acwright/6502-COB/CAD/Models/GPIO Helper/Rev 1.0/GPIO Helper.step

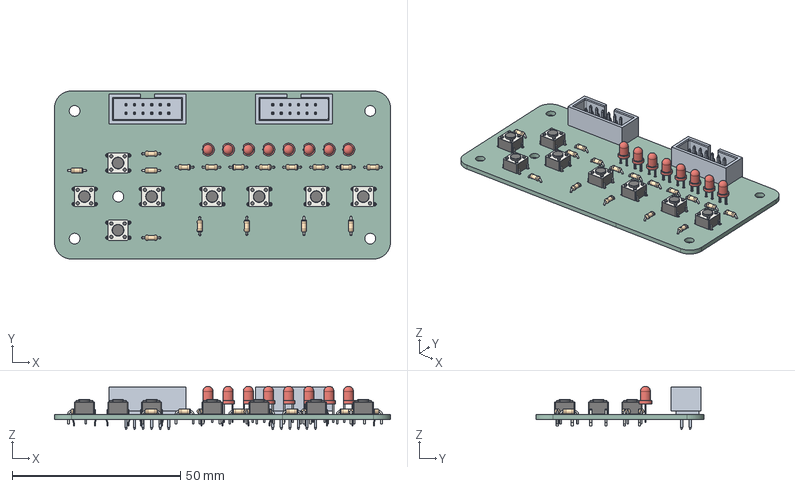
[picture p18: CAD file, 2026-05-05]
CAD/Models/GPIO Helper/Rev 1.0/GPIO Helper.step
100.0 x 50.0 x 12.9 mm
LED_D3.0mm x 8
R_Axial_DIN0204_L3.6mm_D1.6mm_P5.08mm_Horizontal x 16
SW_PUSH_6mm x 8
GPIO Helper_PCB
