acwright/6502-COB/CAD/Models/Joystick Helper/Rev 1.0/Joystick Helper.step

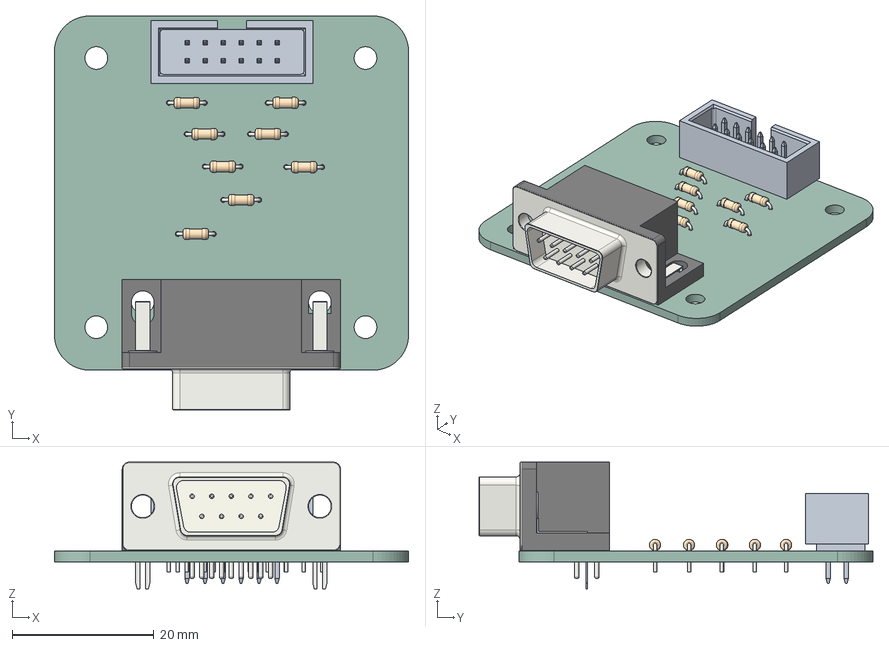
[picture p19: CAD file, 2026-05-05]
CAD/Models/Joystick Helper/Rev 1.0/Joystick Helper.step
50.0 x 55.6 x 17.9 mm
R_Axial_DIN0204_L3.6mm_D1.6mm_P5.08mm_Horizontal x 8
DSUB-9_Pins_Horizontal_P2.77x2.84mm_EdgePinOffset7.70mm_Housed_ MountingHolesOffset9.12mm
Joystick Helper_PCB
