acwright/6502-COB/CAD/Models/LCD Board/Rev 1.0/LCD Board.step

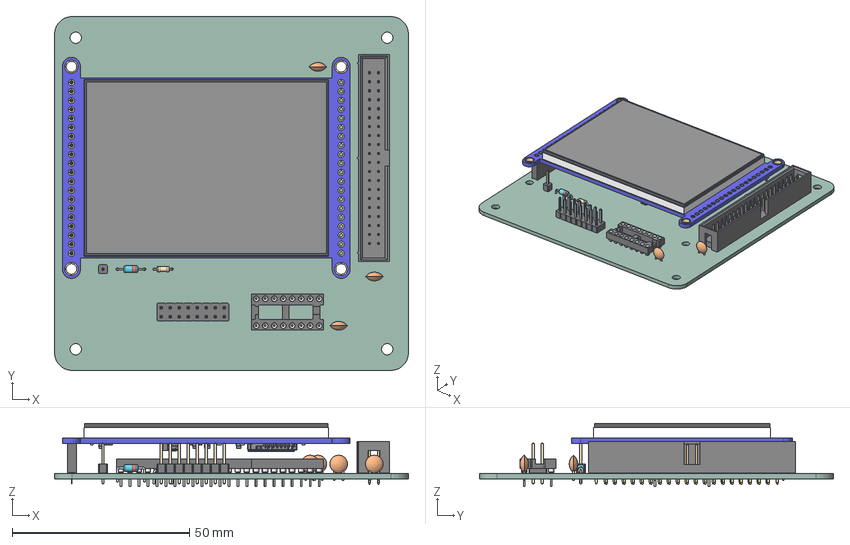
[picture p22: CAD file, 2026-05-05]
CAD/Models/LCD Board/Rev 1.0/LCD Board.step
100.0 x 100.0 x 17.9 mm
C_Disc_D5.0mm_W2.5mm_P2.50mm x 4
6871xx14022_PIN x 50
6871xx14022_Patte
6871xx14022_Patte_2
68715014022_CAP
6871xx149022_Pin x 18
6871xx149022_Patte
6871xx149022_Patte2
687118149022_Actuator
74LVC245 x 2
PinSocket_1x20_P2.54mm_Vertical
PinHeader_1x01_P2.54mm_Vertical
R_Axial_DIN0204_L3.6mm_D1.6mm_P5.08mm_Horizontal
DIP-16_W7.62mm_Socket
D_DO-35_SOD27_P7.62mm_Horizontal x 2
DIP-40_W15.24mm_Socket
PinHeader_2x08_P2.54mm_Vertical
6120xx21621_PIN x 40
LCD Board_PCB
