acwright/6502-COB/CAD/Models/LCD Card/Rev 1.0/LCD Card.step

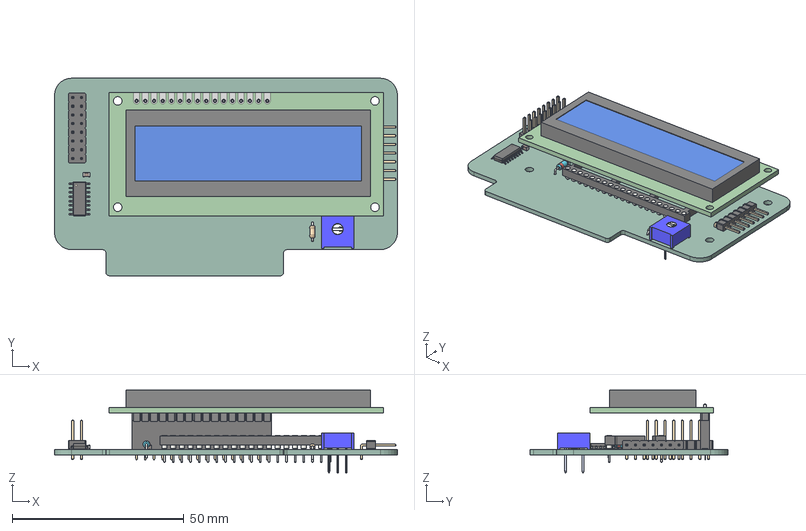
[picture p23: CAD file, 2026-05-05]
CAD/Models/LCD Card/Rev 1.0/LCD Card.step
100.0 x 57.6 x 24.2 mm
lcd 16_2 HD44780
dupont_pin_16
PinSocket_1x16_P2.54mm_Vertical
D_DO-35_SOD27_P7.62mm_Horizontal
3386F-1-103LF
R_Axial_DIN0204_L3.6mm_D1.6mm_P5.08mm_Horizontal
SOIC-16_3.9x9.9mm_P1.27mm
DIP-40_W15.24mm_Socket
PinHeader_2x08_P2.54mm_Vertical
C_0805_2012Metric x 2
PinHeader_1x07_P2.54mm_Horizontal
LCD Card_PCB
