acwright/6502-COB/CAD/Models/Prototype Card/Rev 1.0/Prototype Card.step

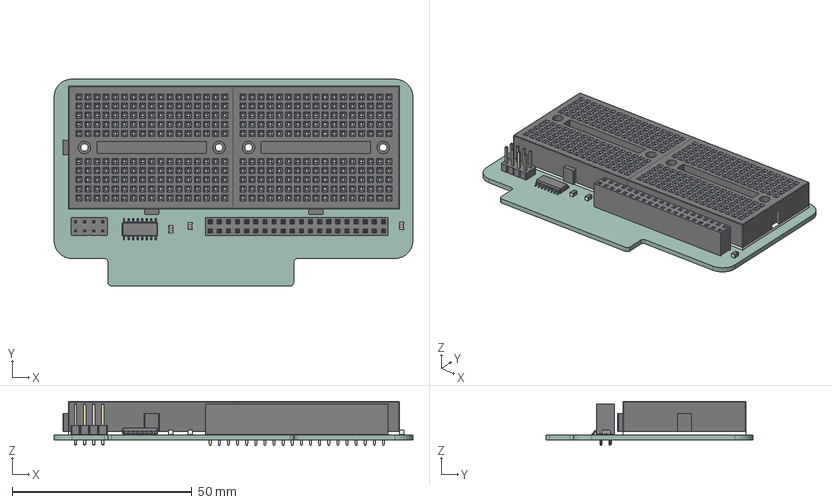
[picture p25: CAD file, 2026-05-05]
CAD/Models/Prototype Card/Rev 1.0/Prototype Card.step
100.0 x 57.6 x 12.3 mm
Mini-Black x 2
C_0805_2012Metric x 3
PinSocket_2x20_P2.54mm_Vertical
PinHeader_2x04_P2.54mm_Vertical
SOIC-16_3.9x9.9mm_P1.27mm
Prototype Card_PCB
