acwright/6502-COB/CAD/Models/PS2 Helper/Rev 1.0/PS2 Helper.step

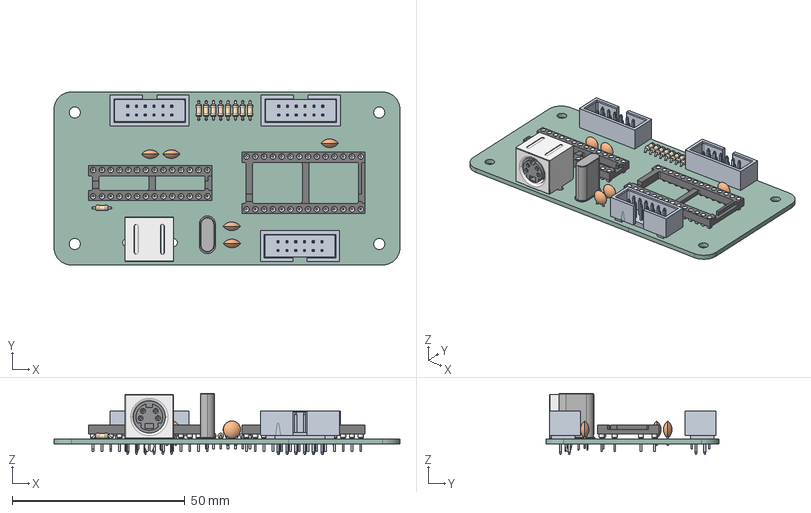
[picture p26: CAD file, 2026-05-05]
CAD/Models/PS2 Helper/Rev 1.0/PS2 Helper.step
100.0 x 50.0 x 17.7 mm
KMDGX-6S-BS
C_Disc_D5.0mm_W2.5mm_P2.50mm x 5
R_Axial_DIN0204_L3.6mm_D1.6mm_P5.08mm_Horizontal x 9
DIP-28_W7.62mm_Socket
DIP-28_W15.24mm_Socket
Crystal_HC49-U_Vertical
PS2 Helper_PCB
