acwright/6502-COB/CAD/Models/Serial Card/Rev 1.0/Serial Card.step

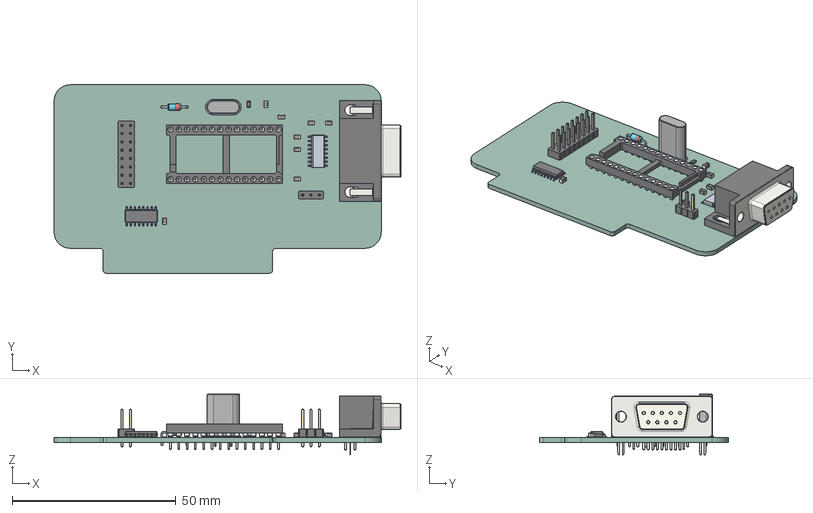
[picture p29: CAD file, 2026-05-05]
CAD/Models/Serial Card/Rev 1.0/Serial Card.step
106.0 x 57.6 x 18.5 mm
C_0805_2012Metric x 8
Crystal_HC49-U_Vertical
R_0805_2012Metric
Serial Card 1.9
SOIC-16_3.9x9.9mm_P1.27mm
DSUB-9_Socket_Horizontal_P2.77x2.84mm_EdgePinOffset7.70mm_Housed_ MountingHolesOffset9.12mm
DIP-28_W15.24mm_Socket
D_DO-35_SOD27_P7.62mm_Horizontal
PinHeader_2x08_P2.54mm_Vertical
PinHeader_1x03_P2.54mm_Vertical
Serial Card_PCB
