acwright/6502-COB/CAD/Models/Sound Card/Rev 1.0/Sound Card.step

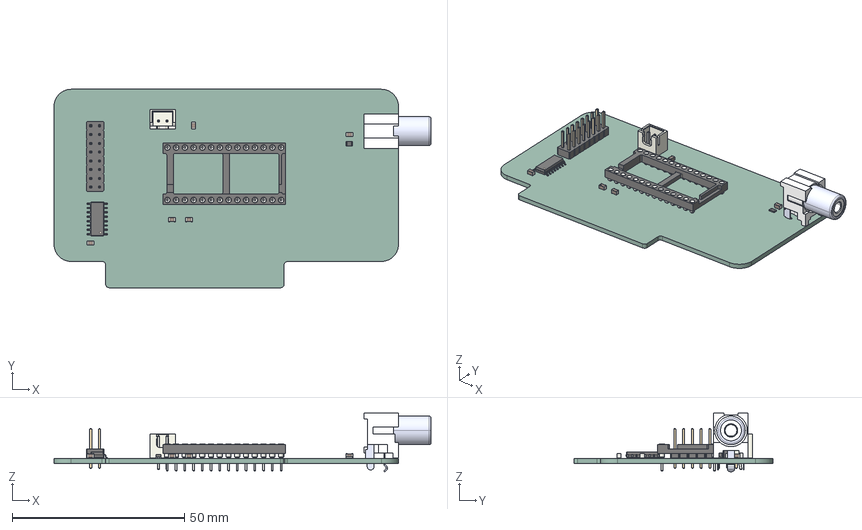
[picture p30: CAD file, 2026-05-05]
CAD/Models/Sound Card/Rev 1.0/Sound Card.step
109.4 x 57.6 x 17.0 mm
PinHeader_2x08_P2.54mm_Vertical
C_0805_2012Metric x 5
SOIC-16_3.9x9.9mm_P1.27mm
PJRAN1X1U04X-edit
R_0805_2012Metric
JST_XH_B2B-XH-A_1x02_P2.50mm_Vertical
DIP-28_W15.24mm_Socket
Sound Card_PCB
