acwright/6502-COB/CAD/Models/Storage Card Pro/Rev 1.0/Storage Card Pro.step

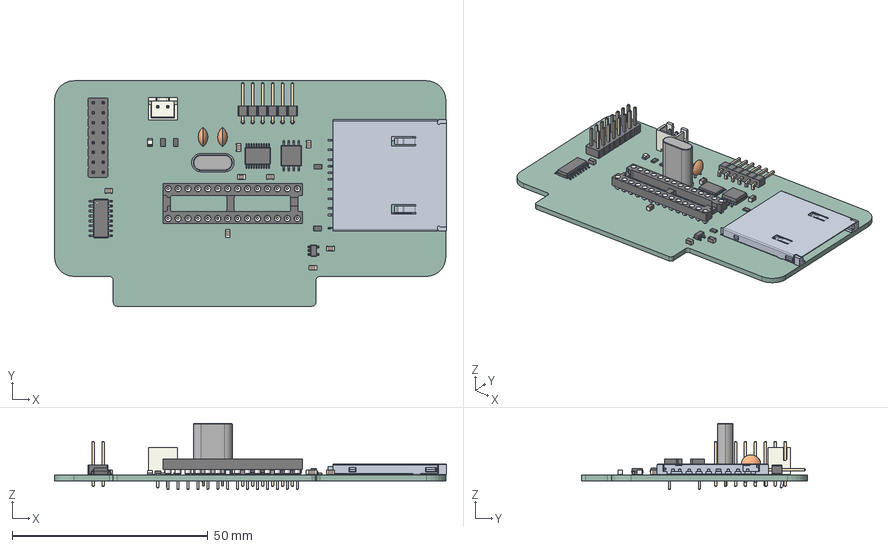
[picture p31: CAD file, 2026-05-05]
CAD/Models/Storage Card Pro/Rev 1.0/Storage Card Pro.step
100.2 x 57.6 x 16.9 mm
C_0805_2012Metric x 8
R_0805_2012Metric x 4
JST_XH_B2B-XH-A_1x02_P2.50mm_Vertical
C_Disc_D5.0mm_W2.5mm_P2.50mm x 2
SOT-23-5
SOIC-16_3.9x9.9mm_P1.27mm
PinHeader_2x08_P2.54mm_Vertical
TSSOP-20_4.4x6.5mm_P0.65mm
Storage Card Pro 1.13.1
PinHeader_1x06_P2.54mm_Horizontal
Crystal_HC49-U_Vertical
DIP-28_W7.62mm_Socket
SOIC-8_5.3x5.3mm_P1.27mm
LED_0805_2012Metric
Storage Card Pro_PCB
