acwright/6502-COB/CAD/Models/VERA Helper/Rev 1.0/VERA Helper.step

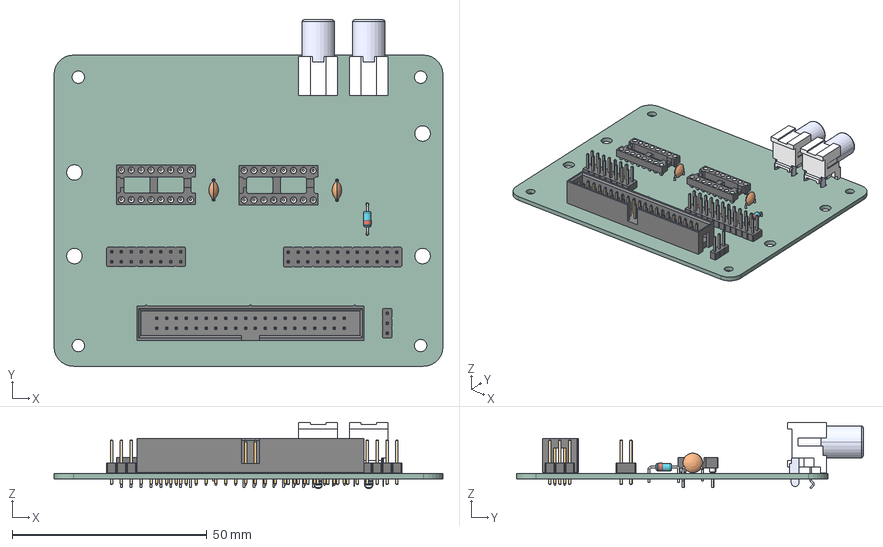
[picture p32: CAD file, 2026-05-05]
CAD/Models/VERA Helper/Rev 1.0/VERA Helper.step
100.0 x 89.1 x 17.0 mm
PinHeader_1x03_P2.54mm_Vertical
DIP-16_W7.62mm_Socket x 2
PinHeader_2x12_P2.54mm_Vertical
C_Disc_D5.0mm_W2.5mm_P5.00mm x 2
PJRAN1X1U04X-edit x 2
6120xx21621_PIN x 40
PinHeader_2x08_P2.54mm_Vertical
D_DO-35_SOD27_P7.62mm_Horizontal
VERA Helper_PCB
