acwright/6502-COB/CAD/Models/VGA Card Pro/Rev 1.0/VGA Card Pro.step

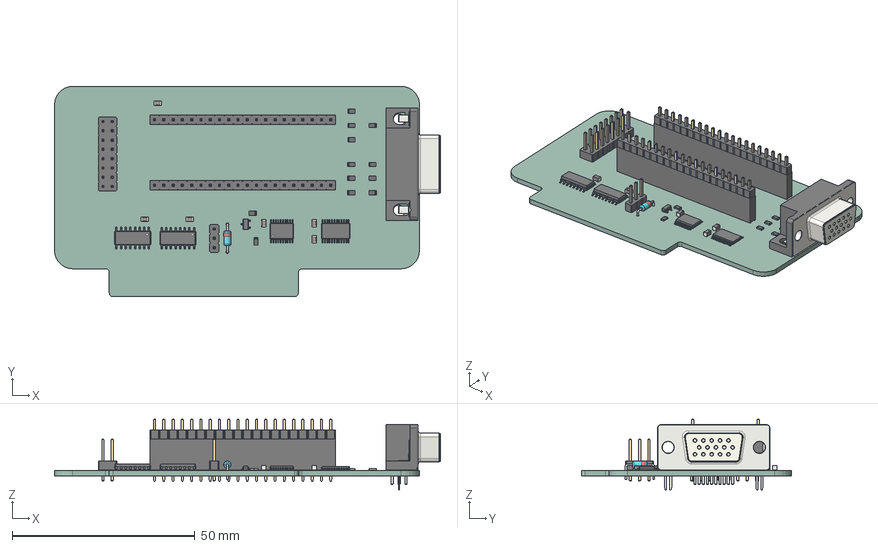
[picture p33: CAD file, 2026-05-05]
CAD/Models/VGA Card Pro/Rev 1.0/VGA Card Pro.step
105.8 x 57.6 x 19.4 mm
R_0805_2012Metric x 12
DSUB-15-HD_Socket_Horizontal_P2.29x1.90mm_EdgePinOffset3.03mm_Housed_ MountingHolesOffset4.94mm
TSSOP-24_4.4x7.8mm_P0.65mm
Raspberry Pi Pico
PinSocket_1x20_P2.54mm_Vertical x 2
PinHeader_1x20_P2.54mm_Vertical x 2
SOT-23
D_DO-35_SOD27_P7.62mm_Horizontal
C_0805_2012Metric x 6
PinHeader_2x08_P2.54mm_Vertical
PinHeader_1x03_P2.54mm_Vertical
TSSOP-20_4.4x6.5mm_P0.65mm
SOIC-16_3.9x9.9mm_P1.27mm x 2
VGA Card Pro_PCB
