acwright/6502-COB/CAD/Models/Video Card Pro/Rev 1.0/Video Card Pro.step

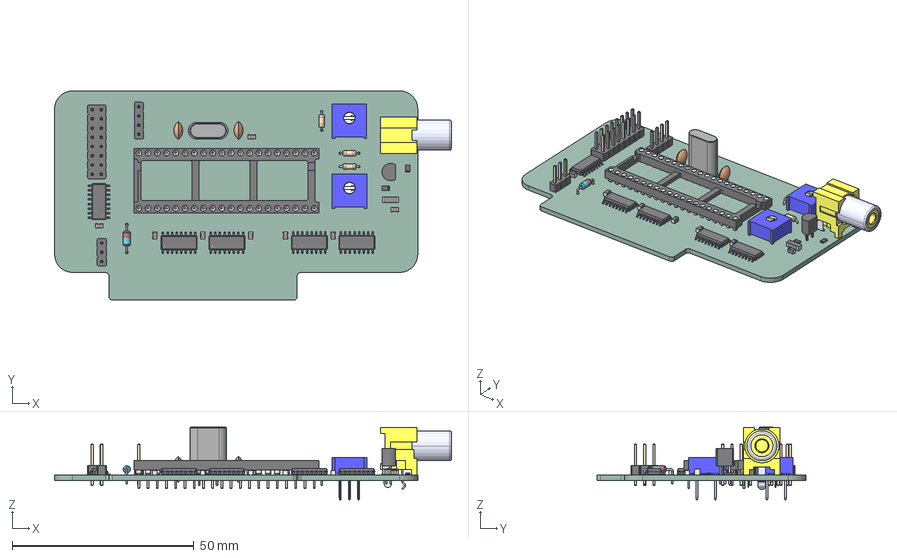
[picture p34: CAD file, 2026-05-05]
CAD/Models/Video Card Pro/Rev 1.0/Video Card Pro.step
109.3 x 57.6 x 20.0 mm
C_Disc_D5.0mm_W2.5mm_P2.50mm x 2
SOIC-16_3.9x9.9mm_P1.27mm x 5
TO-92
PinHeader_1x04_P2.54mm_Vertical
R_Axial_DIN0204_L3.6mm_D1.6mm_P5.08mm_Horizontal x 3
C_0805_2012Metric x 8
PinHeader_1x03_P2.54mm_Vertical
Crystal_HC49-U_Vertical
PJRAN1X1U04X-edit
D_DO-35_SOD27_P7.62mm_Horizontal
R_0805_2012Metric x 2
PinHeader_2x08_P2.54mm_Vertical
3386F-1-103LF x 2
DIP-40_W15.24mm_Socket
L_1806_4516Metric
Video Card Pro_PCB
