acwright/6502-COB/CAD/Models/Video Card/Rev 1.0/Video Card.step

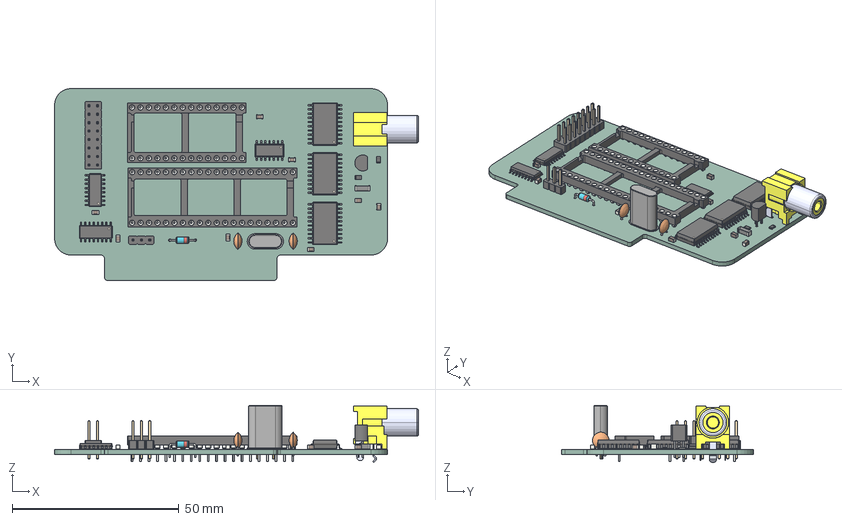
[picture p35: CAD file, 2026-05-05]
CAD/Models/Video Card/Rev 1.0/Video Card.step
109.3 x 57.6 x 17.1 mm
C_Disc_D5.0mm_W2.5mm_P2.50mm x 2
SOIC-20W_7.5x12.8mm_P1.27mm x 3
TO-92
C_0805_2012Metric x 8
DIP-28_W15.24mm_Socket
DIP-40_W15.24mm_Socket
PinHeader_1x03_P2.54mm_Vertical
Crystal_HC49-U_Vertical
SOIC-16_3.9x9.9mm_P1.27mm x 2
PJRAN1X1U04X-edit
D_DO-35_SOD27_P7.62mm_Horizontal
R_0805_2012Metric x 2
SO-14_3.9x8.65mm_P1.27mm
PinHeader_2x08_P2.54mm_Vertical
L_1806_4516Metric
Video Card_PCB
