acwright/6502-COB/Models/400MSP1R6BLKM6QE.step

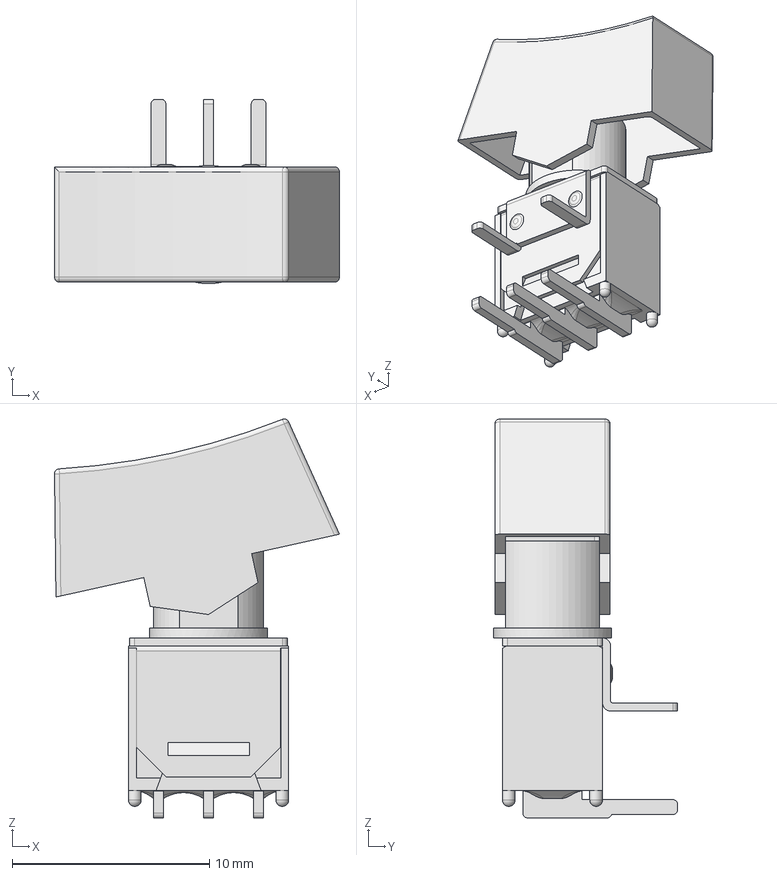
[picture p36: CAD file, 2026-06-21]
Models/400MSP1R6BLKM6QE.step
14.5 x 9.35 x 20.2 mm
