acwright/6502-COB/CAD/Bases/Center Support Retainer.stl

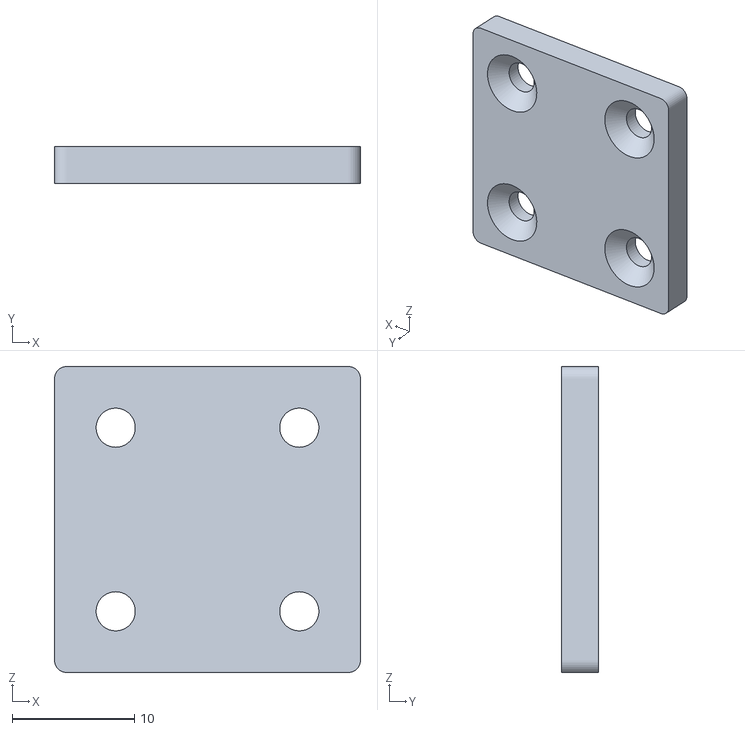
[picture p37: CAD file, 2026-05-05]
CAD/Bases/Center Support Retainer.stl
25.0 x 3.00 x 25.0
