acwright/6502-COB/CAD/Jigs/Keyboard Helper Jig Right.3mf

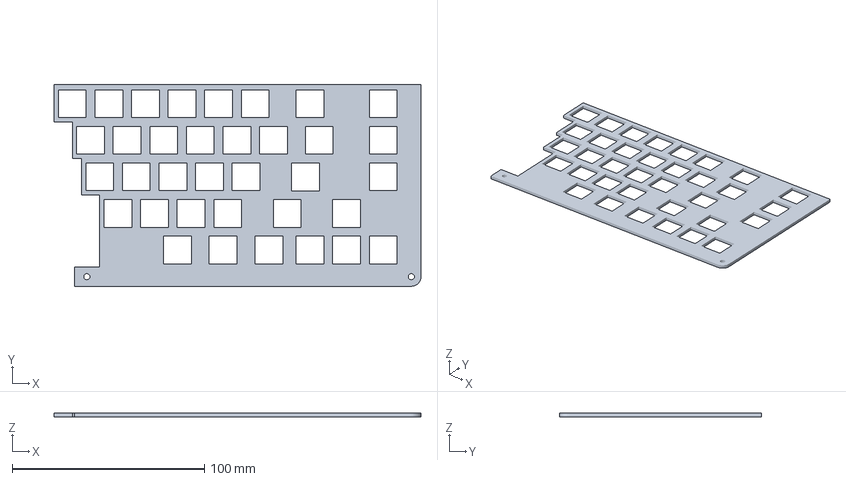
[picture p38: CAD file, 2026-05-19]
CAD/Jigs/Keyboard Helper Jig Right.3mf
191.1 x 105.0 x 2.00 mm
