acwright/6502-COB/CAD/Bases/Corner.3mf

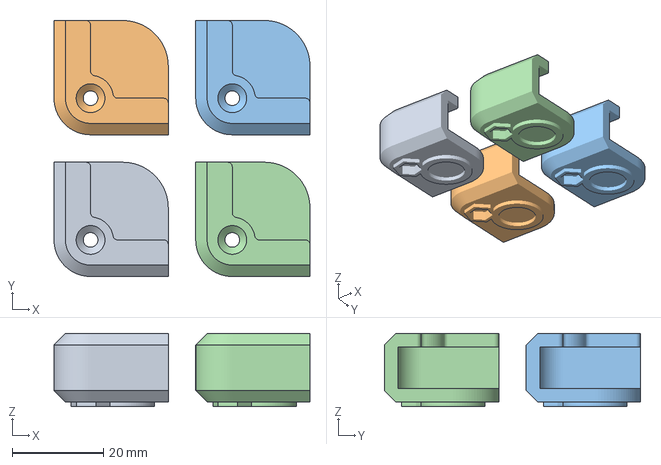
[picture p39: CAD file, 2026-05-05]
CAD/Bases/Corner.3mf
56.0 x 56.0 x 16.0 mm
