acwright/6502-COB/Models/KMDGX-6S-BS.step

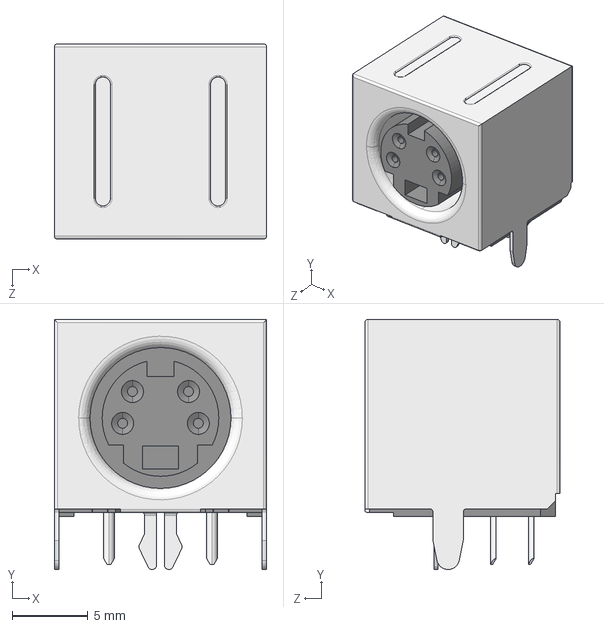
[picture p40: CAD file, 2026-05-05]
Models/KMDGX-6S-BS.step
14.0 x 16.5 x 12.9 mm
