acwright/6502-COB/CAD/Bases/Plate.stl

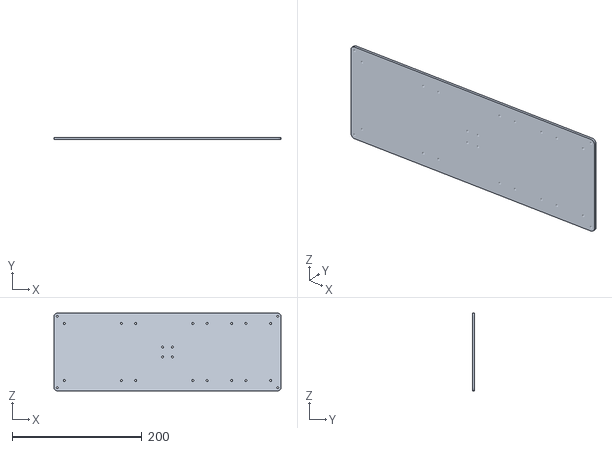
[picture p41: CAD file, 2026-05-05]
CAD/Bases/Plate.stl
350.0 x 3.00 x 120.0
