acwright/6502-COB/Models/HRO_TYPE-C-31-M-12.step

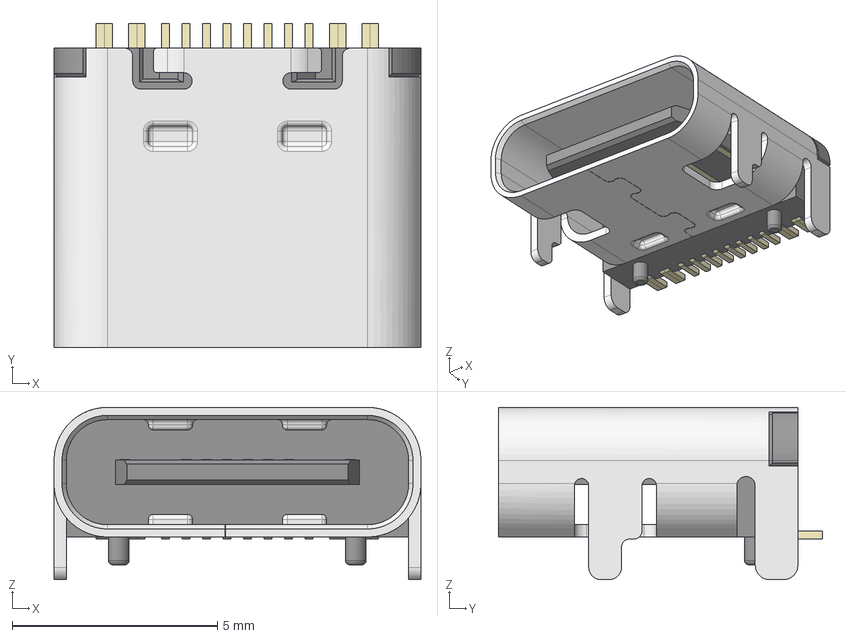
[picture p42: CAD file, 2026-05-05]
Models/HRO_TYPE-C-31-M-12.step
8.95 x 7.90 x 4.20 mm
