acwright/6502-COB/CAD/Bases/Button.3mf

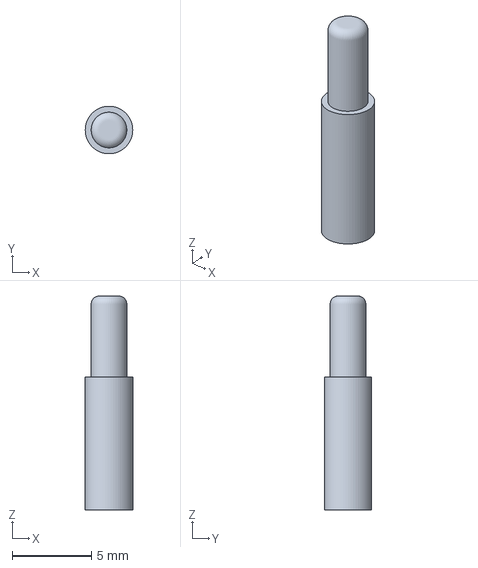
[picture p43: CAD file, 2026-05-05]
CAD/Bases/Button.3mf
3.00 x 3.00 x 13.5 mm
