acwright/6502-COB/Models/CherryMX.step

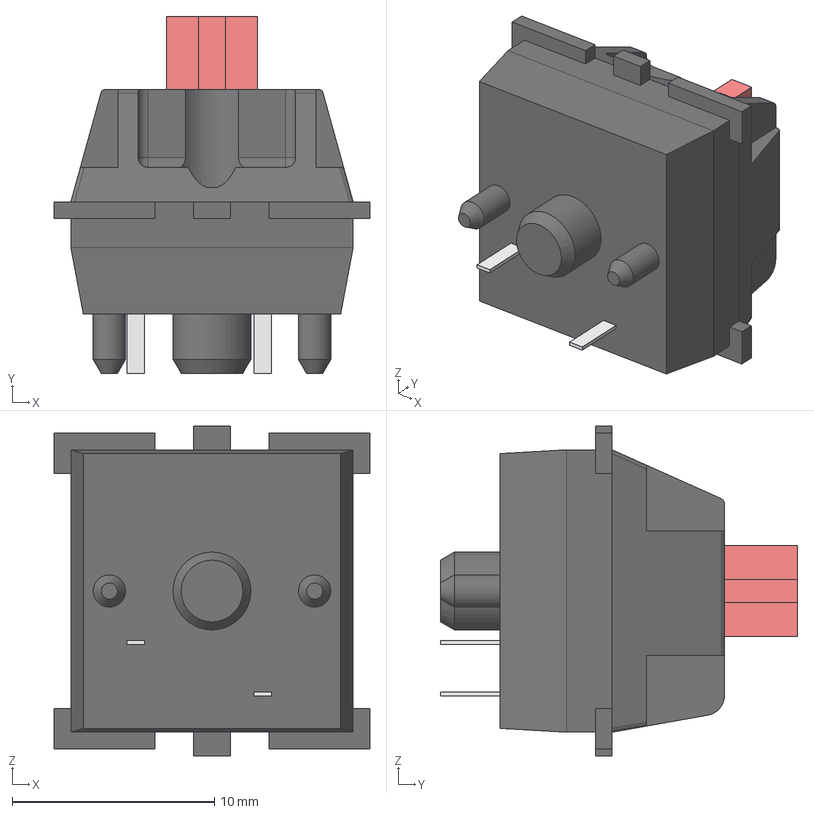
[picture p44: CAD file, 2026-05-05]
Models/CherryMX.step
15.6 x 17.7 x 16.3 mm
