acwright/6502-COB/Models/CFH-L3C1-1.step

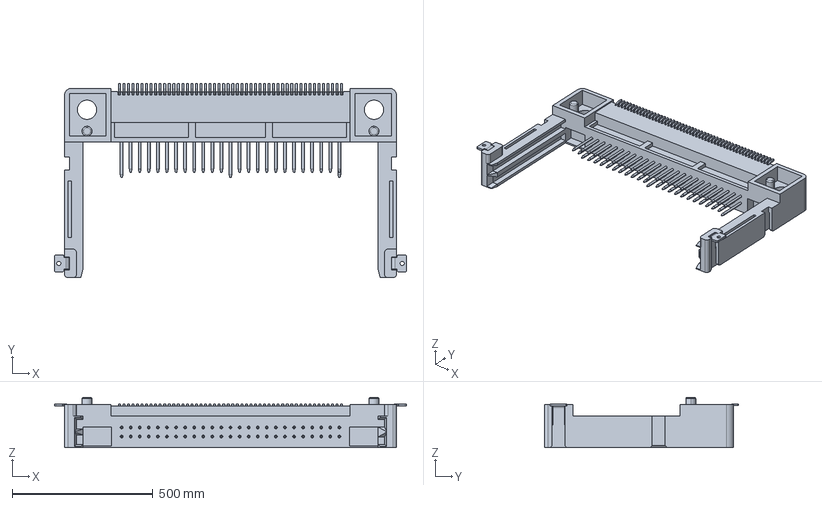
[picture p45: CAD file, 2026-05-05]
Models/CFH-L3C1-1.step
1251.2 x 690.9 x 179.1 mm
