acwright/6502-COB/Models/MAX232D.step

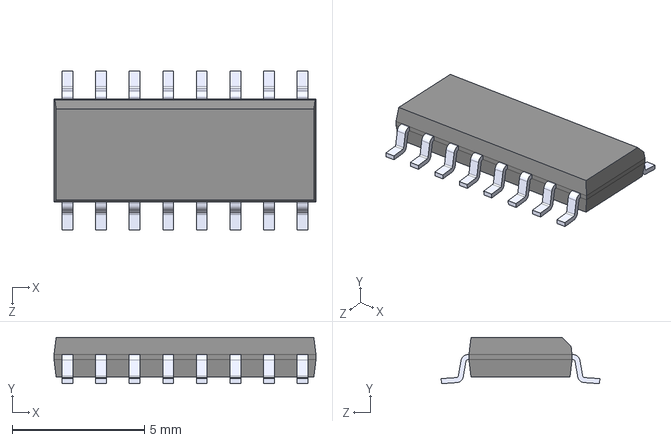
[picture p46: CAD file, 2026-05-05]
Models/MAX232D.step
9.90 x 1.75 x 6.00 mm
