acwright/6502-COB/Models/XKB5858.step

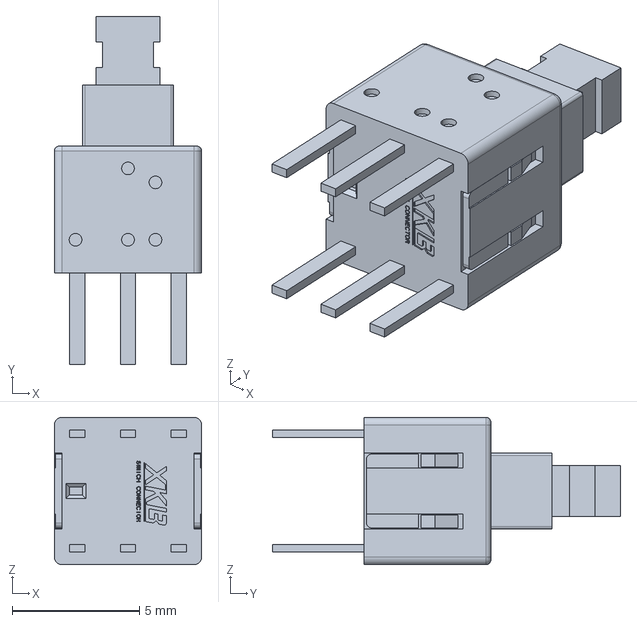
[picture p47: CAD file, 2026-05-05]
Models/XKB5858.step
5.80 x 13.7 x 5.80 mm
