acwright/6502-COB/Models/Adafruit 2.8 TFT LCD.step

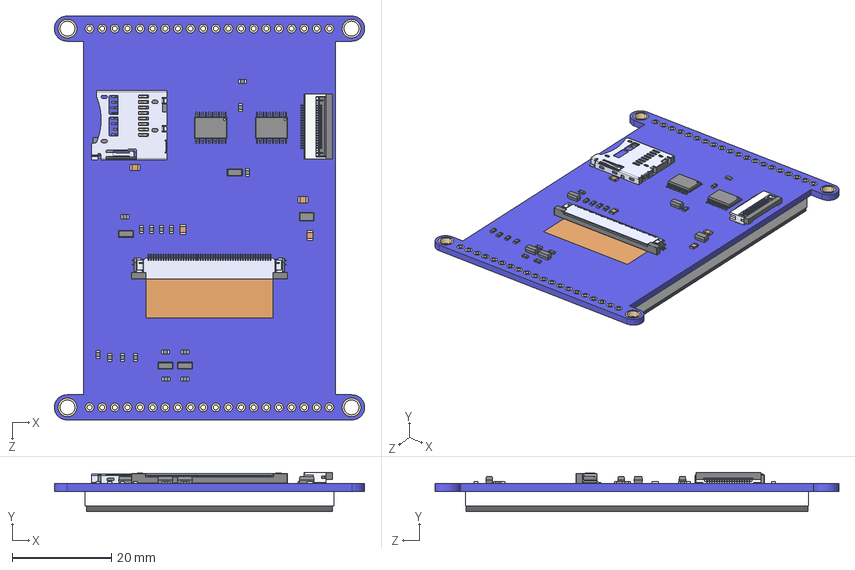
[picture p48: CAD file, 2026-05-05]
Models/Adafruit 2.8 TFT LCD.step
62.4 x 7.90 x 81.3 mm
6871xx14022_PIN x 50
6871xx14022_Patte
6871xx14022_Patte_2
68715014022_CAP
6871xx149022_Pin x 18
6871xx149022_Patte
6871xx149022_Patte2
687118149022_Actuator
74LVC245 x 2
