acwright/6502-COB/Models/TS-1187A-B-A-B.step

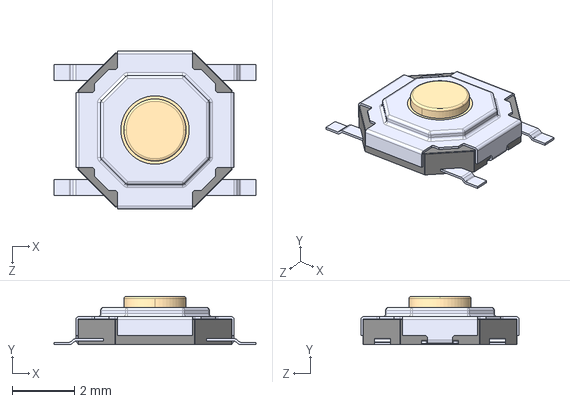
[picture p49: CAD file, 2026-05-05]
Models/TS-1187A-B-A-B.step
6.50 x 1.55 x 5.10 mm
