acwright/6502-COB/Models/5-5530843-4.step

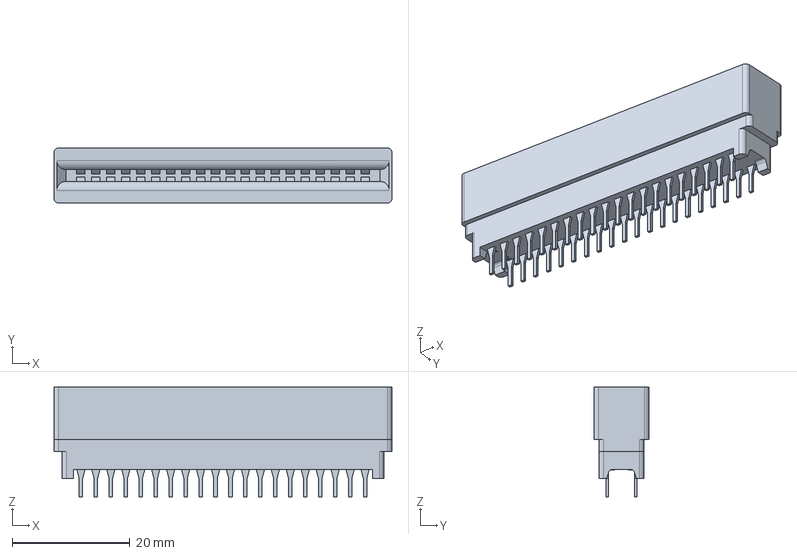
[picture p50: CAD file, 2026-05-05]
Models/5-5530843-4.step
57.4 x 9.35 x 18.7 mm
