acwright/6502-COB/Models/PJRAN1X1U02X.step

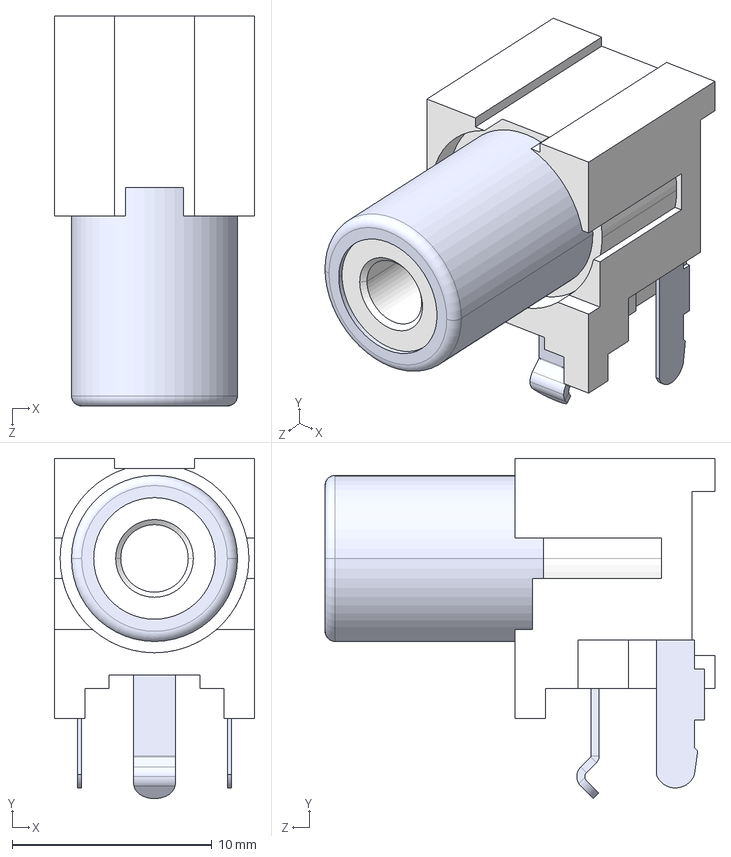
[picture p51: CAD file, 2026-05-05]
Models/PJRAN1X1U02X.step
10.0 x 17.0 x 19.5 mm
