acwright/6502-COB/Models/Mini-Black.step

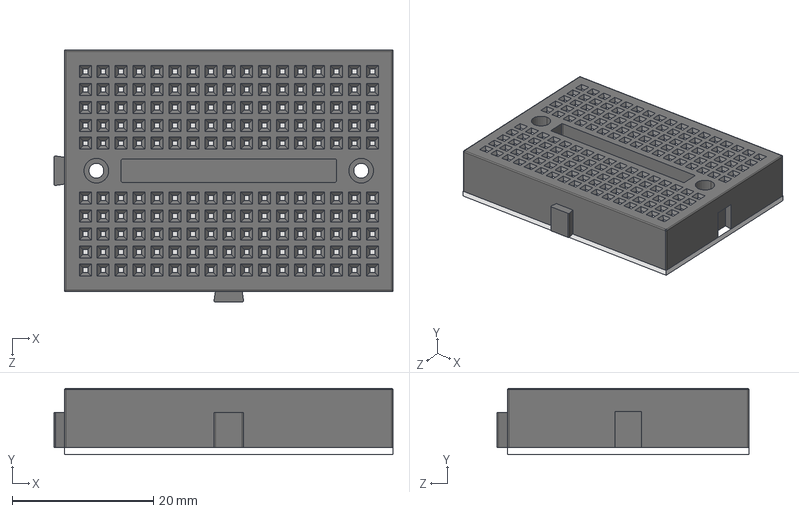
[picture p52: CAD file, 2026-05-05]
Models/Mini-Black.step
48.0 x 9.40 x 35.7 mm
