acwright/6502-COB/Models/3386F-1-103LF.step

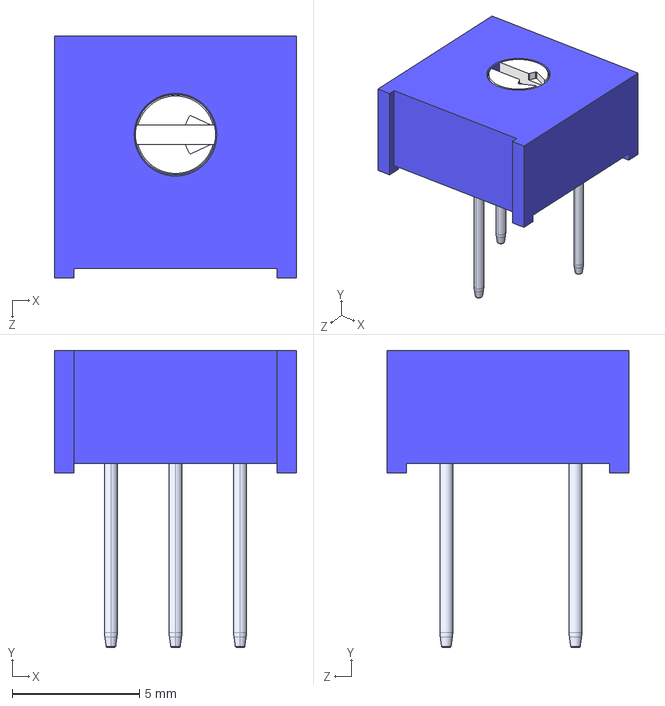
[picture p53: CAD file, 2026-05-05]
Models/3386F-1-103LF.step
9.53 x 11.7 x 9.53 mm
