acwright/6502-COB/Models/BAT-HLD-001-THM.step

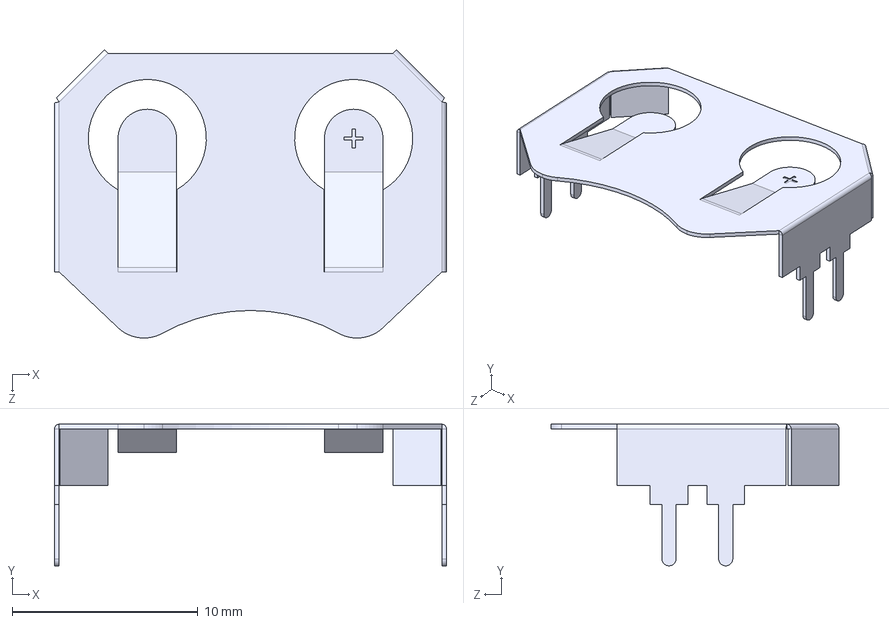
[picture p54: CAD file, 2026-05-05]
Models/BAT-HLD-001-THM.step
21.1 x 7.62 x 15.5 mm
