acwright/6502-COB/Schematics/Storage Card/Rev 1.0/Storage Card.pdf

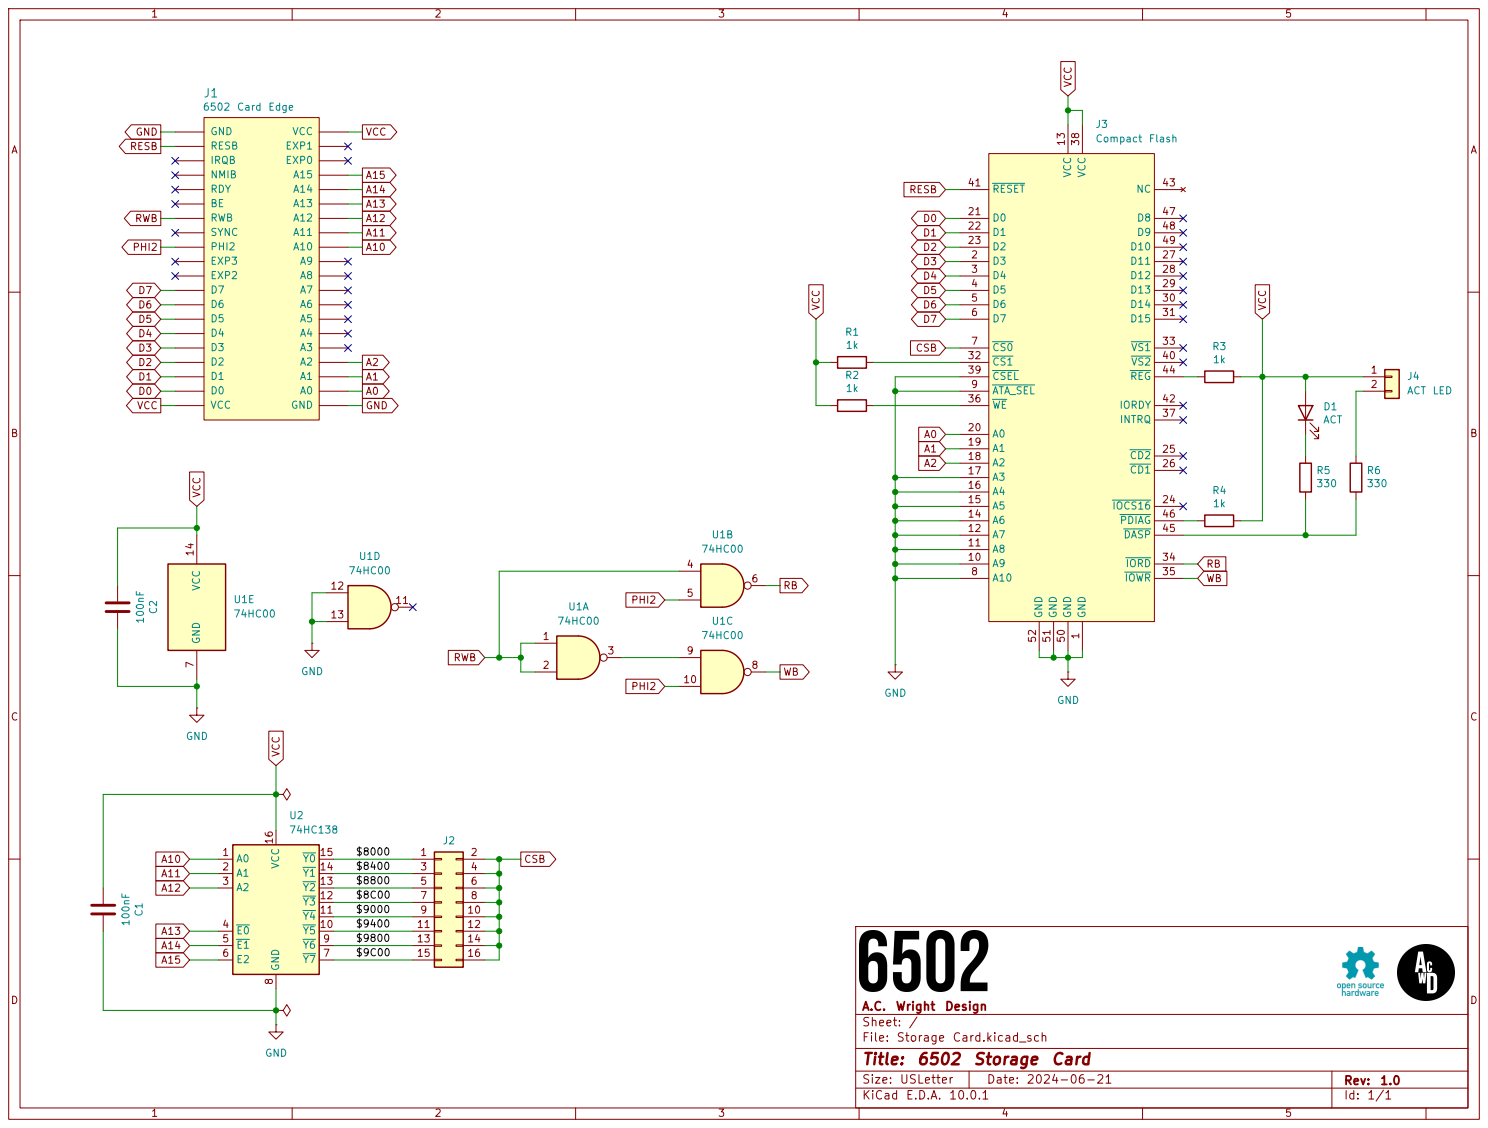
[picture p67: page 1]

Size: USLetter | Rev: 1.0
KiCad E.D.A. 10.0.1 | Id: 1/1
