acwright/6502-COB/Schematics/Backplane Pro/Rev 1.0/Backplane Pro.pdf

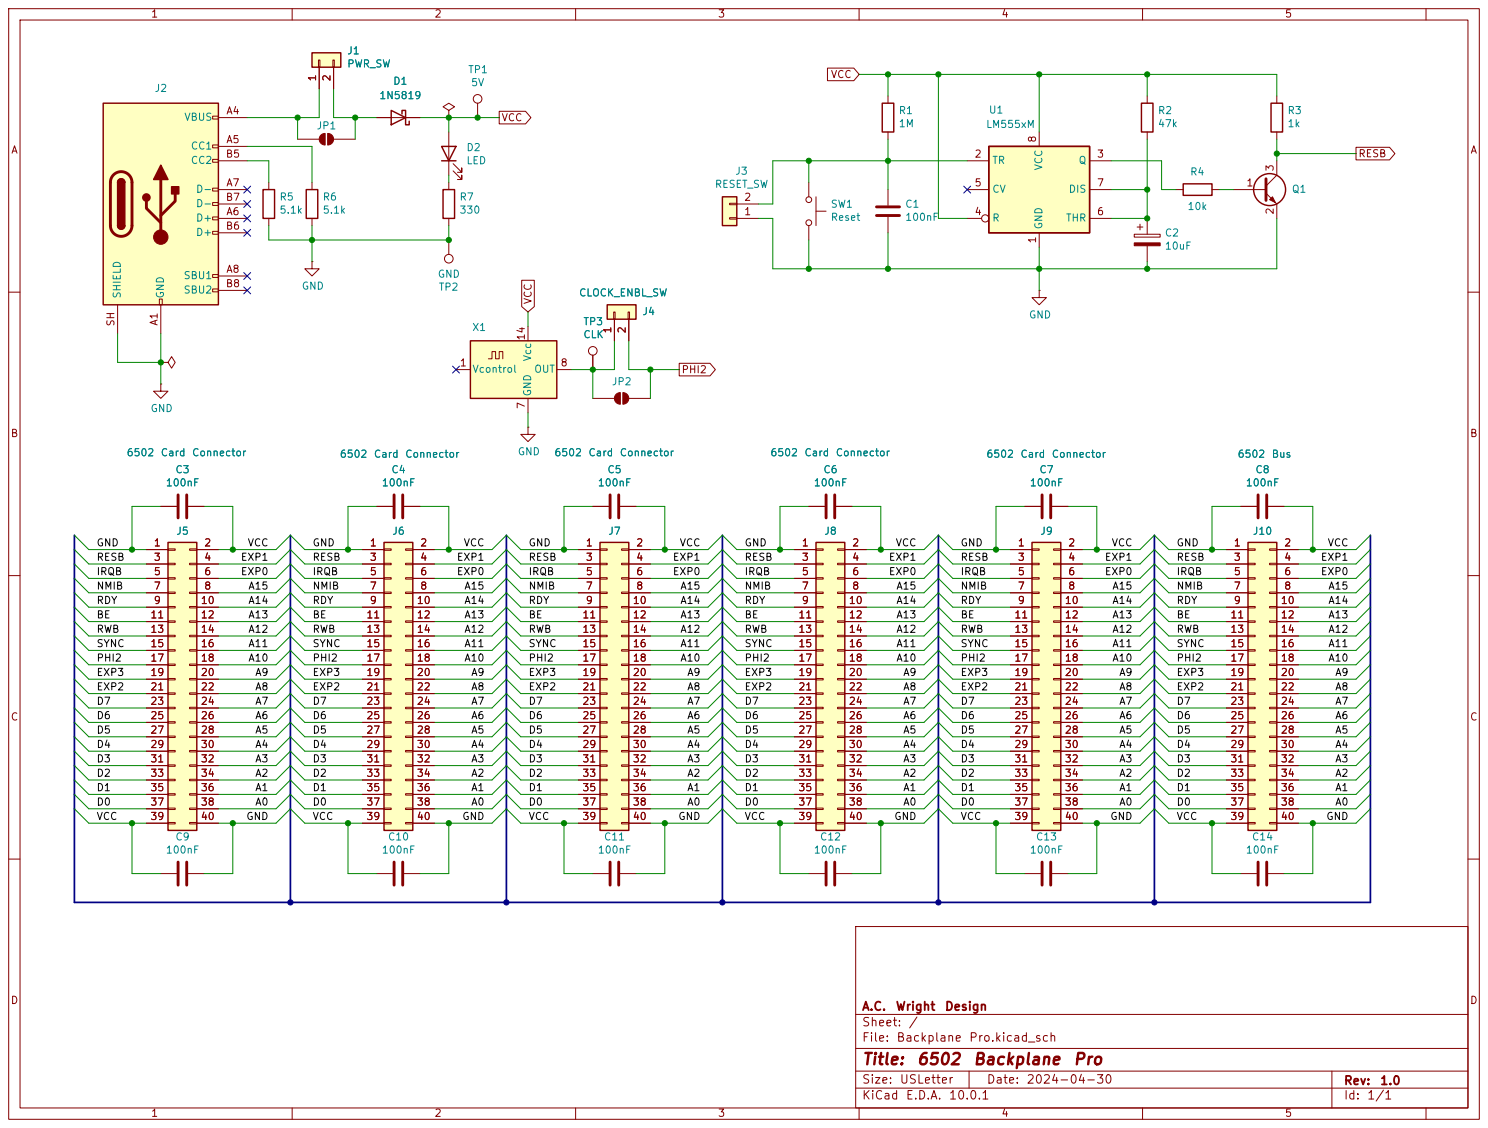
[picture p68: page 1]

Size: USLetter | Rev: 1.0
KiCad E.D.A. 10.0.1 | Id: 1/1
