acwright/6502-COB/Schematics/CPU Card/Rev 1.0/CPU Card.pdf

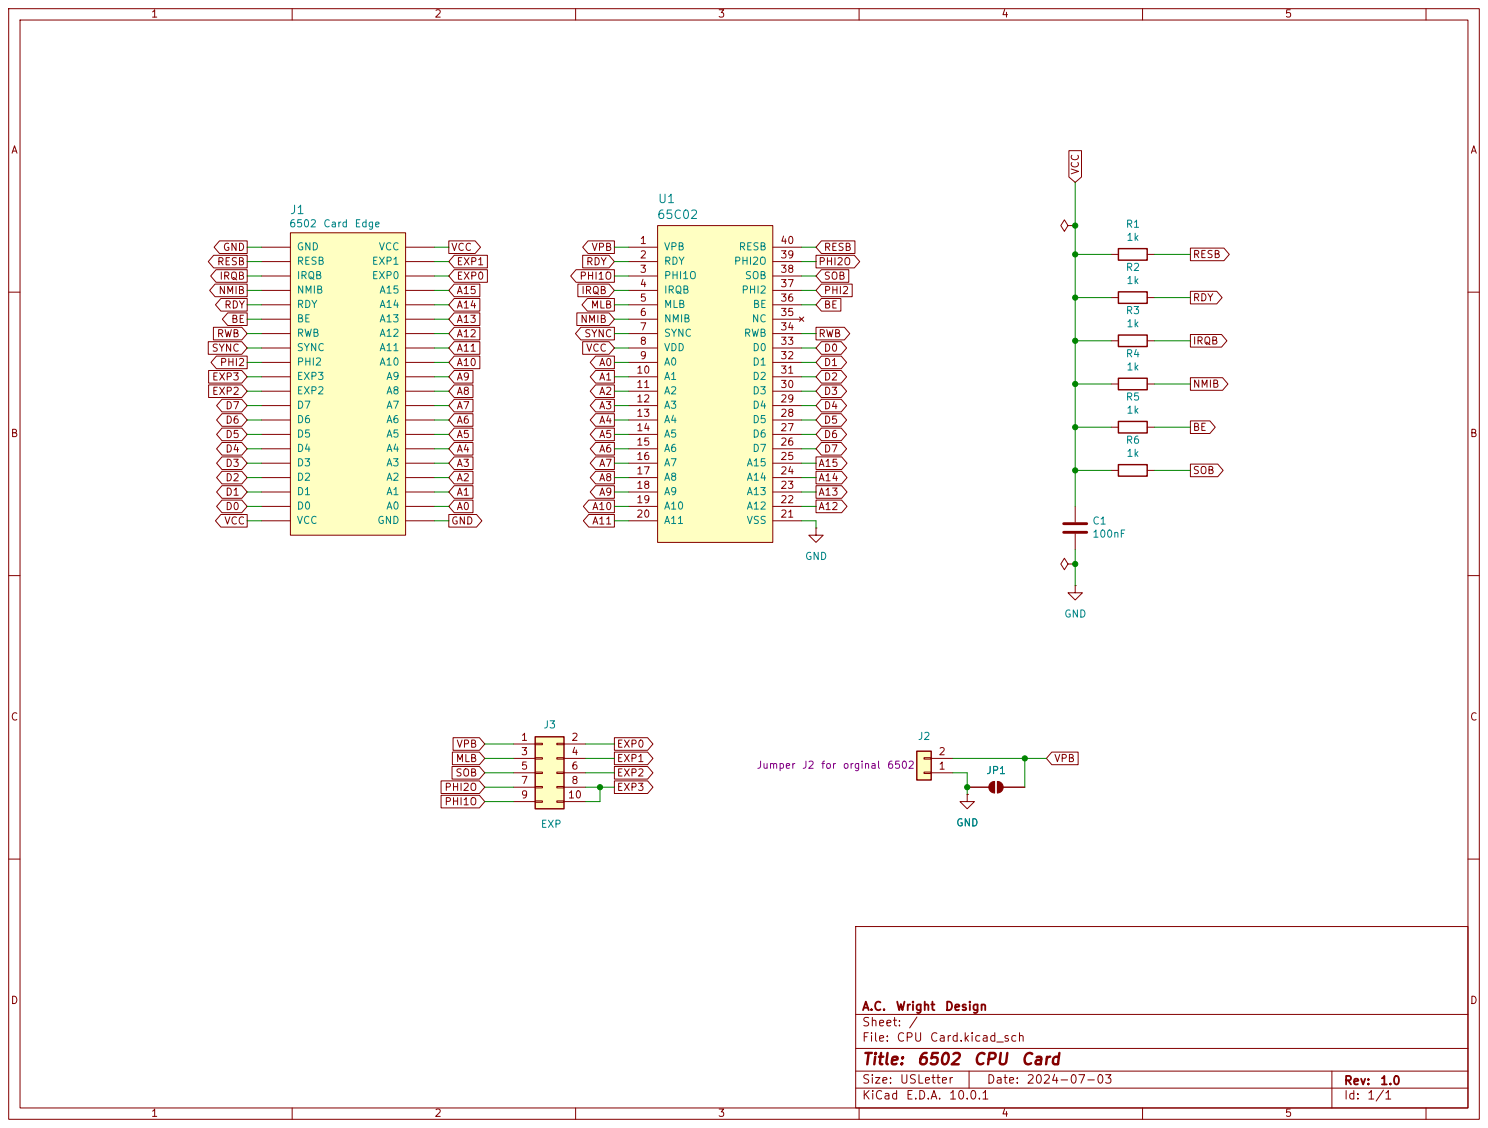
[picture p69: page 1]

Size: USLetter | Rev: 1.0
KiCad E.D.A. 10.0.1 | Id: 1/1
