acwright/6502-COB/Hardware/VGA Card/Rev 1.0/VGA Card.kicad_pcb

## KiCad design Hardware/VGA Card/Rev 1.0/VGA Card.kicad_pcb (2026-06-16)

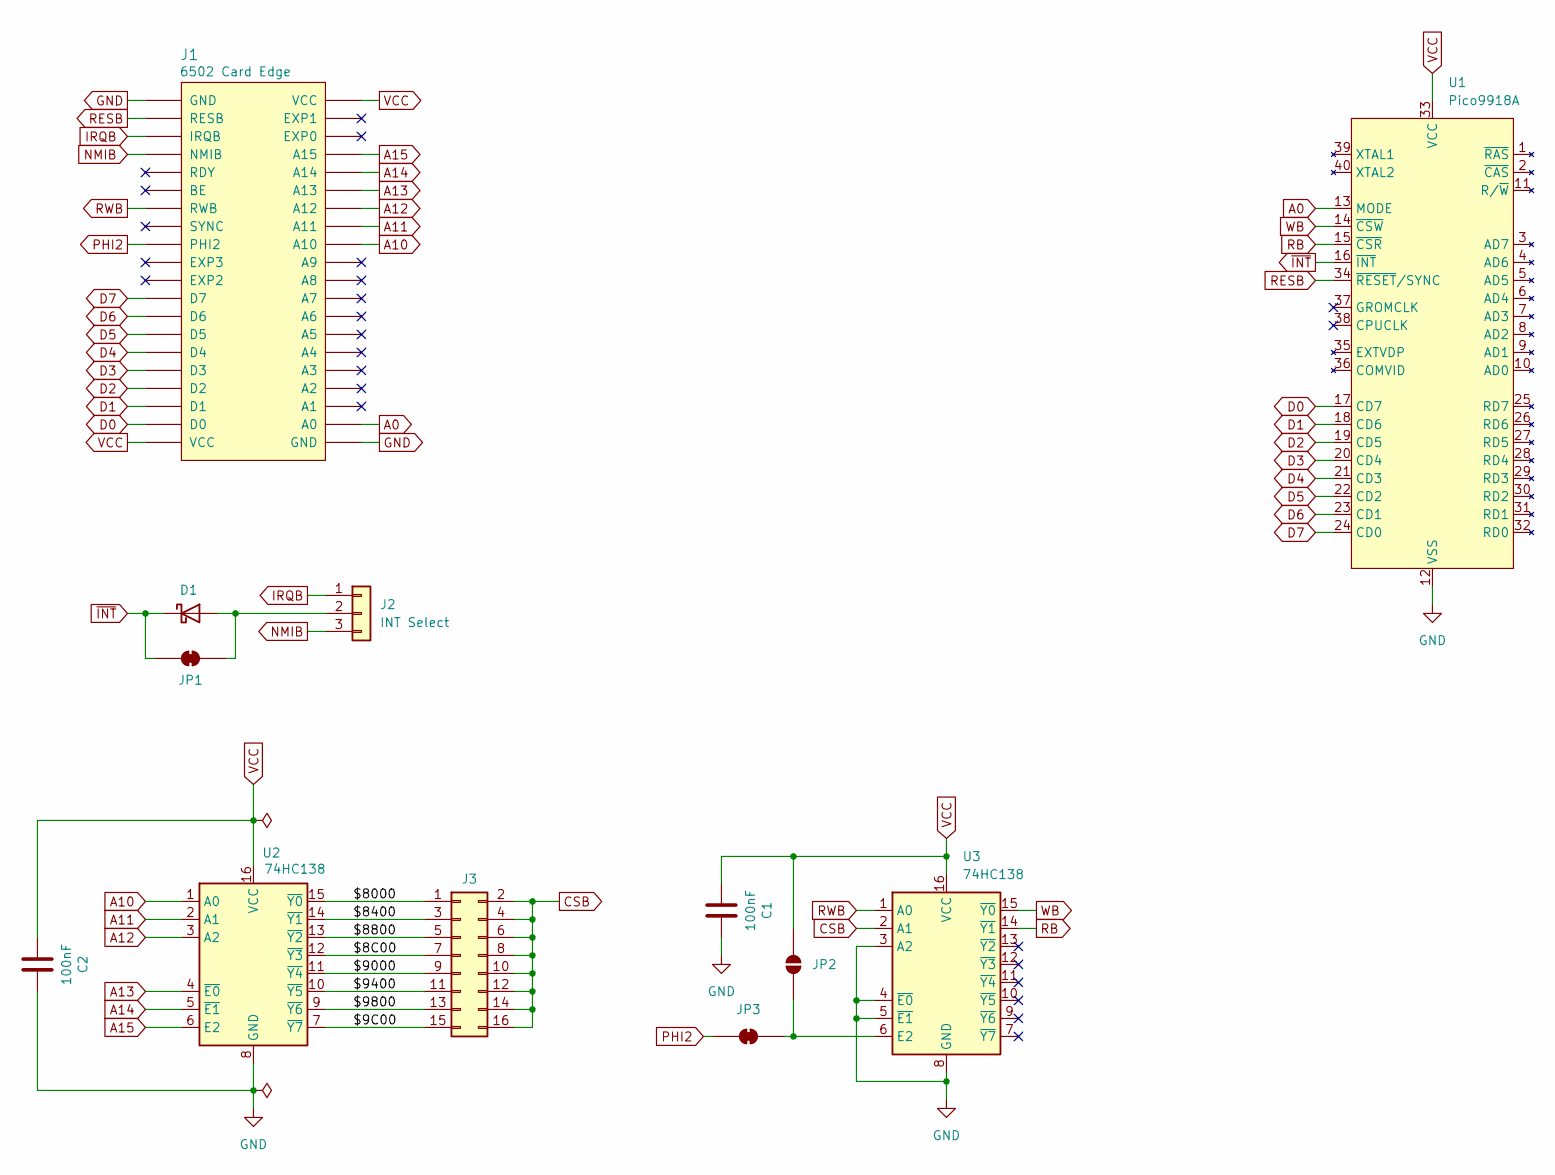
[picture p92: schematic VGA Card.kicad_sch, 6502 VGA Card]

Parts:
C1, C2: 100nF; C_0805_2012Metric; LCSC C49678
D1: D_Schottky; D_DO-35_SOD27_P7.62mm_Horizontal
J1: 6502 Card Edge
J2: INT Select; PinHeader_1x03_P2.54mm_Vertical
J3: Conn_02x08_Odd_Even; PinHeader_2x08_P2.54mm_Vertical
JP1, JP3: SolderJumper_2_Bridged; SolderJumper-2_P1.3mm_Bridged_RoundedPad1.0x1.5mm
JP2: SolderJumper_2_Open; SolderJumper-2_P1.3mm_Open_RoundedPad1.0x1.5mm
U1: Pico9918A; DIP-40_W15.24mm_LongPads
U2, U3: 74HC138; SOIC-16_3.9x9.9mm_P1.27mm; LCSC C5602

Connections:
/$8C00: J3.7, U2.12 (~Y3)
/$9C00: J3.15, U2.7 (~Y7)
/$8000: J3.1, U2.15 (~Y0)
/$8400: J3.3, U2.14 (~Y1)
/$8800: J3.5, U2.13 (~Y2)
/$9000: J3.9, U2.11 (~Y4)
/$9400: J3.11, U2.10 (~Y5)
/$9800: J3.13, U2.9 (~Y6)
A0: J1.A0, U1.13 (MODE)
A10: J1.A10, U2.1 (A0)
A11: J1.A11, U2.2 (A1)
A12: J1.A12, U2.3 (A2)
A13: J1.A13, U2.4 (~E0)
A14: J1.A14, U2.5 (~E1)
A15: J1.A15, U2.6 (E2)
CSB: J3.2, J3.4, J3.6, J3.8, J3.10, J3.12, J3.14, J3.16, U3.2 (A1)
D0: J1.D0, U1.17 (CD7)
D1: J1.D1, U1.18 (CD6)
D2: J1.D2, U1.19 (CD5)
D3: J1.D3, U1.20 (CD4)
D4: J1.D4, U1.21 (CD3)
D5: J1.D5, U1.22 (CD2)
D6: J1.D6, U1.23 (CD1)
D7: J1.D7, U1.24 (CD0)
GND: C1.2, C2.2, J1.GND, U1.12 (VSS), U2.8 (GND), U3.3 (A2), U3.4 (~E0), U3.5 (~E1), U3.8 (GND)
IRQB: J1.IRQB, J2.1
NMIB: J1.NMIB, J2.3
unnamed: D1.2 (A), J2.2, JP1.2 (B)
unnamed: JP2.2 (B), JP3.1 (A), U3.6 (E2)
PHI2: J1.PHI2, JP3.2 (B)
RB: U1.15 (~CSR), U3.14 (~Y1)
RESB: J1.RESB, U1.34 (~RESET/SYNC)
RWB: J1.RWB, U3.1 (A0)
VCC: C1.1, C2.1, J1.VCC, JP2.1 (A), U1.33 (VCC), U2.16 (VCC), U3.16 (VCC)
WB: U1.14 (~CSW), U3.15 (~Y0)
~INT: D1.1 (K), JP1.1 (A), U1.16 (~INT)

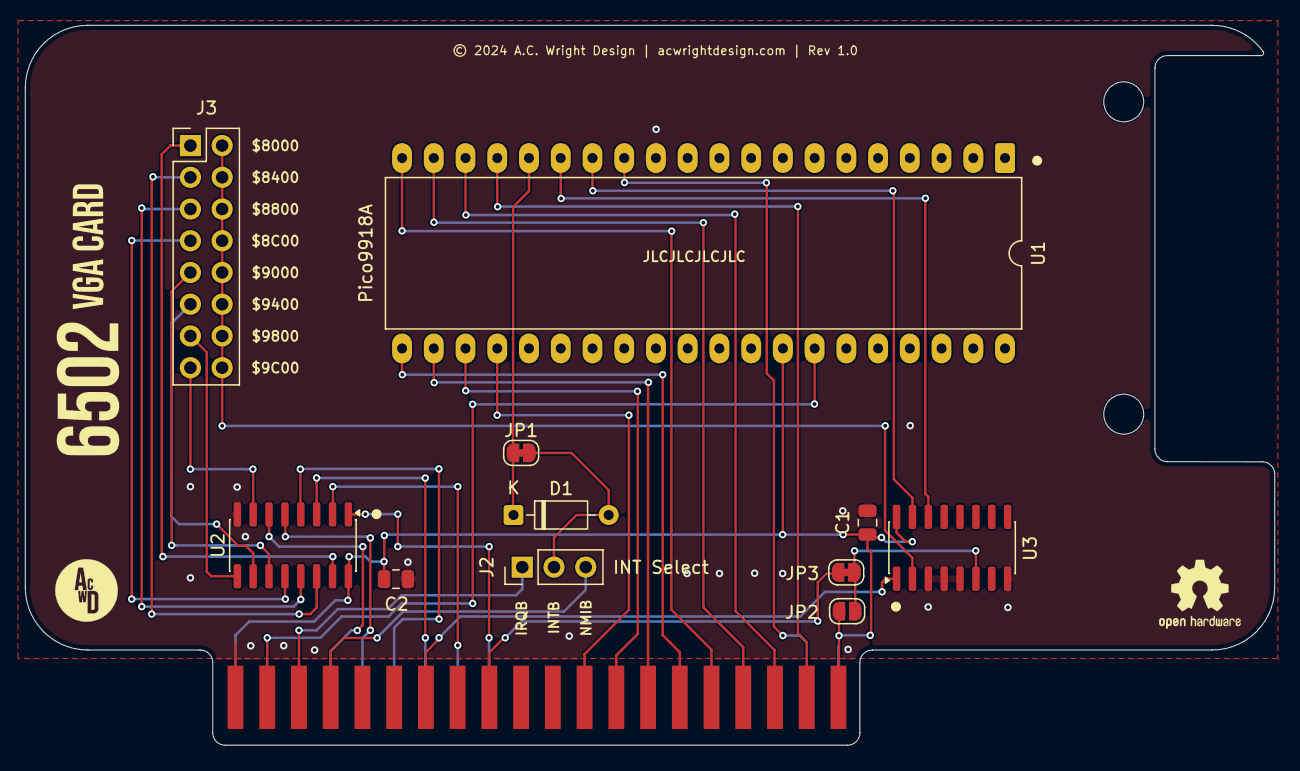
[picture p93: board VGA Card.kicad_pcb from above]

Board: 2 copper layers, 100.0 x 57.6 mm, 12 parts (0 on the bottom side), 36 nets.
