acwright/6502-COB/Hardware/Backplane Pro/Rev 1.0/Backplane Pro.kicad_pcb

## KiCad design Hardware/Backplane Pro/Rev 1.0/Backplane Pro.kicad_pcb (2026-06-16, an earlier design)

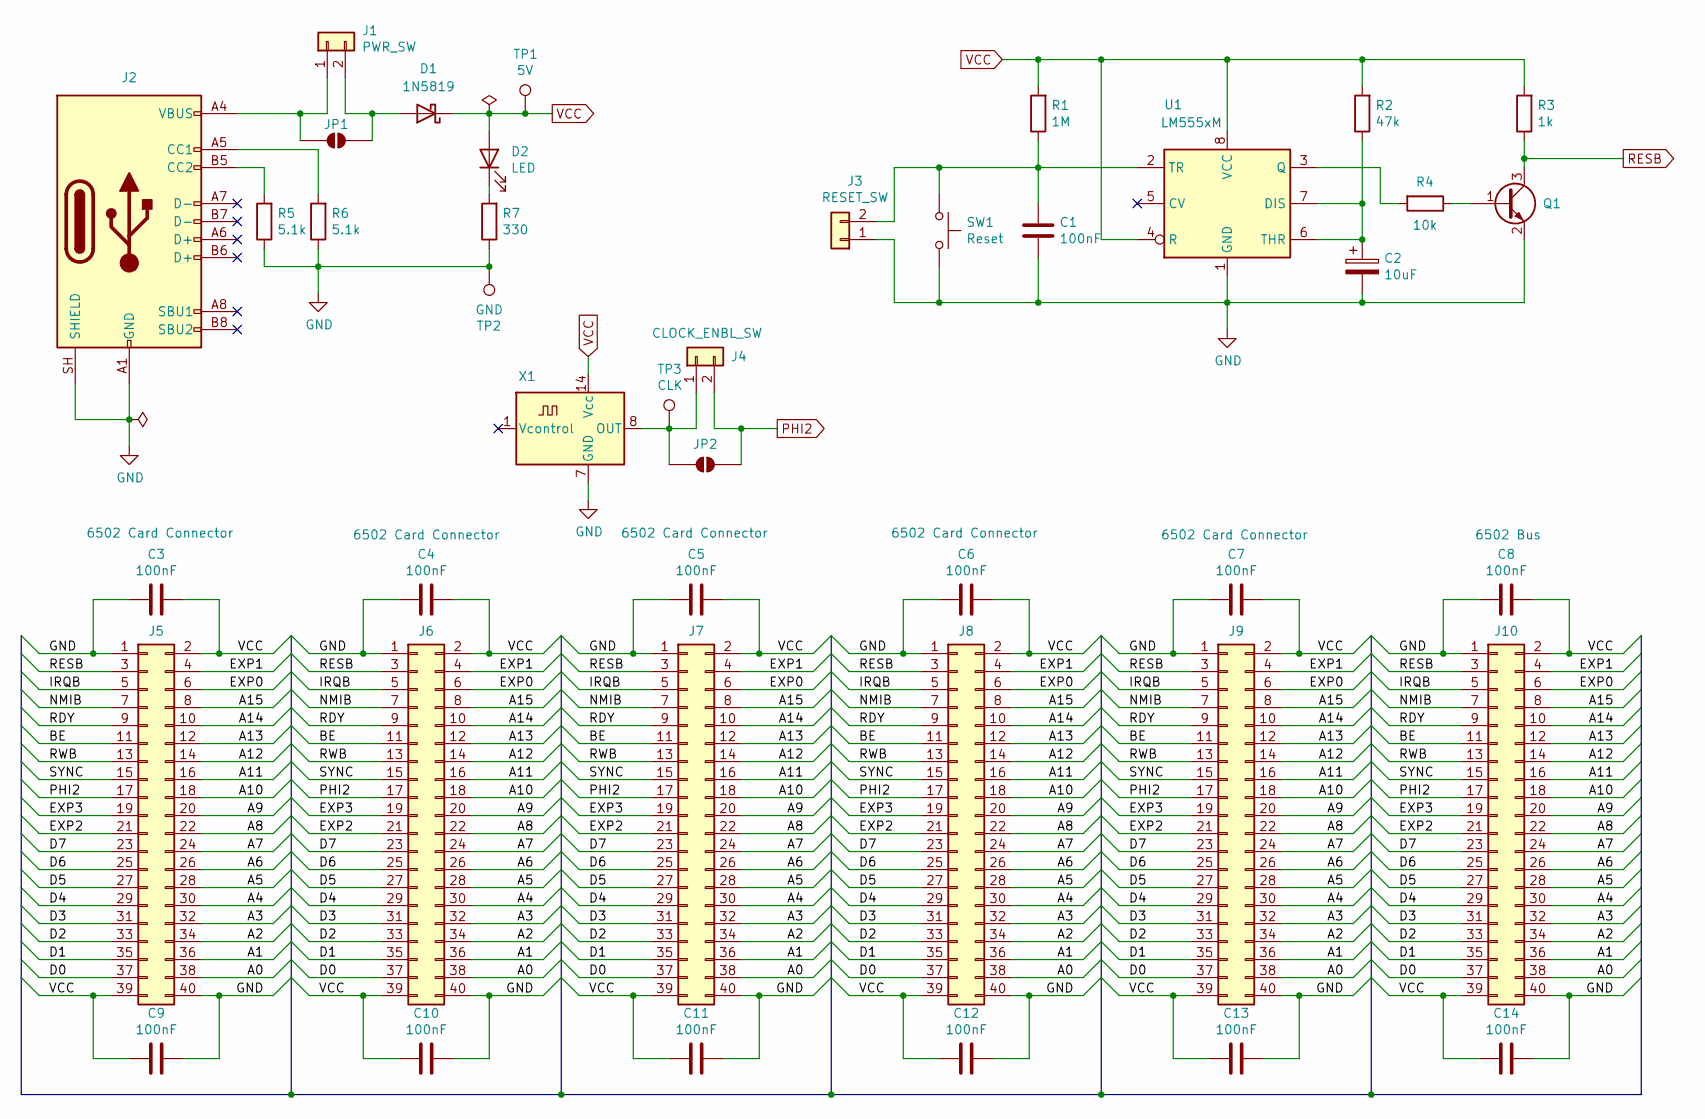
[picture p94: schematic Backplane Pro.kicad_sch, 6502 Backplane Pro]

Parts:
C1, C3, C4, C5, C6, C7, C8, C9, C10, C11, C12, C13, C14: 100nF; C_0805_2012Metric; LCSC C49678
C2: 10uF; C_1206_3216Metric; LCSC C7171
D1: 1N5819; D_SOD-323F; LCSC C191023
D2: LED; LED_0805_2012Metric; LCSC C2297
J1: PWR_SW; JST_XH_B2B-XH-A_1x02_P2.50mm_Vertical; Digikey 455-2247-ND
J2: USB_C_Receptacle_USB2.0; USB_C_Receptacle_HRO_TYPE-C-31-M-12; LCSC C2988369
J3: RESET_SW; JST_XH_B2B-XH-A_1x02_P2.50mm_Vertical; Digikey 455-2247-ND
J4: CLOCK_ENBL_SW; JST_XH_B2B-XH-A_1x02_P2.50mm_Vertical; Digikey 455-2247-ND
J5, J6, J7, J8, J9: 6502 Card Connector; RHDR40W82P485X254_2X20_5740X93; Mouser 571-5-5530843-4
J10: 6502 Bus; 6502 Bus Connector
JP1, JP2: SolderJumper_2_Open; SolderJumper-2_P1.3mm_Open_RoundedPad1.0x1.5mm
Q1: Q_NPN_BEC; SOT-23; LCSC C2150
R1: 1M; R_0805_2012Metric; LCSC C17514
R2: 47k; R_0805_2012Metric; LCSC C17713
R3: 1k; R_0805_2012Metric; LCSC C17513
R4: 10k; R_0805_2012Metric; LCSC C17414
R5, R6: 5.1k; R_0805_2012Metric; LCSC C27834
R7: 330; R_0805_2012Metric; LCSC C17630
SW1: Reset; SW_TS-1187A-B-A-B; LCSC C318884
TP1: 5V; TestPoint_Pad_1.0x1.0mm
TP2: GND; TestPoint_Pad_1.0x1.0mm
TP3: CLK; TestPoint_Pad_1.0x1.0mm
U1: LM555xM; SOIC-8_3.9x4.9mm_P1.27mm; LCSC C7593
X1: OCXO-14; Oscillator_DIP-14

Connections:
/A0: J5.38, J6.38, J7.38, J8.38, J9.38, J10.38
/A1: J5.36, J6.36, J7.36, J8.36, J9.36, J10.36
/A2: J5.34, J6.34, J7.34, J8.34, J9.34, J10.34
/A3: J5.32, J6.32, J7.32, J8.32, J9.32, J10.32
/A4: J5.30, J6.30, J7.30, J8.30, J9.30, J10.30
/A5: J5.28, J6.28, J7.28, J8.28, J9.28, J10.28
/A6: J5.26, J6.26, J7.26, J8.26, J9.26, J10.26
/A7: J5.24, J6.24, J7.24, J8.24, J9.24, J10.24
/A8: J5.22, J6.22, J7.22, J8.22, J9.22, J10.22
/A9: J5.20, J6.20, J7.20, J8.20, J9.20, J10.20
/A10: J5.18, J6.18, J7.18, J8.18, J9.18, J10.18
/A11: J5.16, J6.16, J7.16, J8.16, J9.16, J10.16
/A12: J5.14, J6.14, J7.14, J8.14, J9.14, J10.14
/A13: J5.12, J6.12, J7.12, J8.12, J9.12, J10.12
/A14: J5.10, J6.10, J7.10, J8.10, J9.10, J10.10
/A15: J5.8, J6.8, J7.8, J8.8, J9.8, J10.8
/BE: J5.11, J6.11, J7.11, J8.11, J9.11, J10.11
/D0: J5.37, J6.37, J7.37, J8.37, J9.37, J10.37
/D1: J5.35, J6.35, J7.35, J8.35, J9.35, J10.35
/D2: J5.33, J6.33, J7.33, J8.33, J9.33, J10.33
/D3: J5.31, J6.31, J7.31, J8.31, J9.31, J10.31
/D4: J5.29, J6.29, J7.29, J8.29, J9.29, J10.29
/D5: J5.27, J6.27, J7.27, J8.27, J9.27, J10.27
/D6: J5.25, J6.25, J7.25, J8.25, J9.25, J10.25
/D7: J5.23, J6.23, J7.23, J8.23, J9.23, J10.23
/EXP0: J5.6, J6.6, J7.6, J8.6, J9.6, J10.6
/EXP1: J5.4, J6.4, J7.4, J8.4, J9.4, J10.4
/EXP2: J5.21, J6.21, J7.21, J8.21, J9.21, J10.21
/EXP3: J5.19, J6.19, J7.19, J8.19, J9.19, J10.19
/IRQB: J5.5, J6.5, J7.5, J8.5, J9.5, J10.5
/NMIB: J5.7, J6.7, J7.7, J8.7, J9.7, J10.7
/RDY: J5.9, J6.9, J7.9, J8.9, J9.9, J10.9
/RWB: J5.13, J6.13, J7.13, J8.13, J9.13, J10.13
/SYNC: J5.15, J6.15, J7.15, J8.15, J9.15, J10.15
GND: C1.2, C2.2, C3.2, C4.2, C5.2, C6.2, C7.2, C8.2, C9.1, C10.1, C11.1, C12.1, C13.1, C14.1, J2.A1 (GND), J2.A12 (GND), J2.B1 (GND), J2.B12 (GND), J2.SH (SHIELD), J3.1, J5.1, J5.40, J6.1, J6.40, J7.1, J7.40, J8.1, J8.40, J9.1, J9.40, J10.1, J10.40, Q1.2 (E), R5.1, R6.1, R7.1, SW1.2, TP2.1 (1_1), U1.1 (GND), X1.7 (GND)
unnamed: D1.2 (A), J1.2, JP1.2 (B)
unnamed: D2.1 (K), R7.2
unnamed: J1.1, J2.A4 (VBUS), J2.A9 (VBUS), J2.B4 (VBUS), J2.B9 (VBUS), JP1.1 (A)
unnamed: J2.A5 (CC1), R6.2
unnamed: J2.B5 (CC2), R5.2
unnamed: C1.1, J3.2, R1.1, SW1.1, U1.2 (TR)
unnamed: J4.1, JP2.1 (A), TP3.1 (1_1), X1.8 (OUT)
unnamed: Q1.1 (B), R4.1
unnamed: C2.1, R2.1, U1.6 (THR), U1.7 (DIS)
unnamed: R4.2, U1.3 (Q)
PHI2: J4.2, J5.17, J6.17, J7.17, J8.17, J9.17, J10.17, JP2.2 (B)
RESB: J5.3, J6.3, J7.3, J8.3, J9.3, J10.3, Q1.3 (C), R3.1
VCC: C3.1, C4.1, C5.1, C6.1, C7.1, C8.1, C9.2, C10.2, C11.2, C12.2, C13.2, C14.2, D1.1 (K), D2.2 (A), J5.2, J5.39, J6.2, J6.39, J7.2, J7.39, J8.2, J8.39, J9.2, J9.39, J10.2, J10.39, R1.2, R2.2, R3.2, TP1.1 (1_1), U1.4 (R), U1.8 (VCC), X1.14 (Vcc)

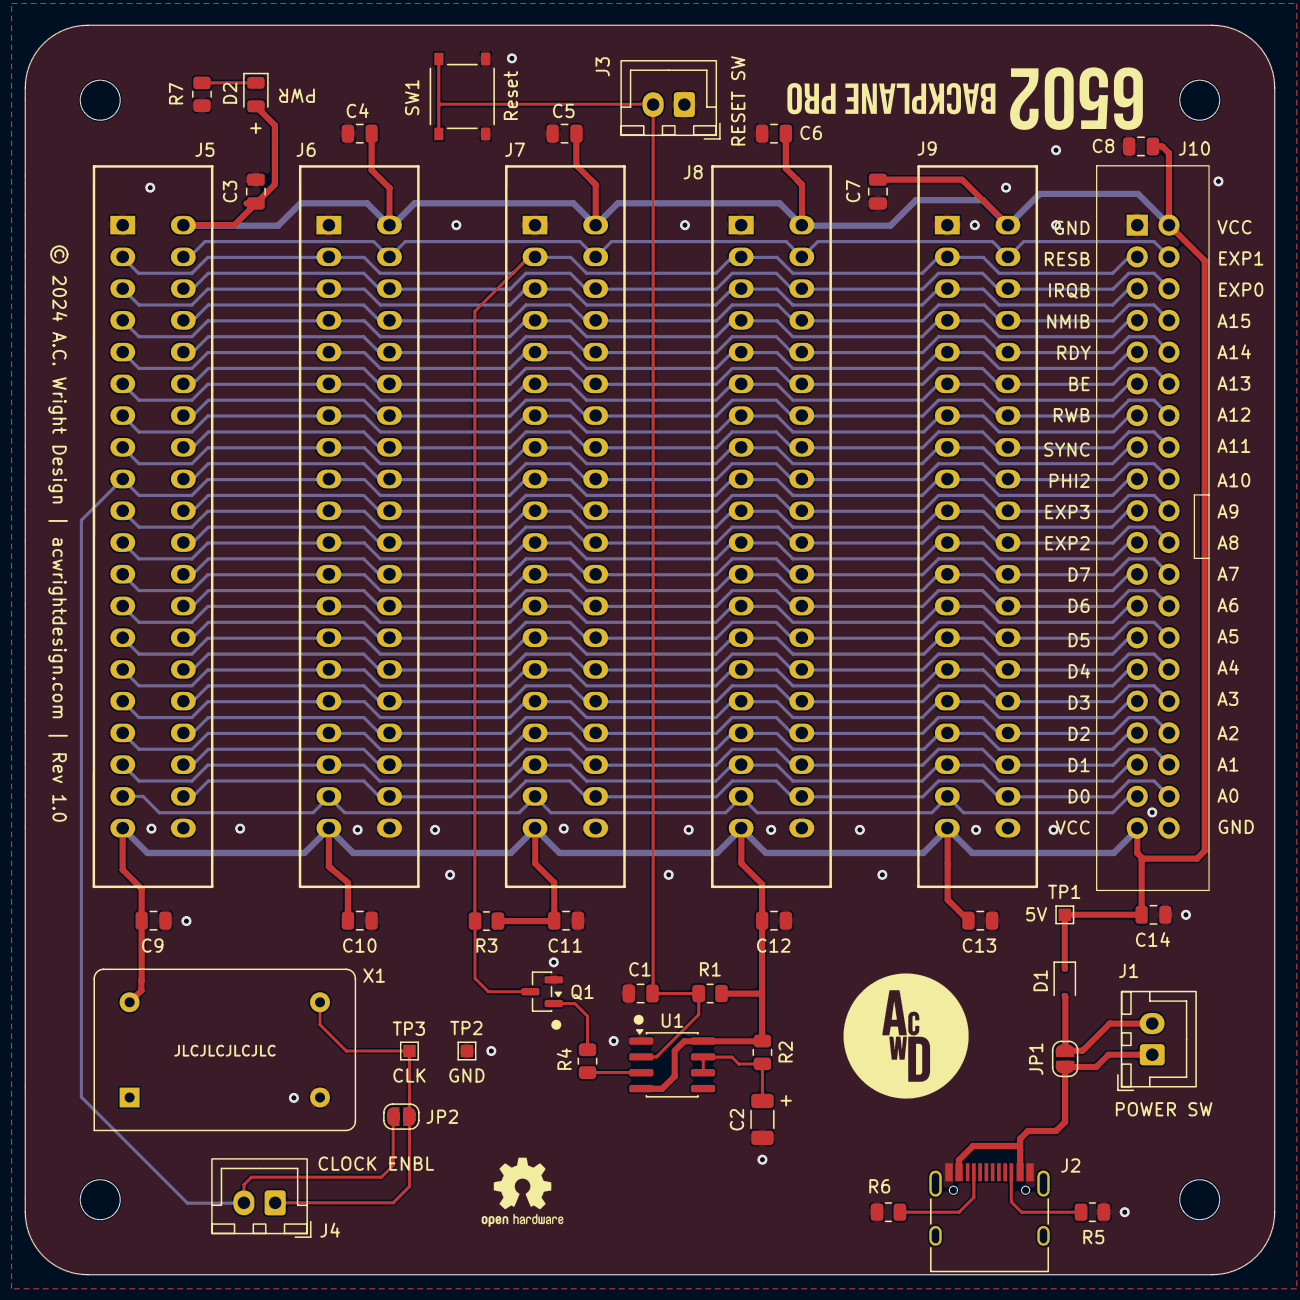
[picture p95: board Hardware/Backplane Pro/Rev 1.0/Backplane Pro.kicad_pcb from above]

Board: 2 copper layers, 100.0 x 100.0 mm, 46 parts (0 on the bottom side), 48 nets.

Other parts of the board:
H1, H2, H3, H4: MountingHole; MountingHole_3.2mm_M3
