acwright/6502-COB/Hardware/Clock Helper/Rev 1.0/Clock Helper.kicad_pcb

## KiCad design Hardware/Clock Helper/Rev 1.0/Clock Helper.kicad_pcb (2026-06-16)

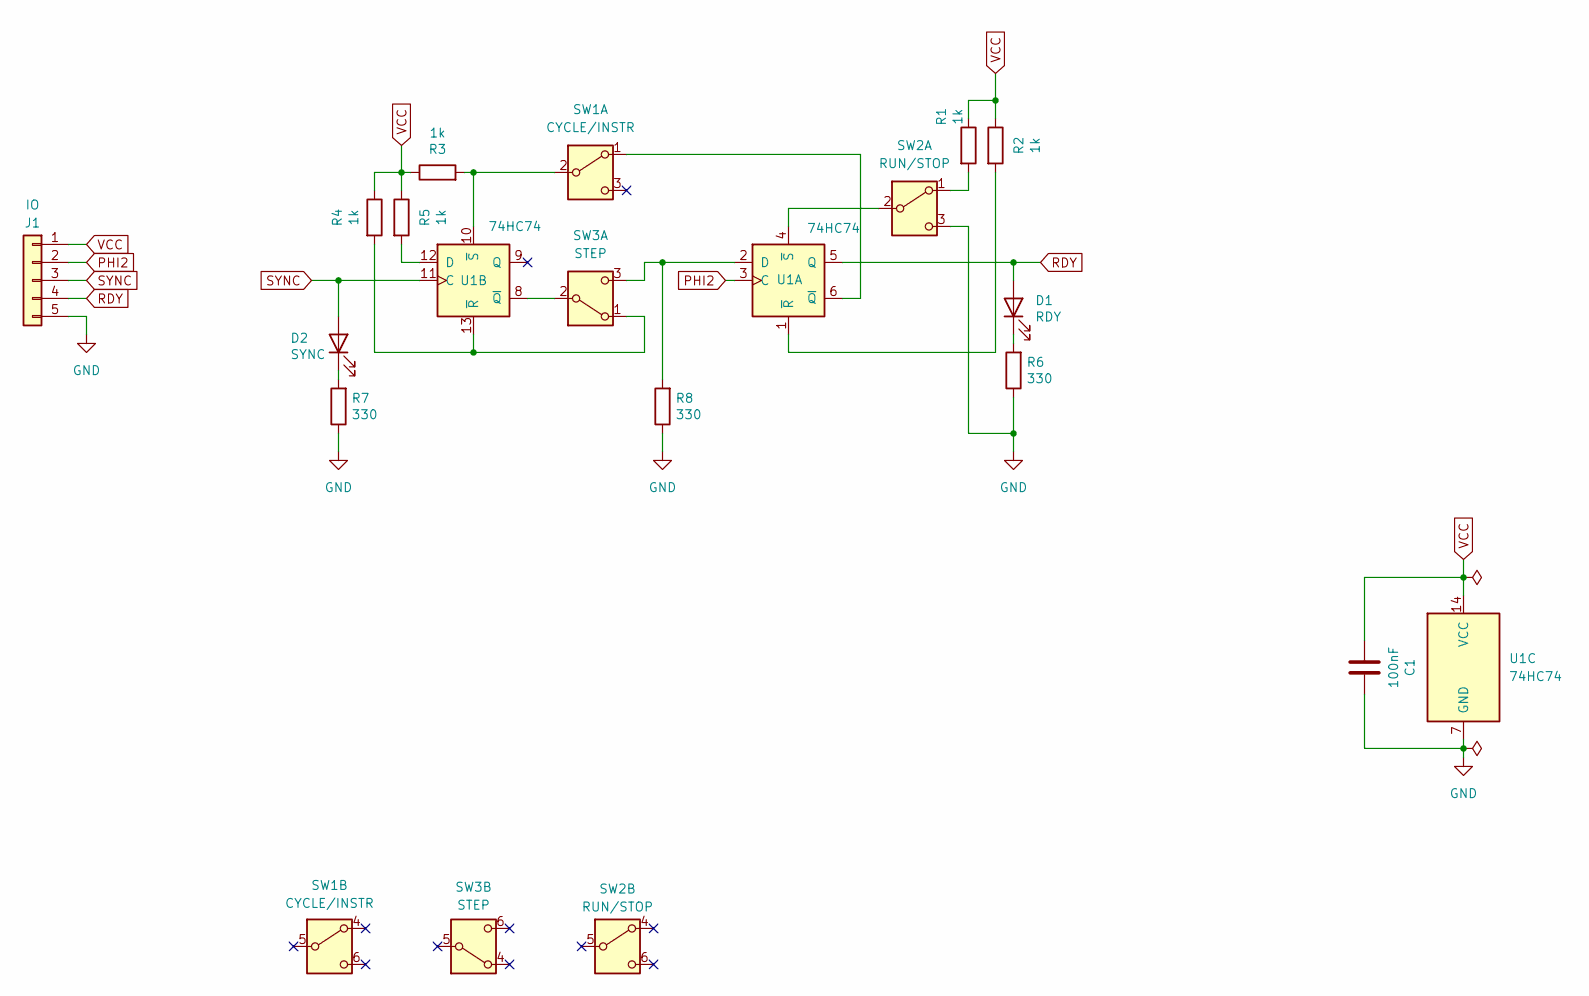
[picture p102: schematic Clock Helper.kicad_sch, 6502 Clock Helper]

Parts:
C1: 100nF; C_Disc_D5.0mm_W2.5mm_P2.50mm
D1: RDY; LED_D3.0mm
D2: SYNC; LED_D3.0mm
J1: IO; PinHeader_1x05_P2.54mm_Vertical
R1, R2, R3, R4, R5: 1k; R_Axial_DIN0204_L3.6mm_D1.6mm_P5.08mm_Horizontal
R6, R7, R8: 330; R_Axial_DIN0204_L3.6mm_D1.6mm_P5.08mm_Horizontal
SW1: CYCLE/INSTR; XKB5858; LCSC XKB5858-Z
SW2: RUN/STOP; XKB5858; LCSC XKB5858-Z
SW3: STEP; XKB5858; LCSC XKB5858-W
U1: 74HC74; DIP-14_W7.62mm_Socket_LongPads

Connections:
GND: C1.2, J1.5, R6.1, R7.1, R8.1, SW2.3 (C), U1.7 (GND)
unnamed: D1.1 (K), R6.2
unnamed: D2.1 (K), R7.2
unnamed: SW1.1 (A), U1.6 (~Q)
unnamed: R3.2, SW1.2 (B), U1.10 (~S)
unnamed: R1.2, SW2.1 (A)
unnamed: SW2.2 (B), U1.4 (~S)
unnamed: R4.2, SW3.1 (A), U1.13 (~R)
unnamed: SW3.2 (B), U1.8 (~Q)
unnamed: R8.2, SW3.3 (C), U1.2 (D)
unnamed: R2.2, U1.1 (~R)
unnamed: R5.2, U1.12 (D)
PHI2: J1.2, U1.3 (C)
RDY: D1.2 (A), J1.4, U1.5 (Q)
SYNC: D2.2 (A), J1.3, U1.11 (C)
VCC: C1.1, J1.1, R1.1, R2.1, R3.1, R4.1, R5.1, U1.14 (VCC)

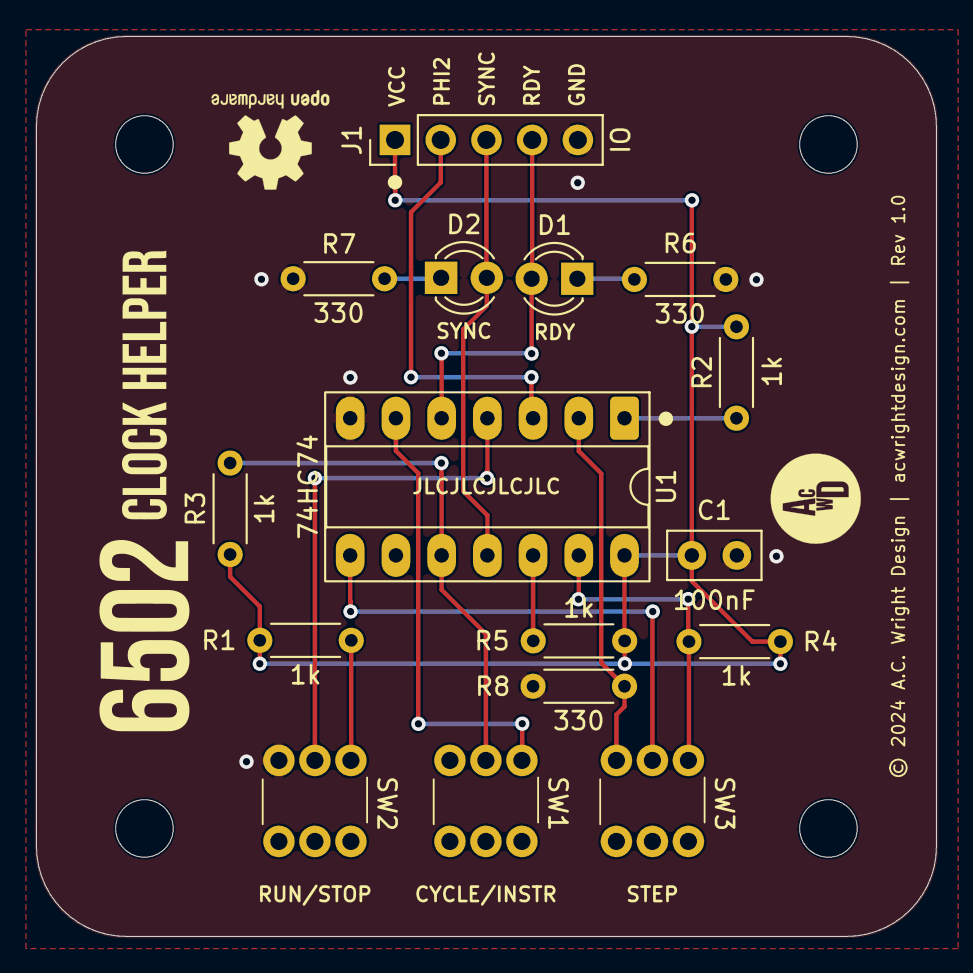
[picture p103: board Clock Helper.kicad_pcb from above]

Board: 2 copper layers, 50.0 x 50.0 mm, 20 parts (0 on the bottom side), 16 nets.

Other parts of the board:
H1, H2, H3, H4: MountingHole; MountingHole_3.2mm_M3
