acwright/6502-COB/Hardware/Prototype Card/Rev 1.0/Prototype Card.kicad_pcb

## KiCad design Hardware/Prototype Card/Rev 1.0/Prototype Card.kicad_pcb (2026-06-16)

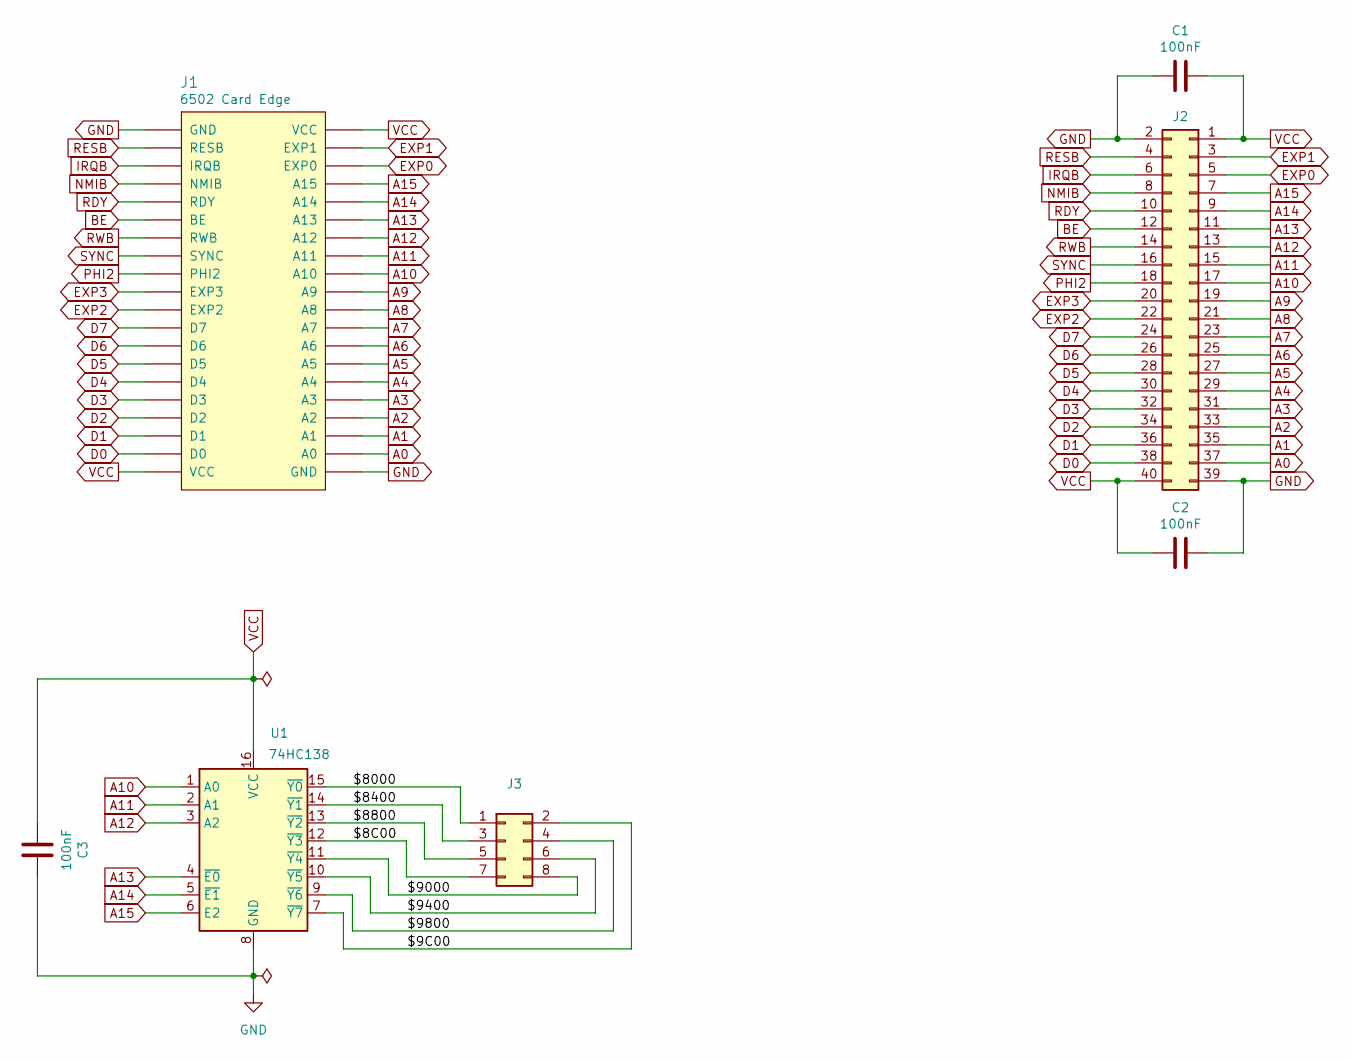
[picture p104: schematic Prototype Card.kicad_sch, 6502 Prototype Card]

Parts:
C1, C2, C3: 100nF; C_0805_2012Metric; LCSC C49678
J1: 6502 Card Edge
J2: Conn_02x20_Odd_Even; PinSocket_2x20_P2.54mm_Vertical
J3: Conn_02x04_Odd_Even; PinHeader_2x04_P2.54mm_Vertical
U1: 74HC138; SOIC-16_3.9x9.9mm_P1.27mm; LCSC C5602

Connections:
/$8C00: J3.7, U1.12 (~Y3)
/$9C00: J3.2, U1.7 (~Y7)
/$8000: J3.1, U1.15 (~Y0)
/$8400: J3.3, U1.14 (~Y1)
/$8800: J3.5, U1.13 (~Y2)
/$9000: J3.8, U1.11 (~Y4)
/$9400: J3.6, U1.10 (~Y5)
/$9800: J3.4, U1.9 (~Y6)
A0: J1.A0, J2.37
A1: J1.A1, J2.35
A2: J1.A2, J2.33
A3: J1.A3, J2.31
A4: J1.A4, J2.29
A5: J1.A5, J2.27
A6: J1.A6, J2.25
A7: J1.A7, J2.23
A8: J1.A8, J2.21
A9: J1.A9, J2.19
A10: J1.A10, J2.17, U1.1 (A0)
A11: J1.A11, J2.15, U1.2 (A1)
A12: J1.A12, J2.13, U1.3 (A2)
A13: J1.A13, J2.11, U1.4 (~E0)
A14: J1.A14, J2.9, U1.5 (~E1)
A15: J1.A15, J2.7, U1.6 (E2)
BE: J1.BE, J2.12
D0: J1.D0, J2.38
D1: J1.D1, J2.36
D2: J1.D2, J2.34
D3: J1.D3, J2.32
D4: J1.D4, J2.30
D5: J1.D5, J2.28
D6: J1.D6, J2.26
D7: J1.D7, J2.24
EXP0: J1.EXP0, J2.5
EXP1: J1.EXP1, J2.3
EXP2: J1.EXP2, J2.22
EXP3: J1.EXP3, J2.20
GND: C1.1, C2.2, C3.2, J1.GND, J2.2, J2.39, U1.8 (GND)
IRQB: J1.IRQB, J2.6
NMIB: J1.NMIB, J2.8
PHI2: J1.PHI2, J2.18
RDY: J1.RDY, J2.10
RESB: J1.RESB, J2.4
RWB: J1.RWB, J2.14
SYNC: J1.SYNC, J2.16
VCC: C1.2, C2.1, C3.1, J1.VCC, J2.1, J2.40, U1.16 (VCC)

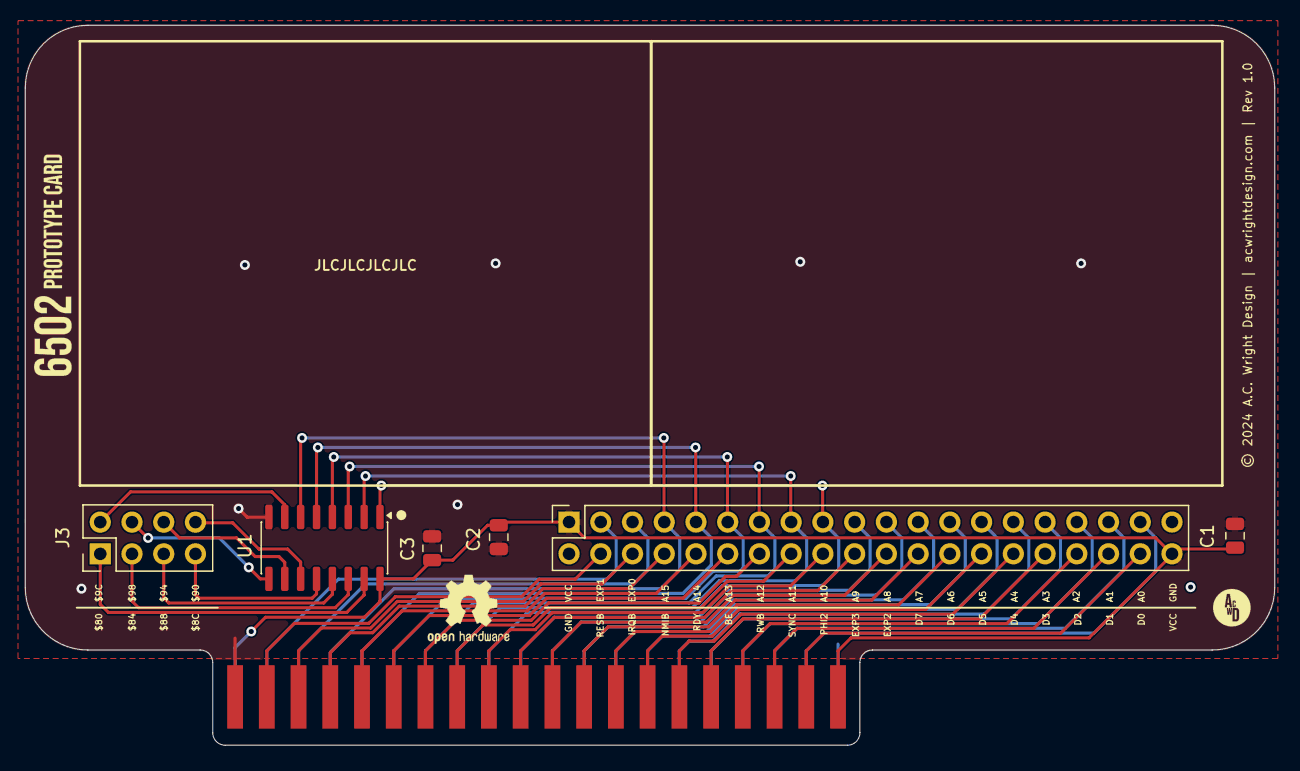
[picture p105: board Prototype Card.kicad_pcb from above]

Board: 2 copper layers, 100.0 x 57.6 mm, 9 parts (0 on the bottom side), 46 nets.

Other parts of the board:
B1, B2: BREADBOARDMINI; Breadboard Mini
