acwright/6502-COB/Hardware/VGA Card Pro/Rev 1.0/VGA Card Pro.kicad_pcb

## KiCad design Hardware/VGA Card Pro/Rev 1.0/VGA Card Pro.kicad_pcb (2026-06-16)

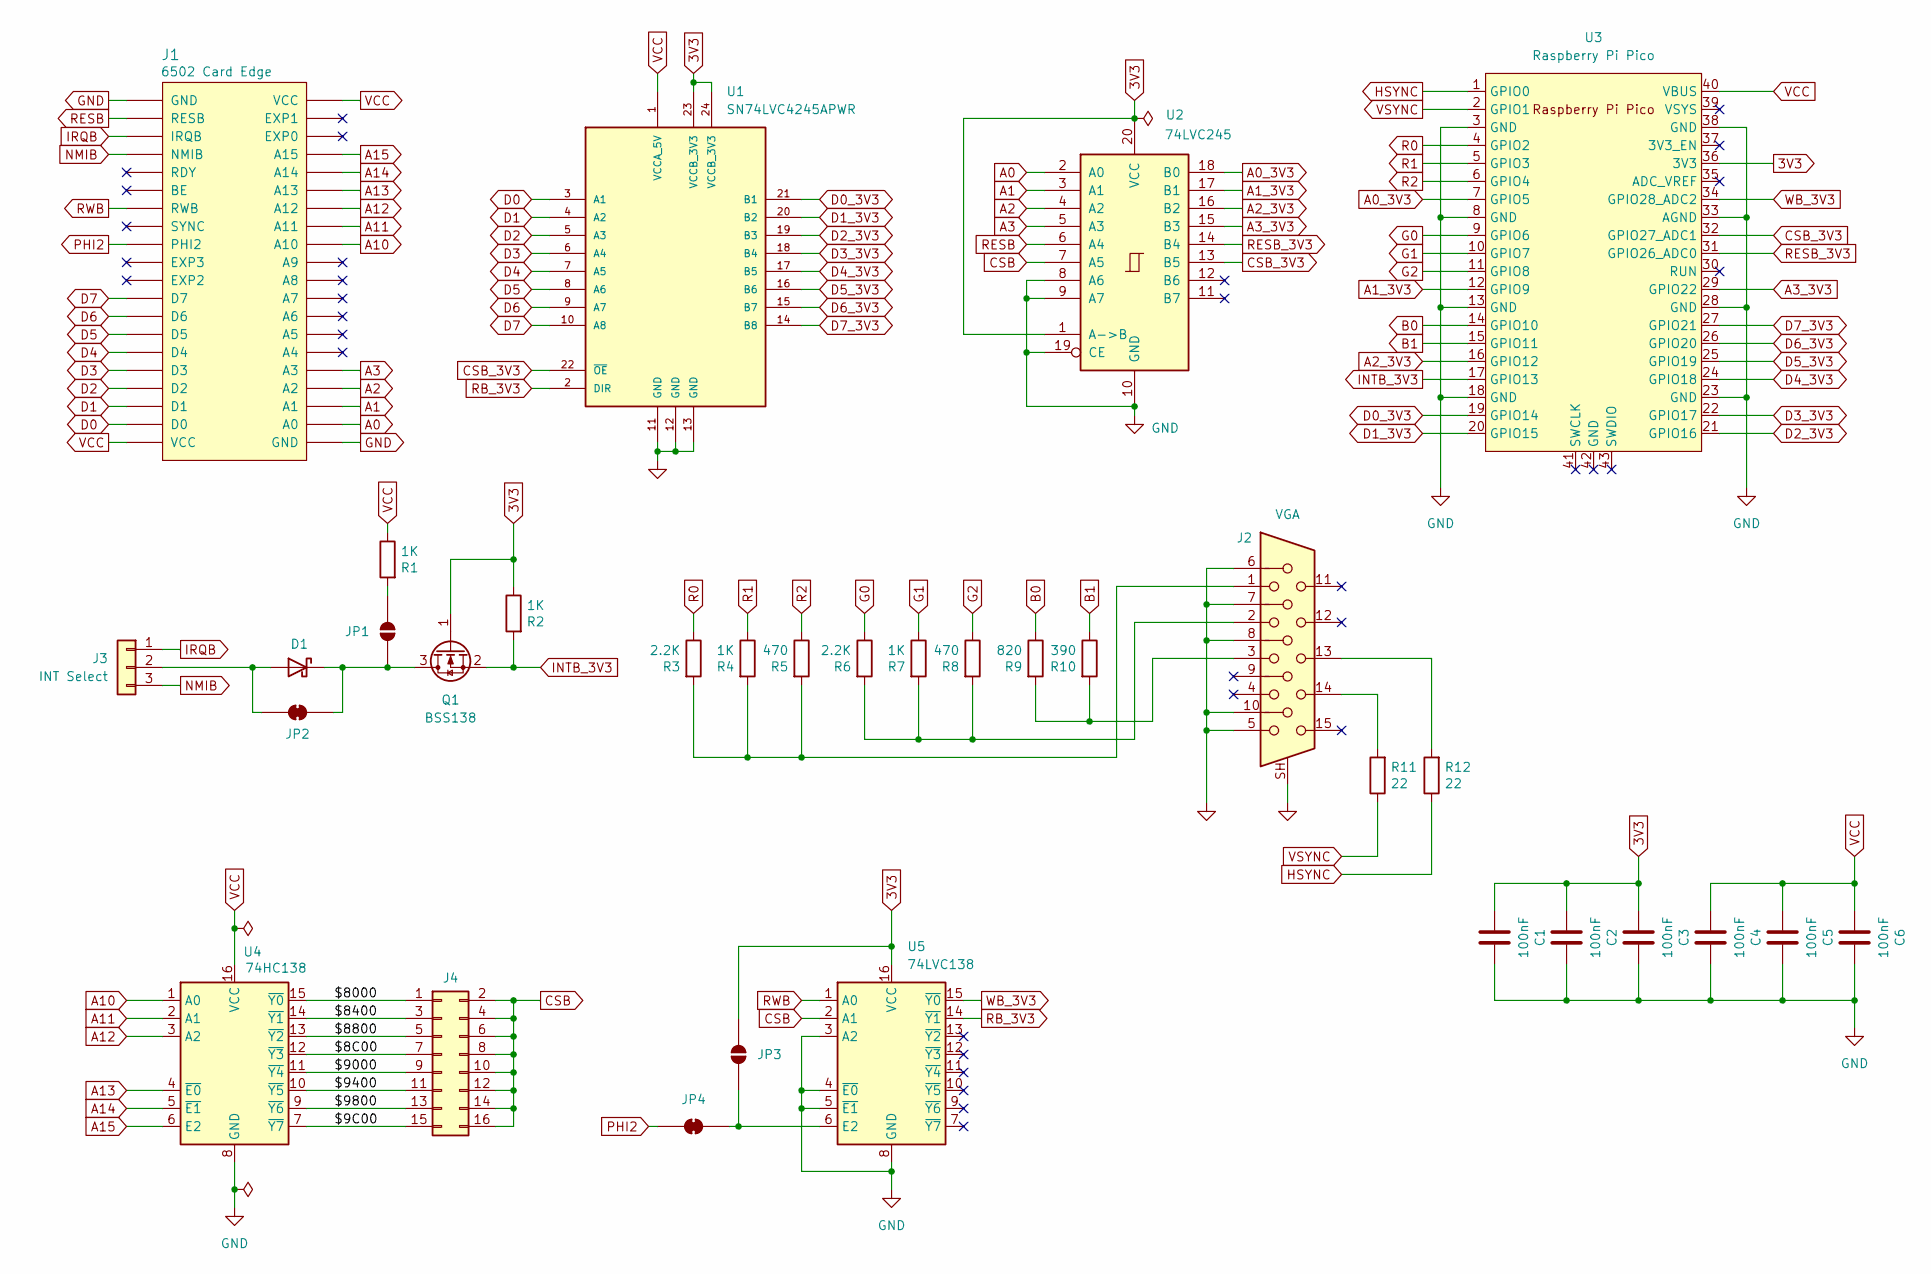
[picture p108: schematic VGA Card Pro.kicad_sch, 6502 VGA Card Pro]

Parts:
C1, C2, C3, C4, C5, C6: 100nF; C_0805_2012Metric; LCSC C49678
D1: D_Schottky; D_DO-35_SOD27_P7.62mm_Horizontal
J1: 6502 Card Edge
J2: VGA; DSUB-15-HD_Socket_Horizontal_P2.29x1.90mm_EdgePinOffset3.03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
J3: INT Select; PinHeader_1x03_P2.54mm_Vertical
J4: Conn_02x08_Odd_Even; PinHeader_2x08_P2.54mm_Vertical
JP1, JP3: SolderJumper_2_Open; SolderJumper-2_P1.3mm_Open_RoundedPad1.0x1.5mm
JP2, JP4: SolderJumper_2_Bridged; SolderJumper-2_P1.3mm_Bridged_RoundedPad1.0x1.5mm
Q1: BSS138; SOT-23; LCSC C78284
R1, R2, R4, R7: 1K; R_0805_2012Metric; LCSC C17513
R3, R6: 2.2K; R_0805_2012Metric; LCSC C17520
R5, R8: 470; R_0805_2012Metric; LCSC C17710
R9: 820; R_0805_2012Metric; LCSC C17837
R10: 390; R_0805_2012Metric; LCSC C17655
R11, R12: 22; R_0805_2012Metric; LCSC C17561
U1: SN74LVC4245APWR; TSSOP-24_4.4x7.8mm_P0.65mm; LCSC C7859
U2: 74LVC245; TSSOP-20_4.4x6.5mm_P0.65mm; LCSC C6082
U3: Raspberry Pi Pico
U4: 74HC138; SOIC-16_3.9x9.9mm_P1.27mm; LCSC C5602
U5: 74LVC138; SOIC-16_3.9x9.9mm_P1.27mm; LCSC C6061

Connections:
3V3: C1.1, C2.1, C3.1, JP3.1 (A), Q1.1 (G), R2.1, U1.23 (VCCB_3V3), U1.24 (VCCB_3V3), U2.1 (A->B), U2.20 (VCC), U3.36 (3V3), U5.16 (VCC)
/$8C00: J4.7, U4.12 (~Y3)
/$9C00: J4.15, U4.7 (~Y7)
/$8000: J4.1, U4.15 (~Y0)
/$8400: J4.3, U4.14 (~Y1)
/$8800: J4.5, U4.13 (~Y2)
/$9000: J4.9, U4.11 (~Y4)
/$9400: J4.11, U4.10 (~Y5)
/$9800: J4.13, U4.9 (~Y6)
A0: J1.A0, U2.2 (A0)
A0_3V3: U2.18 (B0), U3.7 (GPIO5)
A1: J1.A1, U2.3 (A1)
A1_3V3: U2.17 (B1), U3.12 (GPIO9)
A2: J1.A2, U2.4 (A2)
A2_3V3: U2.16 (B2), U3.16 (GPIO12)
A3: J1.A3, U2.5 (A3)
A3_3V3: U2.15 (B3), U3.29 (GPIO22)
A10: J1.A10, U4.1 (A0)
A11: J1.A11, U4.2 (A1)
A12: J1.A12, U4.3 (A2)
A13: J1.A13, U4.4 (~E0)
A14: J1.A14, U4.5 (~E1)
A15: J1.A15, U4.6 (E2)
B0: R9.1, U3.14 (GPIO10)
B1: R10.1, U3.15 (GPIO11)
CSB: J4.2, J4.4, J4.6, J4.8, J4.10, J4.12, J4.14, J4.16, U2.7 (A5), U5.2 (A1)
CSB_3V3: U1.22 (~OE), U2.13 (B5), U3.32 (GPIO27_ADC1)
D0: J1.D0, U1.3 (A1)
D0_3V3: U1.21 (B1), U3.19 (GPIO14)
D1: J1.D1, U1.4 (A2)
D1_3V3: U1.20 (B2), U3.20 (GPIO15)
D2: J1.D2, U1.5 (A3)
D2_3V3: U1.19 (B3), U3.21 (GPIO16)
D3: J1.D3, U1.6 (A4)
D3_3V3: U1.18 (B4), U3.22 (GPIO17)
D4: J1.D4, U1.7 (A5)
D4_3V3: U1.17 (B5), U3.24 (GPIO18)
D5: J1.D5, U1.8 (A6)
D5_3V3: U1.16 (B6), U3.25 (GPIO19)
D6: J1.D6, U1.9 (A7)
D6_3V3: U1.15 (B7), U3.26 (GPIO20)
D7: J1.D7, U1.10 (A8)
D7_3V3: U1.14 (B8), U3.27 (GPIO21)
G0: R6.1, U3.9 (GPIO6)
G1: R7.1, U3.10 (GPIO7)
G2: R8.1, U3.11 (GPIO8)
GND: C1.2, C2.2, C3.2, C4.2, C5.2, C6.2, J1.GND, J2.5, J2.6, J2.7, J2.8, J2.10, J2.SH, U1.11 (GND), U1.12 (GND), U1.13 (GND), U2.8 (A6), U2.9 (A7), U2.10 (GND), U2.19 (CE), U3.3 (GND), U3.8 (GND), U3.13 (GND), U3.18 (GND), U3.23 (GND), U3.28 (GND), U3.33 (AGND), U3.38 (GND), U4.8 (GND), U5.3 (A2), U5.4 (~E0), U5.5 (~E1), U5.8 (GND)
HSYNC: R12.1, U3.1 (GPIO0)
INTB_3V3: Q1.2 (S), R2.2, U3.17 (GPIO13)
IRQB: J1.IRQB, J3.1
NMIB: J1.NMIB, J3.3
unnamed: D1.2 (A), J3.2, JP2.2 (B)
unnamed: D1.1 (K), JP1.2 (B), JP2.1 (A), Q1.3 (D)
unnamed: J2.1, R3.2, R4.2, R5.2
unnamed: J2.2, R6.2, R7.2, R8.2
unnamed: J2.3, R9.2, R10.2
unnamed: J2.13, R12.2
unnamed: J2.14, R11.2
unnamed: JP1.1 (A), R1.2
unnamed: JP3.2 (B), JP4.1 (A), U5.6 (E2)
PHI2: J1.PHI2, JP4.2 (B)
R0: R3.1, U3.4 (GPIO2)
R1: R4.1, U3.5 (GPIO3)
R2: R5.1, U3.6 (GPIO4)
RB_3V3: U1.2 (DIR), U5.14 (~Y1)
RESB: J1.RESB, U2.6 (A4)
RESB_3V3: U2.14 (B4), U3.31 (GPIO26_ADC0)
RWB: J1.RWB, U5.1 (A0)
VCC: C4.1, C5.1, C6.1, J1.VCC, R1.1, U1.1 (VCCA_5V), U3.40 (VBUS), U4.16 (VCC)
VSYNC: R11.1, U3.2 (GPIO1)
WB_3V3: U3.34 (GPIO28_ADC2), U5.15 (~Y0)

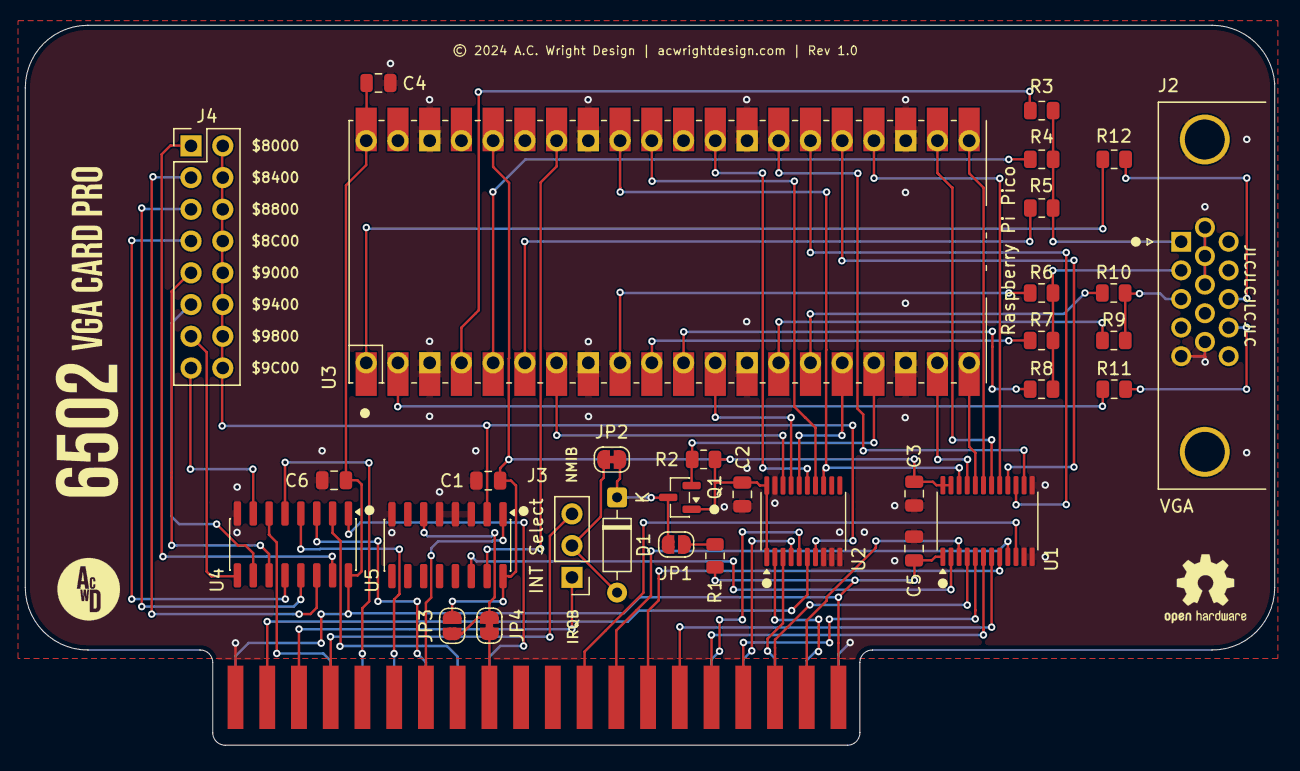
[picture p109: board VGA Card Pro.kicad_pcb from above]

Board: 2 copper layers, 100.0 x 57.6 mm, 33 parts (0 on the bottom side), 71 nets.
