acwright/6502-COB/Hardware/GPIO Breadboard Helper/Rev 1.0/GPIO Breadboard Helper.kicad_pcb

## KiCad design Hardware/GPIO Breadboard Helper/Rev 1.0/GPIO Breadboard Helper.kicad_pcb (2026-06-16)

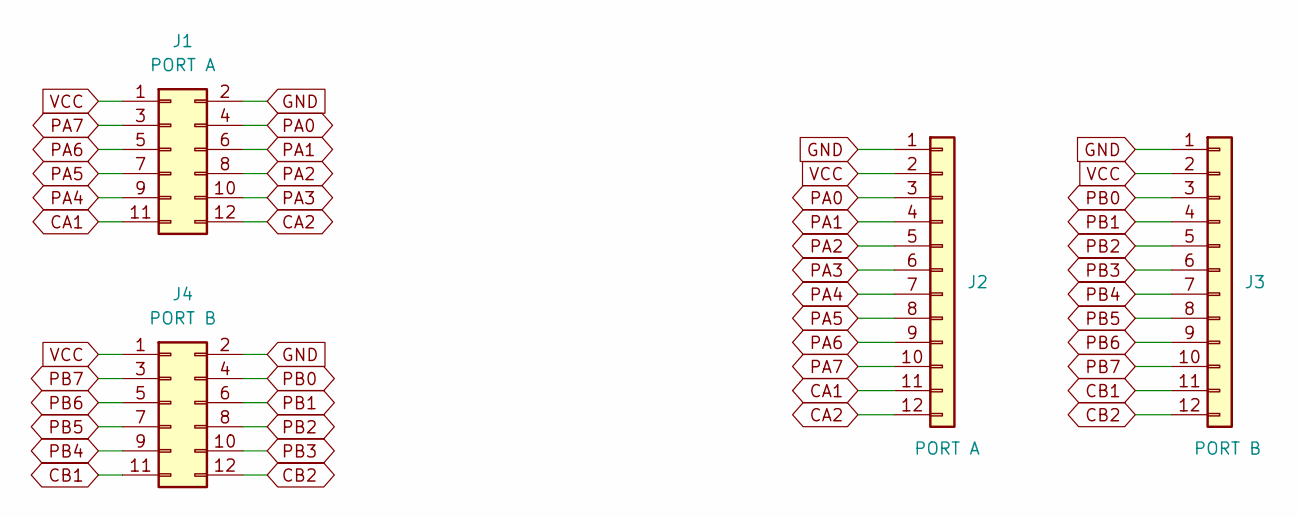
[picture p110: schematic GPIO Breadboard Helper.kicad_sch, 6502 GPIO Breadboard Helper]

Parts:
J1: PORT A; 6502 GPIO Connector
J2: PORT A; PinHeader_1x12_P2.54mm_Vertical
J3: PORT B; PinHeader_1x12_P2.54mm_Vertical
J4: PORT B; 6502 GPIO Connector

Connections:
CA1: J1.11, J2.11
CA2: J1.12, J2.12
CB1: J3.11, J4.11
CB2: J3.12, J4.12
GND: J1.2, J2.1, J3.1, J4.2
PA0: J1.4, J2.3
PA1: J1.6, J2.4
PA2: J1.8, J2.5
PA3: J1.10, J2.6
PA4: J1.9, J2.7
PA5: J1.7, J2.8
PA6: J1.5, J2.9
PA7: J1.3, J2.10
PB0: J3.3, J4.4
PB1: J3.4, J4.6
PB2: J3.5, J4.8
PB3: J3.6, J4.10
PB4: J3.7, J4.9
PB5: J3.8, J4.7
PB6: J3.9, J4.5
PB7: J3.10, J4.3
VCC: J1.1, J2.2, J3.2, J4.1

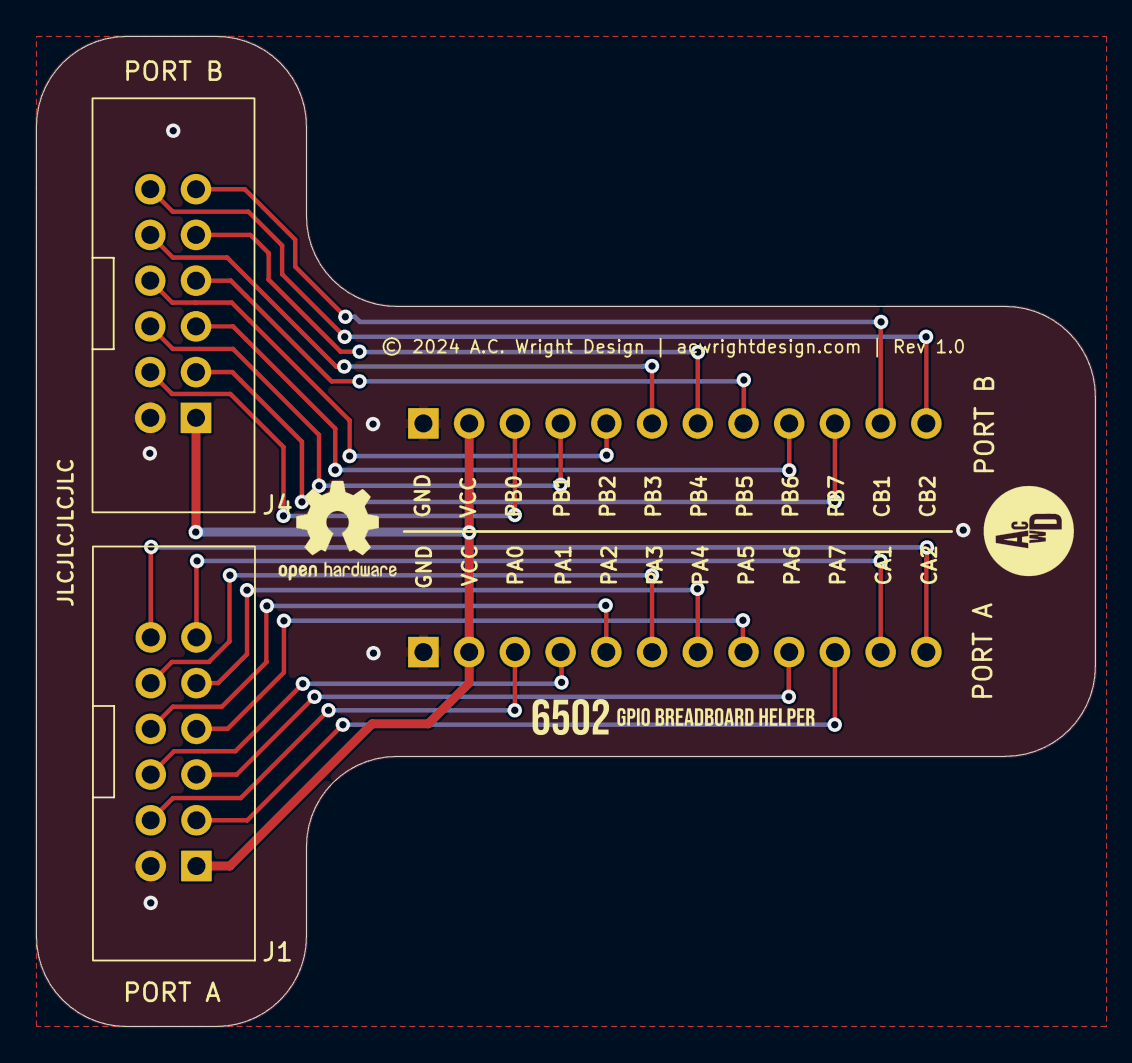
[picture p111: board GPIO Breadboard Helper.kicad_pcb from above]

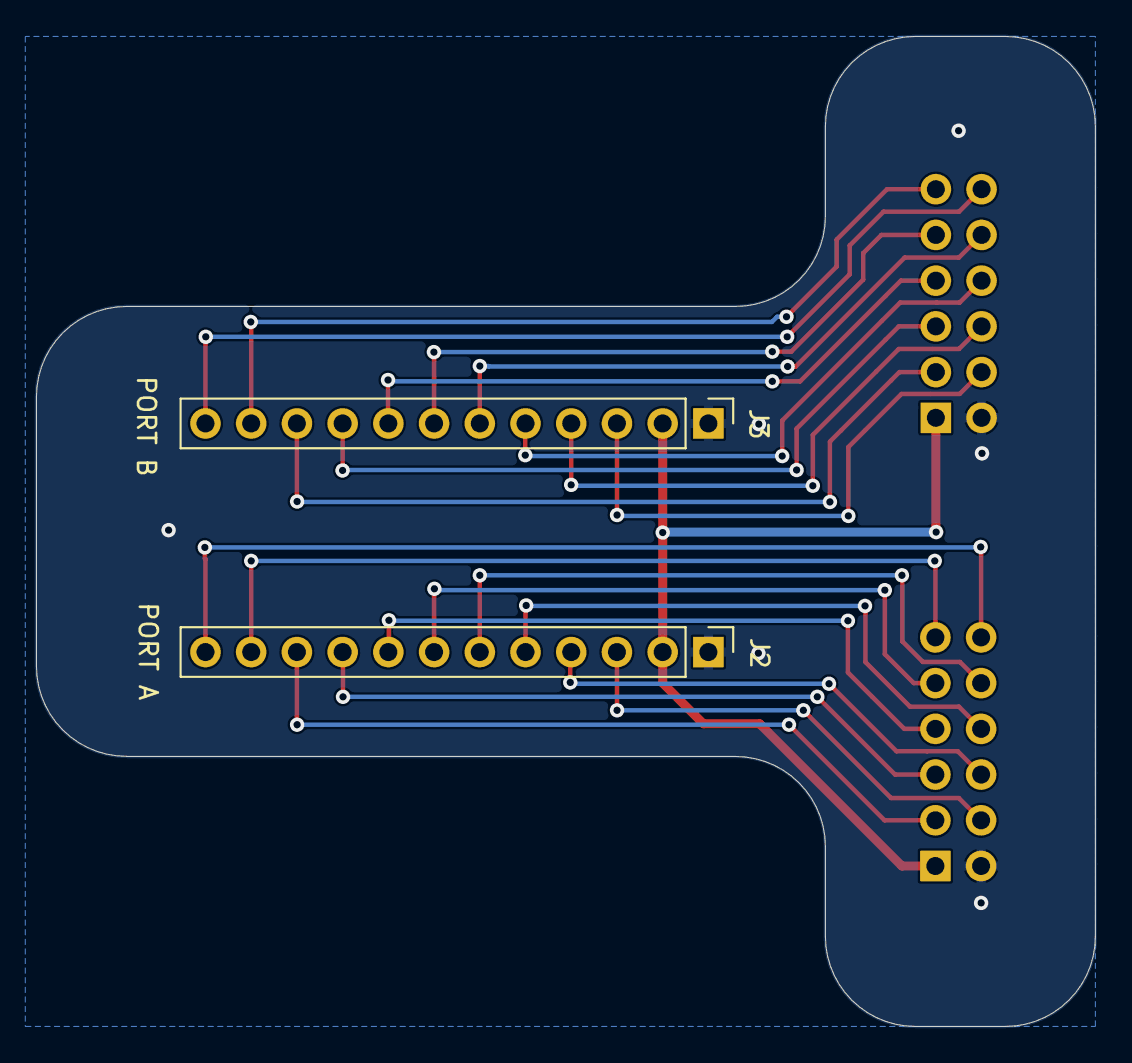
[picture p112: board GPIO Breadboard Helper.kicad_pcb from below]

Board: 2 copper layers, 58.8 x 55.0 mm, 4 parts (2 on the bottom side), 22 nets.
