acwright/6502-COB/Hardware/RTC Card/Rev 1.0/RTC Card.kicad_pcb

## KiCad design Hardware/RTC Card/Rev 1.0/RTC Card.kicad_pcb (2026-06-16)

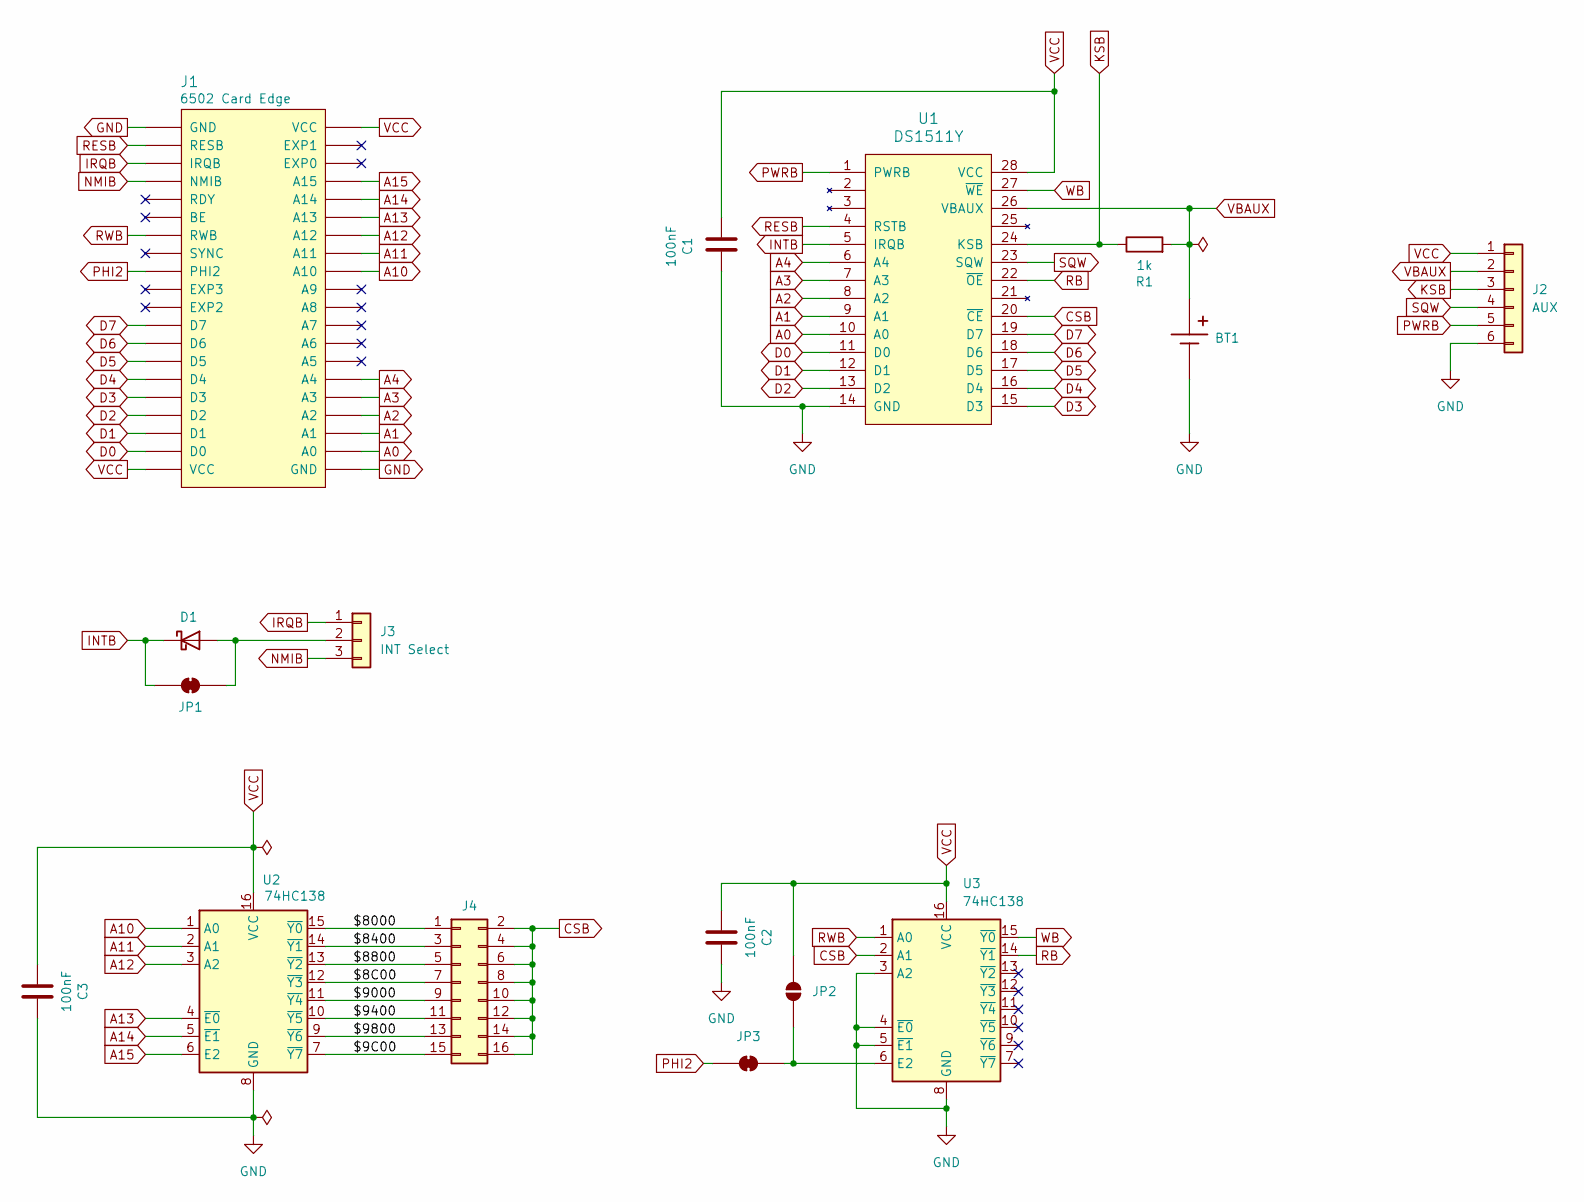
[picture p115: schematic RTC Card.kicad_sch, 6502 RTC Card]

Parts:
BT1: BAT-HLD-001-THM; BAT_BAT-HLD-001-THM
C1, C2, C3: 100nF; C_0805_2012Metric; LCSC C49678
D1: D_Schottky; D_DO-35_SOD27_P7.62mm_Horizontal
J1: 6502 Card Edge
J2: AUX; PinHeader_1x06_P2.54mm_Vertical
J3: INT Select; PinHeader_1x03_P2.54mm_Vertical
J4: Conn_02x08_Odd_Even; PinHeader_2x08_P2.54mm_Vertical
JP1, JP3: SolderJumper_2_Bridged; SolderJumper-2_P1.3mm_Bridged_RoundedPad1.0x1.5mm
JP2: SolderJumper_2_Open; SolderJumper-2_P1.3mm_Open_RoundedPad1.0x1.5mm
R1: 1k; R_0805_2012Metric; LCSC C17513
U1: DS1511Y; DIP-28_W15.24mm_Socket_LongPads; Digikey DS1511Y+-ND
U2, U3: 74HC138; SOIC-16_3.9x9.9mm_P1.27mm; LCSC C5602

Connections:
/$8C00: J4.7, U2.12 (~Y3)
/$9C00: J4.15, U2.7 (~Y7)
/$8000: J4.1, U2.15 (~Y0)
/$8400: J4.3, U2.14 (~Y1)
/$8800: J4.5, U2.13 (~Y2)
/$9000: J4.9, U2.11 (~Y4)
/$9400: J4.11, U2.10 (~Y5)
/$9800: J4.13, U2.9 (~Y6)
A0: J1.A0, U1.10 (A0)
A1: J1.A1, U1.9 (A1)
A2: J1.A2, U1.8 (A2)
A3: J1.A3, U1.7 (A3)
A4: J1.A4, U1.6 (A4)
A10: J1.A10, U2.1 (A0)
A11: J1.A11, U2.2 (A1)
A12: J1.A12, U2.3 (A2)
A13: J1.A13, U2.4 (~E0)
A14: J1.A14, U2.5 (~E1)
A15: J1.A15, U2.6 (E2)
CSB: J4.2, J4.4, J4.6, J4.8, J4.10, J4.12, J4.14, J4.16, U1.20 (~CE), U3.2 (A1)
D0: J1.D0, U1.11 (D0)
D1: J1.D1, U1.12 (D1)
D2: J1.D2, U1.13 (D2)
D3: J1.D3, U1.15 (D3)
D4: J1.D4, U1.16 (D4)
D5: J1.D5, U1.17 (D5)
D6: J1.D6, U1.18 (D6)
D7: J1.D7, U1.19 (D7)
GND: BT1.-, C1.2, C2.2, C3.2, J1.GND, J2.6, U1.14 (GND), U2.8 (GND), U3.3 (A2), U3.4 (~E0), U3.5 (~E1), U3.8 (GND)
INTB: D1.1 (K), JP1.1 (A), U1.5 (IRQB)
IRQB: J1.IRQB, J3.1
KSB: J2.3, R1.1, U1.24 (KSB)
NMIB: J1.NMIB, J3.3
unnamed: D1.2 (A), J3.2, JP1.2 (B)
unnamed: JP2.2 (B), JP3.1 (A), U3.6 (E2)
PHI2: J1.PHI2, JP3.2 (B)
PWRB: J2.5, U1.1 (PWRB)
RB: U1.22 (~OE), U3.14 (~Y1)
RESB: J1.RESB, U1.4 (RSTB)
RWB: J1.RWB, U3.1 (A0)
SQW: J2.4, U1.23 (SQW)
VBAUX: BT1.+, J2.2, R1.2, U1.26 (VBAUX)
VCC: C1.1, C2.1, C3.1, J1.VCC, J2.1, JP2.1 (A), U1.28 (VCC), U2.16 (VCC), U3.16 (VCC)
WB: U1.27 (~WE), U3.15 (~Y0)
