acwright/6502-COB/Hardware/RTC Card/Rev 1.0/RTC Card.kicad_pcb

## KiCad design Hardware/RTC Card/Rev 1.0/RTC Card.kicad_pcb (continued)

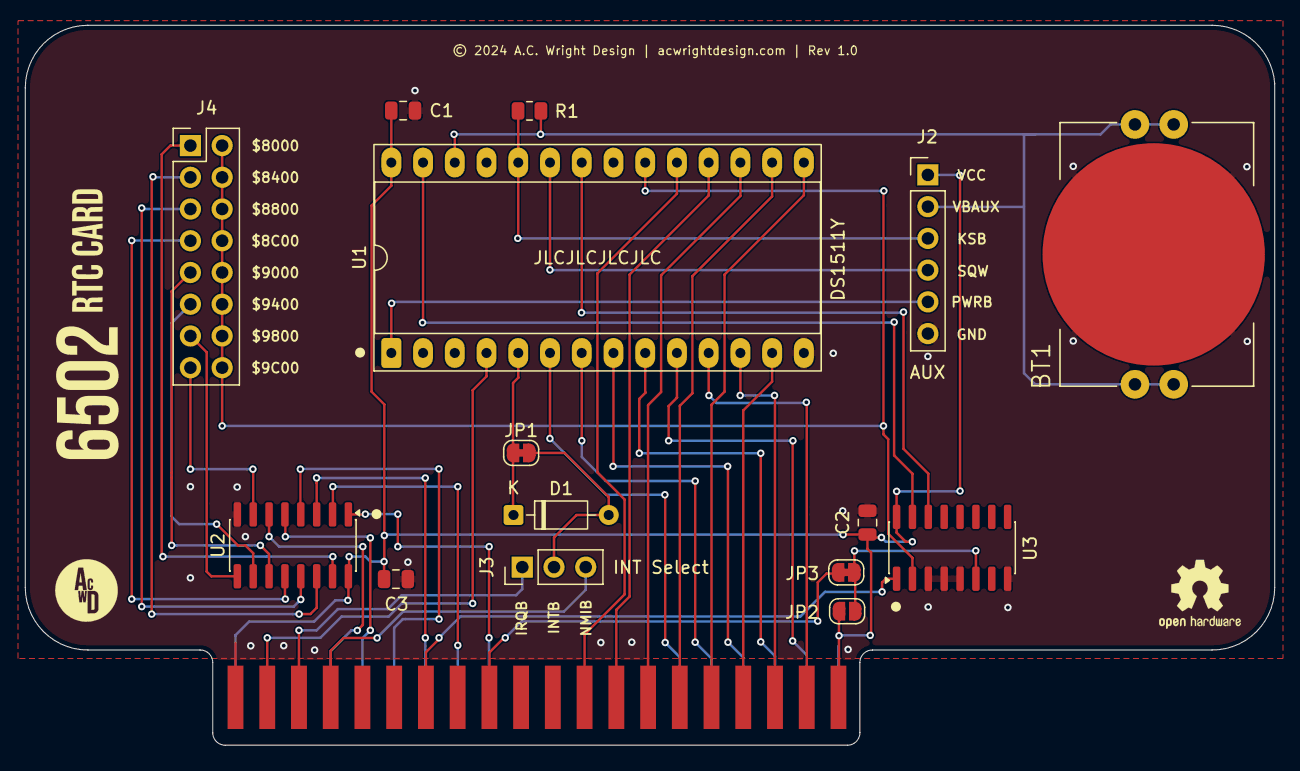
[picture p116: board RTC Card.kicad_pcb from above]

Board: 2 copper layers, 100.0 x 57.6 mm, 16 parts (0 on the bottom side), 44 nets.
