acwright/6502-COB/Hardware/Sound Card/Rev 1.0/Sound Card.kicad_pcb

## KiCad design Hardware/Sound Card/Rev 1.0/Sound Card.kicad_pcb (2026-06-16)

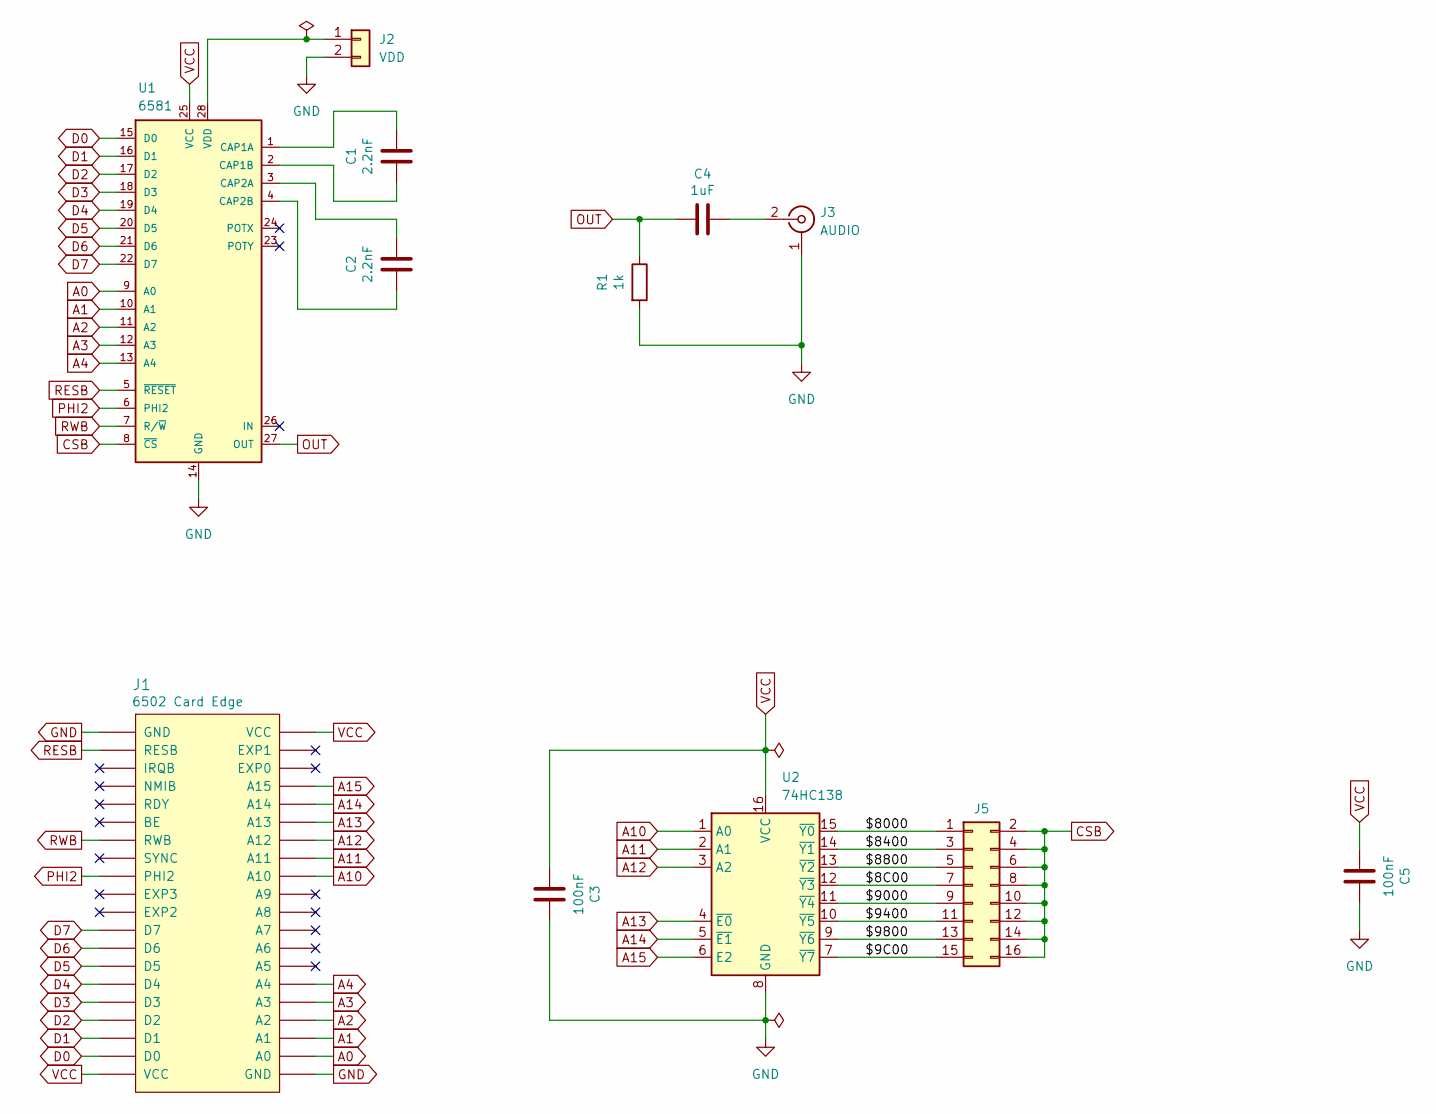
[picture p121: schematic Sound Card.kicad_sch, 6502 Sound Card]

Parts:
C1, C2: 2.2nF; C_0805_2012Metric; LCSC C28260
C3, C5: 100nF; C_0805_2012Metric; LCSC C49678
C4: 1uF; C_0805_2012Metric; LCSC C28323
J1: 6502 Card Edge
J2: VDD; JST_XH_B2B-XH-A_1x02_P2.50mm_Vertical
J3: AUDIO; SWITCHCRAFT_PJRAN1X1U02X
J5: Conn_02x08_Odd_Even; PinHeader_2x08_P2.54mm_Vertical
R1: 1k; R_0805_2012Metric; LCSC C17513
U1: 6581; DIP-28_W15.24mm_Socket_LongPads
U2: 74HC138; SOIC-16_3.9x9.9mm_P1.27mm; LCSC C5602

Connections:
/$8C00: J5.7, U2.12 (~Y3)
/$9C00: J5.15, U2.7 (~Y7)
/$8000: J5.1, U2.15 (~Y0)
/$8400: J5.3, U2.14 (~Y1)
/$8800: J5.5, U2.13 (~Y2)
/$9000: J5.9, U2.11 (~Y4)
/$9400: J5.11, U2.10 (~Y5)
/$9800: J5.13, U2.9 (~Y6)
A0: J1.A0, U1.9 (A0)
A1: J1.A1, U1.10 (A1)
A2: J1.A2, U1.11 (A2)
A3: J1.A3, U1.12 (A3)
A4: J1.A4, U1.13 (A4)
A10: J1.A10, U2.1 (A0)
A11: J1.A11, U2.2 (A1)
A12: J1.A12, U2.3 (A2)
A13: J1.A13, U2.4 (~E0)
A14: J1.A14, U2.5 (~E1)
A15: J1.A15, U2.6 (E2)
CSB: J5.2, J5.4, J5.6, J5.8, J5.10, J5.12, J5.14, J5.16, U1.8 (~CS)
D0: J1.D0, U1.15 (D0)
D1: J1.D1, U1.16 (D1)
D2: J1.D2, U1.17 (D2)
D3: J1.D3, U1.18 (D3)
D4: J1.D4, U1.19 (D4)
D5: J1.D5, U1.20 (D5)
D6: J1.D6, U1.21 (D6)
D7: J1.D7, U1.22 (D7)
GND: C3.2, C5.2, J1.GND, J2.2, J3.1 (Ext), R1.2, U1.14 (GND), U2.8 (GND)
unnamed: J2.1, U1.28 (VDD)
unnamed: C4.2, J3.2 (In)
unnamed: C1.2, U1.1 (CAP1A)
unnamed: C1.1, U1.2 (CAP1B)
unnamed: C2.2, U1.3 (CAP2A)
unnamed: C2.1, U1.4 (CAP2B)
OUT: C4.1, R1.1, U1.27 (OUT)
PHI2: J1.PHI2, U1.6 (PHI2)
RESB: J1.RESB, U1.5 (~RESET)
RWB: J1.RWB, U1.7 (R/~W)
VCC: C3.1, C5.1, J1.VCC, U1.25 (VCC), U2.16 (VCC)

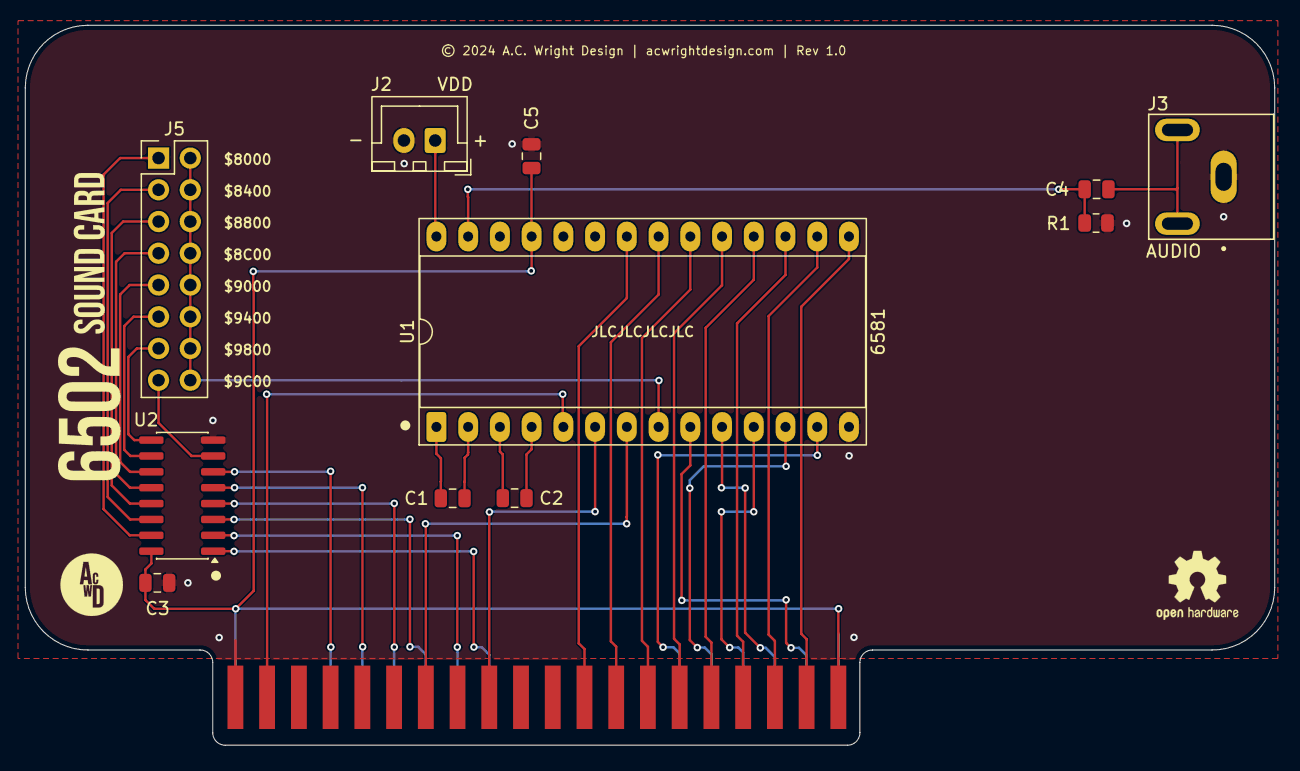
[picture p122: board Sound Card.kicad_pcb from above]

Board: 2 copper layers, 100.0 x 57.6 mm, 12 parts (0 on the bottom side), 40 nets.
