acwright/6502-COB/Hardware/Breadboard Helper/Rev 1.0/Breadboard Helper.kicad_pcb

## KiCad design Hardware/Breadboard Helper/Rev 1.0/Breadboard Helper.kicad_pcb (2026-06-16)

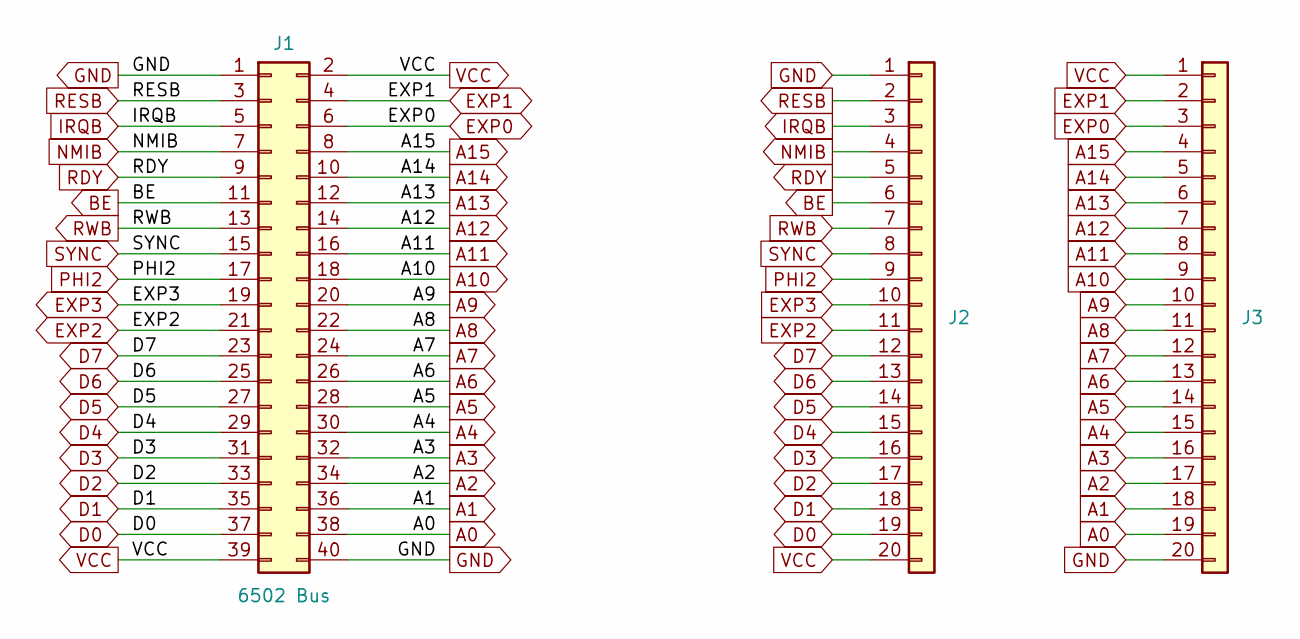
[picture p127: schematic Breadboard Helper.kicad_sch, 6502 Breadboard Helper]

Parts:
J1: 6502 Bus; PinHeader_2x20_P2.54mm_Vertical; Digikey 732-5401-ND
J2, J3: Conn_01x20; PinHeader_1x20_P2.54mm_Vertical

Connections:
A0: J1.38, J3.19
A1: J1.36, J3.18
A2: J1.34, J3.17
A3: J1.32, J3.16
A4: J1.30, J3.15
A5: J1.28, J3.14
A6: J1.26, J3.13
A7: J1.24, J3.12
A8: J1.22, J3.11
A9: J1.20, J3.10
A10: J1.18, J3.9
A11: J1.16, J3.8
A12: J1.14, J3.7
A13: J1.12, J3.6
A14: J1.10, J3.5
A15: J1.8, J3.4
BE: J1.11, J2.6
D0: J1.37, J2.19
D1: J1.35, J2.18
D2: J1.33, J2.17
D3: J1.31, J2.16
D4: J1.29, J2.15
D5: J1.27, J2.14
D6: J1.25, J2.13
D7: J1.23, J2.12
EXP0: J1.6, J3.3
EXP1: J1.4, J3.2
EXP2: J1.21, J2.11
EXP3: J1.19, J2.10
GND: J1.1, J1.40, J2.1, J3.20
IRQB: J1.5, J2.3
NMIB: J1.7, J2.4
PHI2: J1.17, J2.9
RDY: J1.9, J2.5
RESB: J1.3, J2.2
RWB: J1.13, J2.7
SYNC: J1.15, J2.8
VCC: J1.2, J1.39, J2.20, J3.1

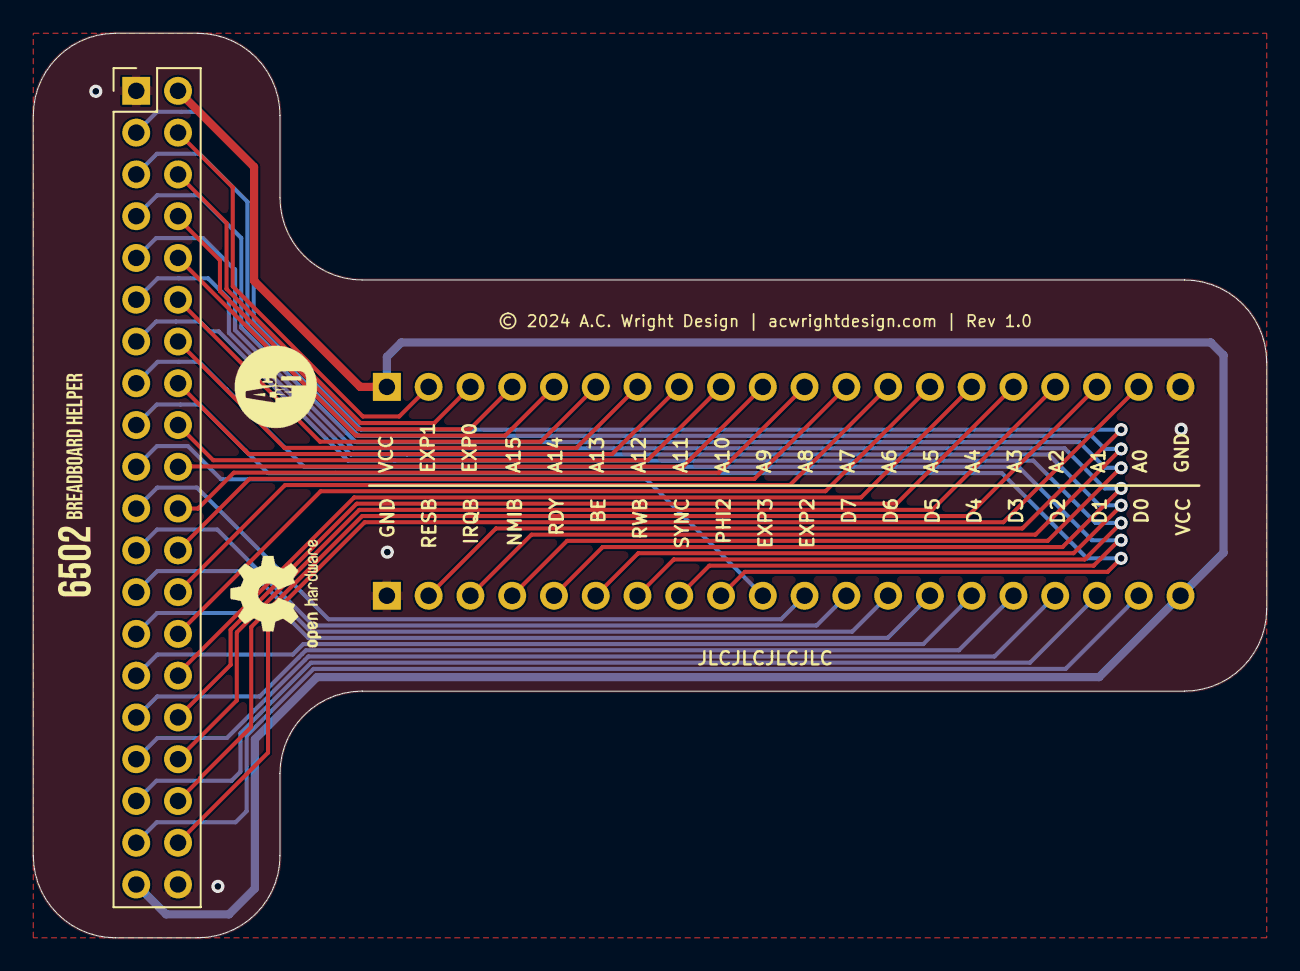
[picture p128: board Breadboard Helper.kicad_pcb from above]

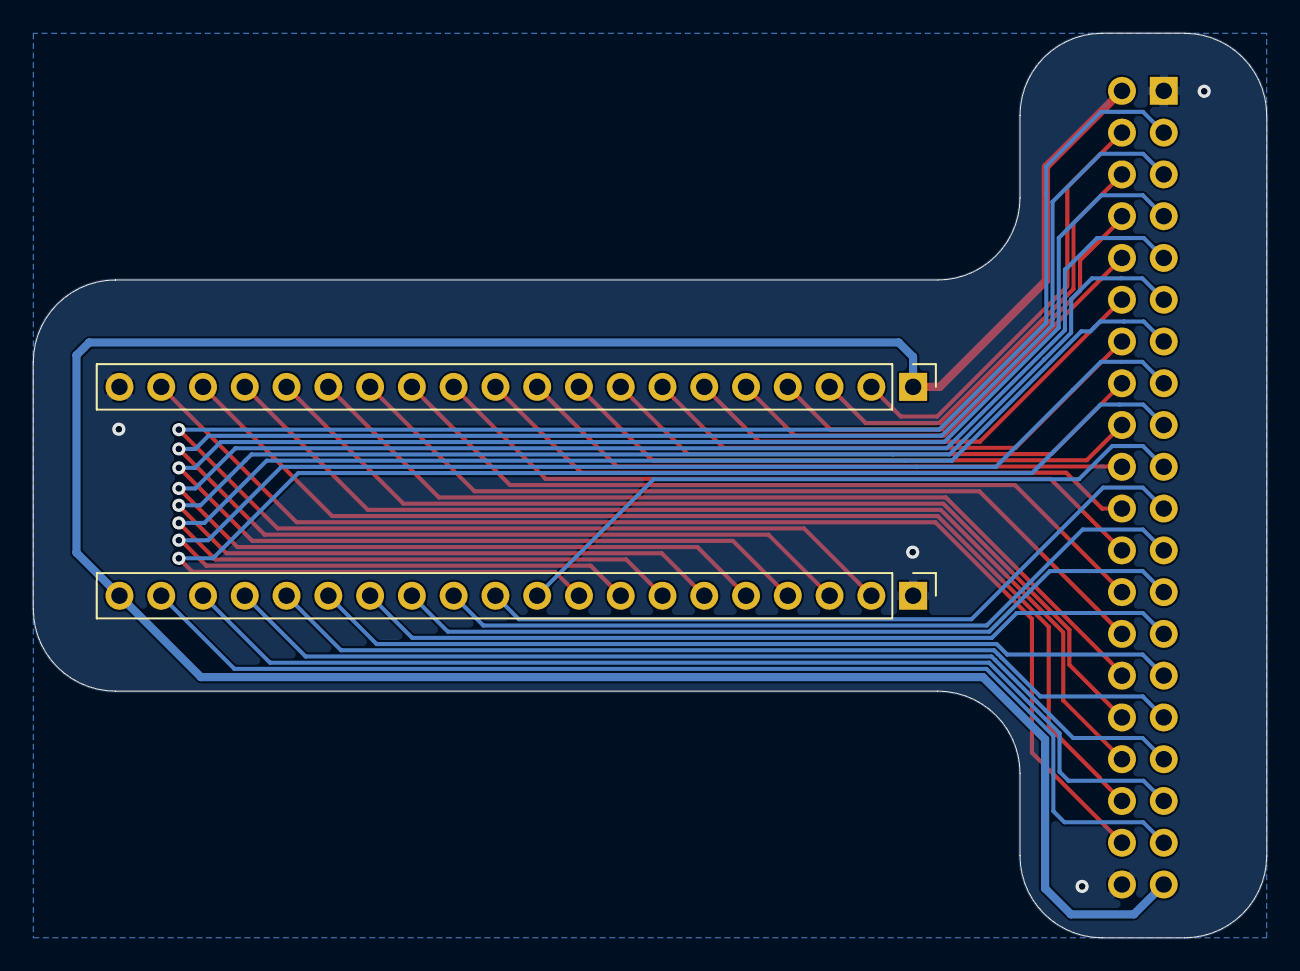
[picture p129: board Breadboard Helper.kicad_pcb from below]

Board: 2 copper layers, 75.0 x 55.0 mm, 3 parts (2 on the bottom side), 38 nets.
