acwright/6502-COB/Hardware/Video Card/Rev 1.0/Video Card.kicad_pcb

## KiCad design Hardware/Video Card/Rev 1.0/Video Card.kicad_pcb (2026-06-16)

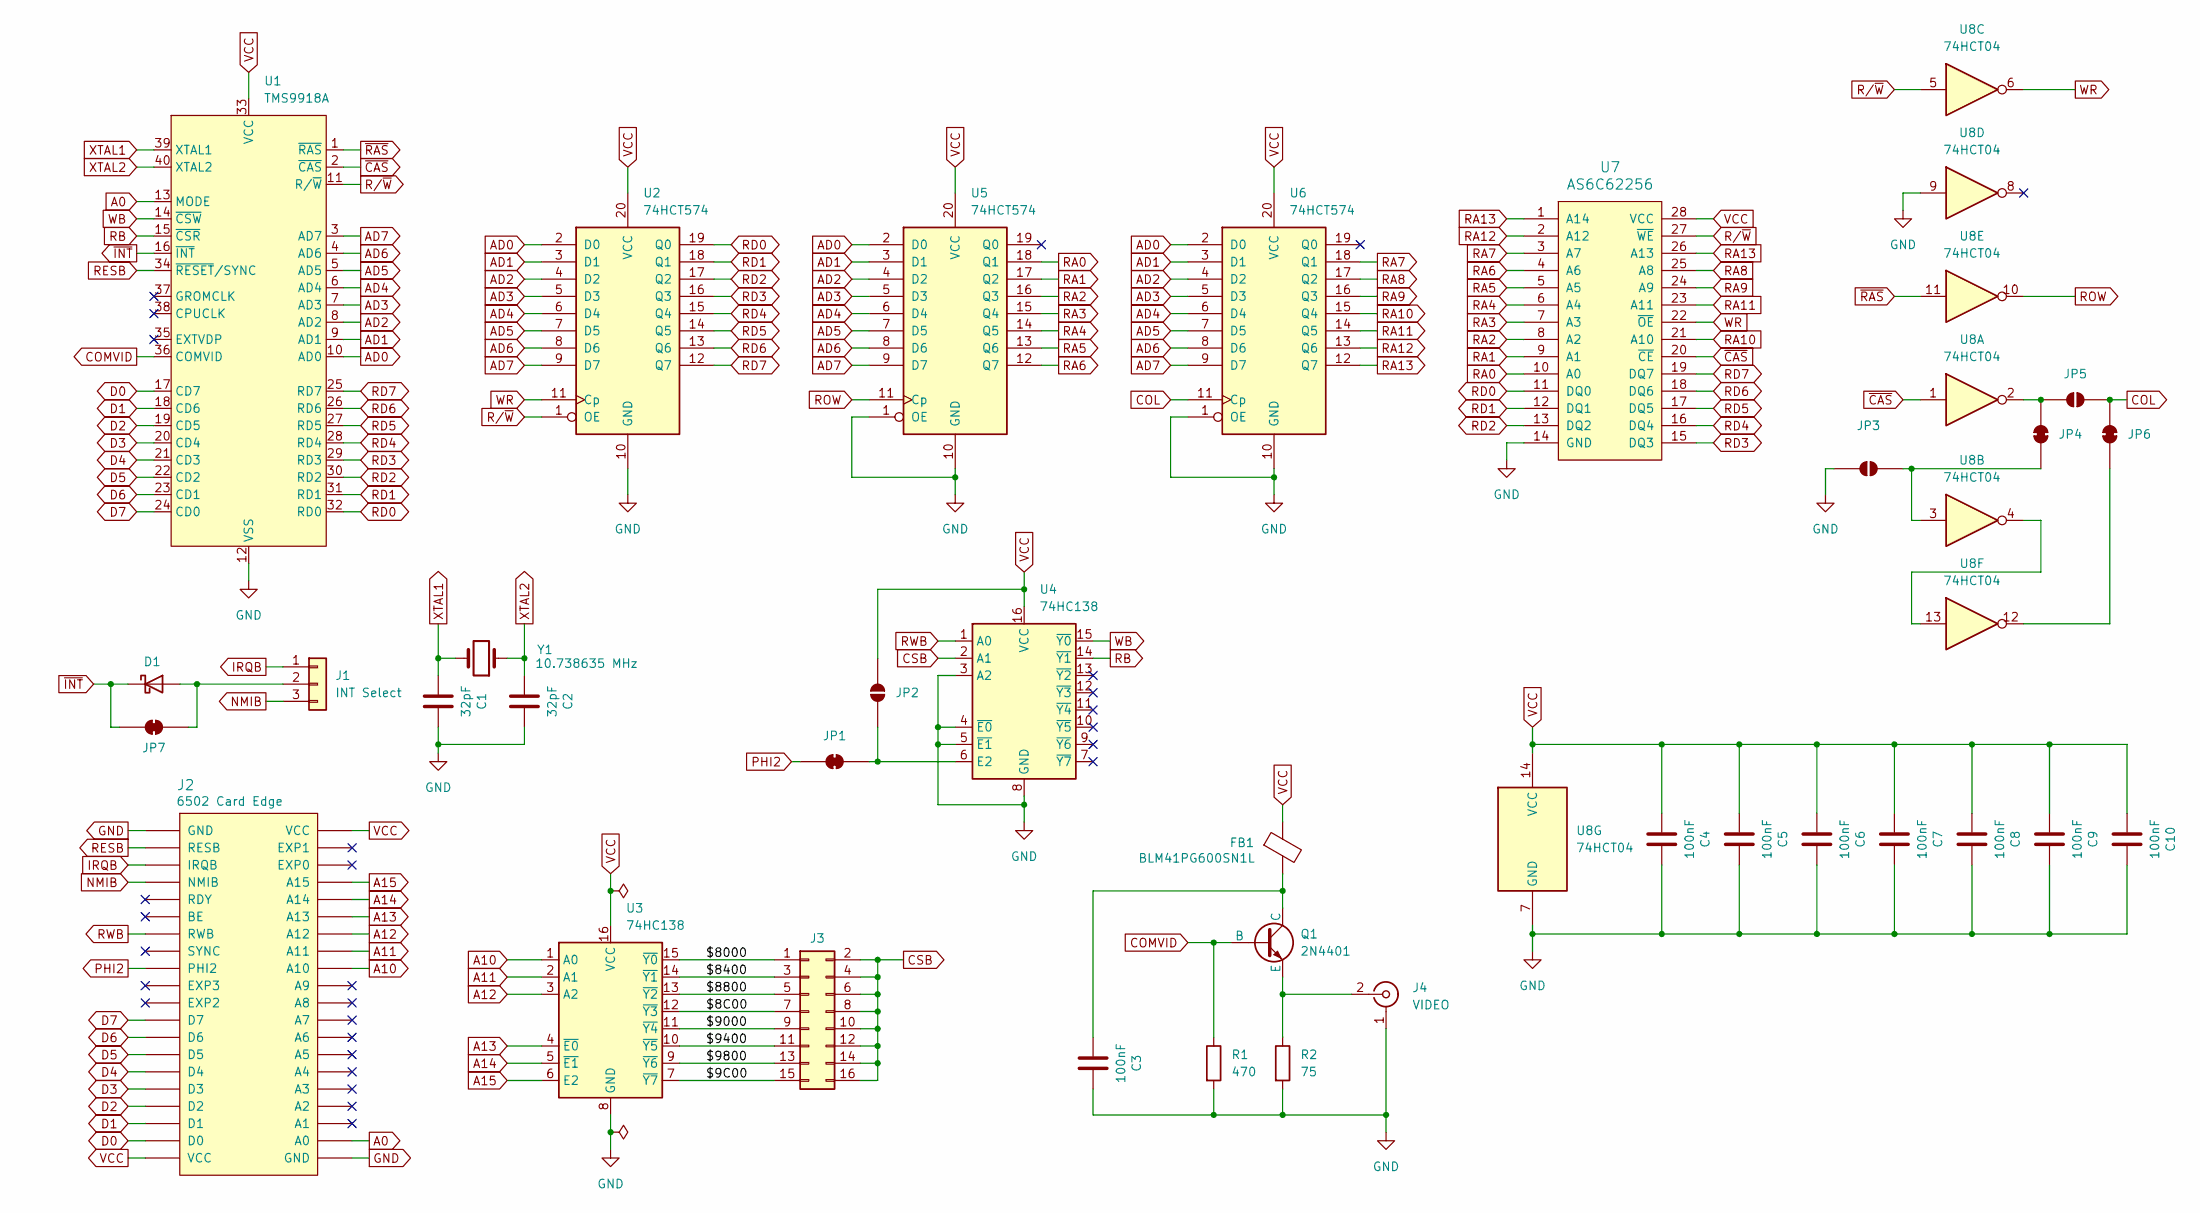
[picture p130: schematic Video Card.kicad_sch, 6502 Video Card]

Parts:
C1, C2: 32pF; C_Disc_D5.0mm_W2.5mm_P2.50mm; LCSC C107114
C3, C4, C5, C6, C7, C8, C9, C10: 100nF; C_0805_2012Metric; LCSC C49678
D1: D_Schottky; D_DO-35_SOD27_P7.62mm_Horizontal
FB1: BLM41PG600SN1L; L_1806_4516Metric; LCSC C85844
J1: INT Select; PinHeader_1x03_P2.54mm_Vertical
J2: 6502 Card Edge
J3: Conn_02x08_Odd_Even; PinHeader_2x08_P2.54mm_Vertical
J4: VIDEO; SWITCHCRAFT_PJRAN1X1U04X
JP1, JP4, JP6, JP7: SolderJumper_2_Bridged; SolderJumper-2_P1.3mm_Bridged_RoundedPad1.0x1.5mm
JP2, JP3, JP5: SolderJumper_2_Open; SolderJumper-2_P1.3mm_Open_RoundedPad1.0x1.5mm
Q1: 2N4401; TO-92_HandSolder
R1: 470; R_0805_2012Metric; LCSC C17710
R2: 75; R_0805_2012Metric; LCSC C17820
U1: TMS9918A; DIP-40_W15.24mm_Socket_LongPads
U2, U5, U6: 74HCT574; SOIC-20W_7.5x12.8mm_P1.27mm; LCSC C6001
U3, U4: 74HC138; SOIC-16_3.9x9.9mm_P1.27mm; LCSC C5602
U7: AS6C62256; DIP-28_W15.24mm_Socket_LongPads
U8: 74HCT04; SO-14_3.9x8.65mm_P1.27mm; LCSC C672096
Y1: 10.738635 MHz; Crystal_HC49-U_Vertical; Mouser 774-MP107-E

Connections:
/$8C00: J3.7, U3.12 (~Y3)
/$9C00: J3.15, U3.7 (~Y7)
/$8000: J3.1, U3.15 (~Y0)
/$8400: J3.3, U3.14 (~Y1)
/$8800: J3.5, U3.13 (~Y2)
/$9000: J3.9, U3.11 (~Y4)
/$9400: J3.11, U3.10 (~Y5)
/$9800: J3.13, U3.9 (~Y6)
A0: J2.A0, U1.13 (MODE)
A10: J2.A10, U3.1 (A0)
A11: J2.A11, U3.2 (A1)
A12: J2.A12, U3.3 (A2)
A13: J2.A13, U3.4 (~E0)
A14: J2.A14, U3.5 (~E1)
A15: J2.A15, U3.6 (E2)
AD0: U1.10 (AD0), U2.2 (D0), U5.2 (D0), U6.2 (D0)
AD1: U1.9 (AD1), U2.3 (D1), U5.3 (D1), U6.3 (D1)
AD2: U1.8 (AD2), U2.4 (D2), U5.4 (D2), U6.4 (D2)
AD3: U1.7 (AD3), U2.5 (D3), U5.5 (D3), U6.5 (D3)
AD4: U1.6 (AD4), U2.6 (D4), U5.6 (D4), U6.6 (D4)
AD5: U1.5 (AD5), U2.7 (D5), U5.7 (D5), U6.7 (D5)
AD6: U1.4 (AD6), U2.8 (D6), U5.8 (D6), U6.8 (D6)
AD7: U1.3 (AD7), U2.9 (D7), U5.9 (D7), U6.9 (D7)
COL: JP5.1 (A), JP6.2 (B), U6.11 (Cp)
COMVID: Q1.2 (B), R1.1, U1.36 (COMVID)
CSB: J3.2, J3.4, J3.6, J3.8, J3.10, J3.12, J3.14, J3.16, U4.2 (A1)
D0: J2.D0, U1.17 (CD7)
D1: J2.D1, U1.18 (CD6)
D2: J2.D2, U1.19 (CD5)
D3: J2.D3, U1.20 (CD4)
D4: J2.D4, U1.21 (CD3)
D5: J2.D5, U1.22 (CD2)
D6: J2.D6, U1.23 (CD1)
D7: J2.D7, U1.24 (CD0)
GND: C1.2, C2.2, C3.2, C4.2, C5.2, C6.2, C7.2, C8.2, C9.2, C10.2, J2.GND, J4.1 (Ext), JP3.2 (B), R1.2, R2.2, U1.12 (VSS), U2.10 (GND), U3.8 (GND), U4.3 (A2), U4.4 (~E0), U4.5 (~E1), U4.8 (GND), U5.1 (OE), U5.10 (GND), U6.1 (OE), U6.10 (GND), U7.14 (GND), U8.7 (GND), U8.9
IRQB: J1.1, J2.IRQB
NMIB: J1.3, J2.NMIB
unnamed: D1.2 (A), J1.2, JP7.2 (B)
unnamed: J4.2 (In), Q1.3 (E), R2.1
unnamed: JP1.1 (A), JP2.2 (B), U4.6 (E2)
unnamed: JP3.1 (A), JP4.1 (A), U8.3
unnamed: JP4.2 (B), JP5.2 (B), U8.2
unnamed: JP6.1 (A), U8.12
unnamed: C3.1, FB1.2, Q1.1 (C)
unnamed: U8.4, U8.13
PHI2: J2.PHI2, JP1.2 (B)
RA0: U5.18 (Q1), U7.10 (A0)
RA1: U5.17 (Q2), U7.9 (A1)
RA2: U5.16 (Q3), U7.8 (A2)
RA3: U5.15 (Q4), U7.7 (A3)
RA4: U5.14 (Q5), U7.6 (A4)
RA5: U5.13 (Q6), U7.5 (A5)
RA6: U5.12 (Q7), U7.4 (A6)
RA7: U6.18 (Q1), U7.3 (A7)
RA8: U6.17 (Q2), U7.25 (A8)
RA9: U6.16 (Q3), U7.24 (A9)
RA10: U6.15 (Q4), U7.21 (A10)
RA11: U6.14 (Q5), U7.23 (A11)
RA12: U6.13 (Q6), U7.2 (A12)
RA13: U6.12 (Q7), U7.1 (A14), U7.26 (A13)
RB: U1.15 (~CSR), U4.14 (~Y1)
RD0: U1.32 (RD0), U2.19 (Q0), U7.11 (DQ0)
RD1: U1.31 (RD1), U2.18 (Q1), U7.12 (DQ1)
RD2: U1.30 (RD2), U2.17 (Q2), U7.13 (DQ2)
RD3: U1.29 (RD3), U2.16 (Q3), U7.15 (DQ3)
RD4: U1.28 (RD4), U2.15 (Q4), U7.16 (DQ4)
RD5: U1.27 (RD5), U2.14 (Q5), U7.17 (DQ5)
RD6: U1.26 (RD6), U2.13 (Q6), U7.18 (DQ6)
RD7: U1.25 (RD7), U2.12 (Q7), U7.19 (DQ7)
RESB: J2.RESB, U1.34 (~RESET/SYNC)
ROW: U5.11 (Cp), U8.10
RWB: J2.RWB, U4.1 (A0)
R/~W: U1.11 (R/~W), U2.1 (OE), U7.27 (~WE), U8.5
VCC: C4.1, C5.1, C6.1, C7.1, C8.1, C9.1, C10.1, FB1.1, J2.VCC, JP2.1 (A), U1.33 (VCC), U2.20 (VCC), U3.16 (VCC), U4.16 (VCC), U5.20 (VCC), U6.20 (VCC), U7.28 (VCC), U8.14 (VCC)
WB: U1.14 (~CSW), U4.15 (~Y0)
WR: U2.11 (Cp), U7.22 (~OE), U8.6
XTAL1: C1.1, U1.39 (XTAL1), Y1.2
XTAL2: C2.1, U1.40 (XTAL2), Y1.1
~CAS: U1.2 (~CAS), U7.20 (~CE), U8.1
~INT: D1.1 (K), JP7.1 (A), U1.16 (~INT)
~RAS: U1.1 (~RAS), U8.11

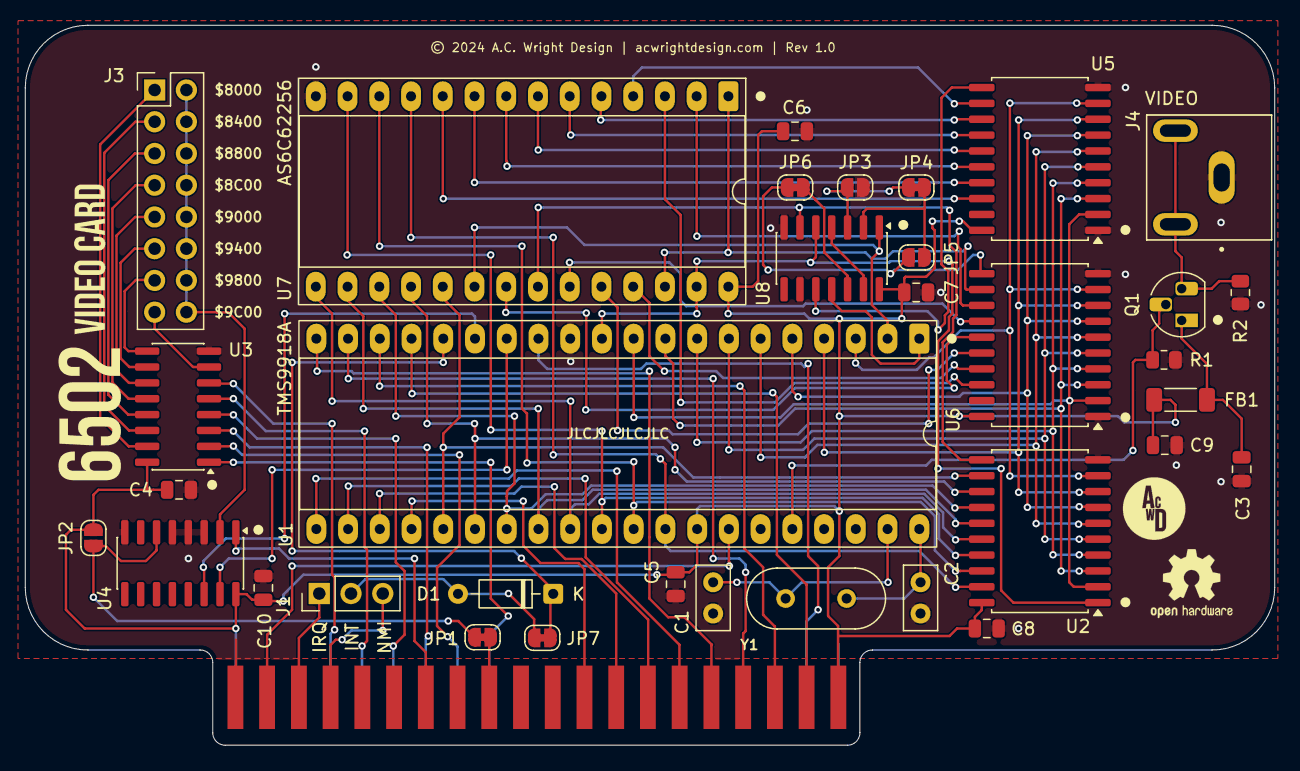
[picture p131: board Video Card.kicad_pcb from above]

Board: 2 copper layers, 100.0 x 57.6 mm, 35 parts (0 on the bottom side), 81 nets.
