acwright/6502-COB/Hardware/Memory Card/Rev 1.0/Memory Card.kicad_pcb

## KiCad design Hardware/Memory Card/Rev 1.0/Memory Card.kicad_pcb (2026-06-16)

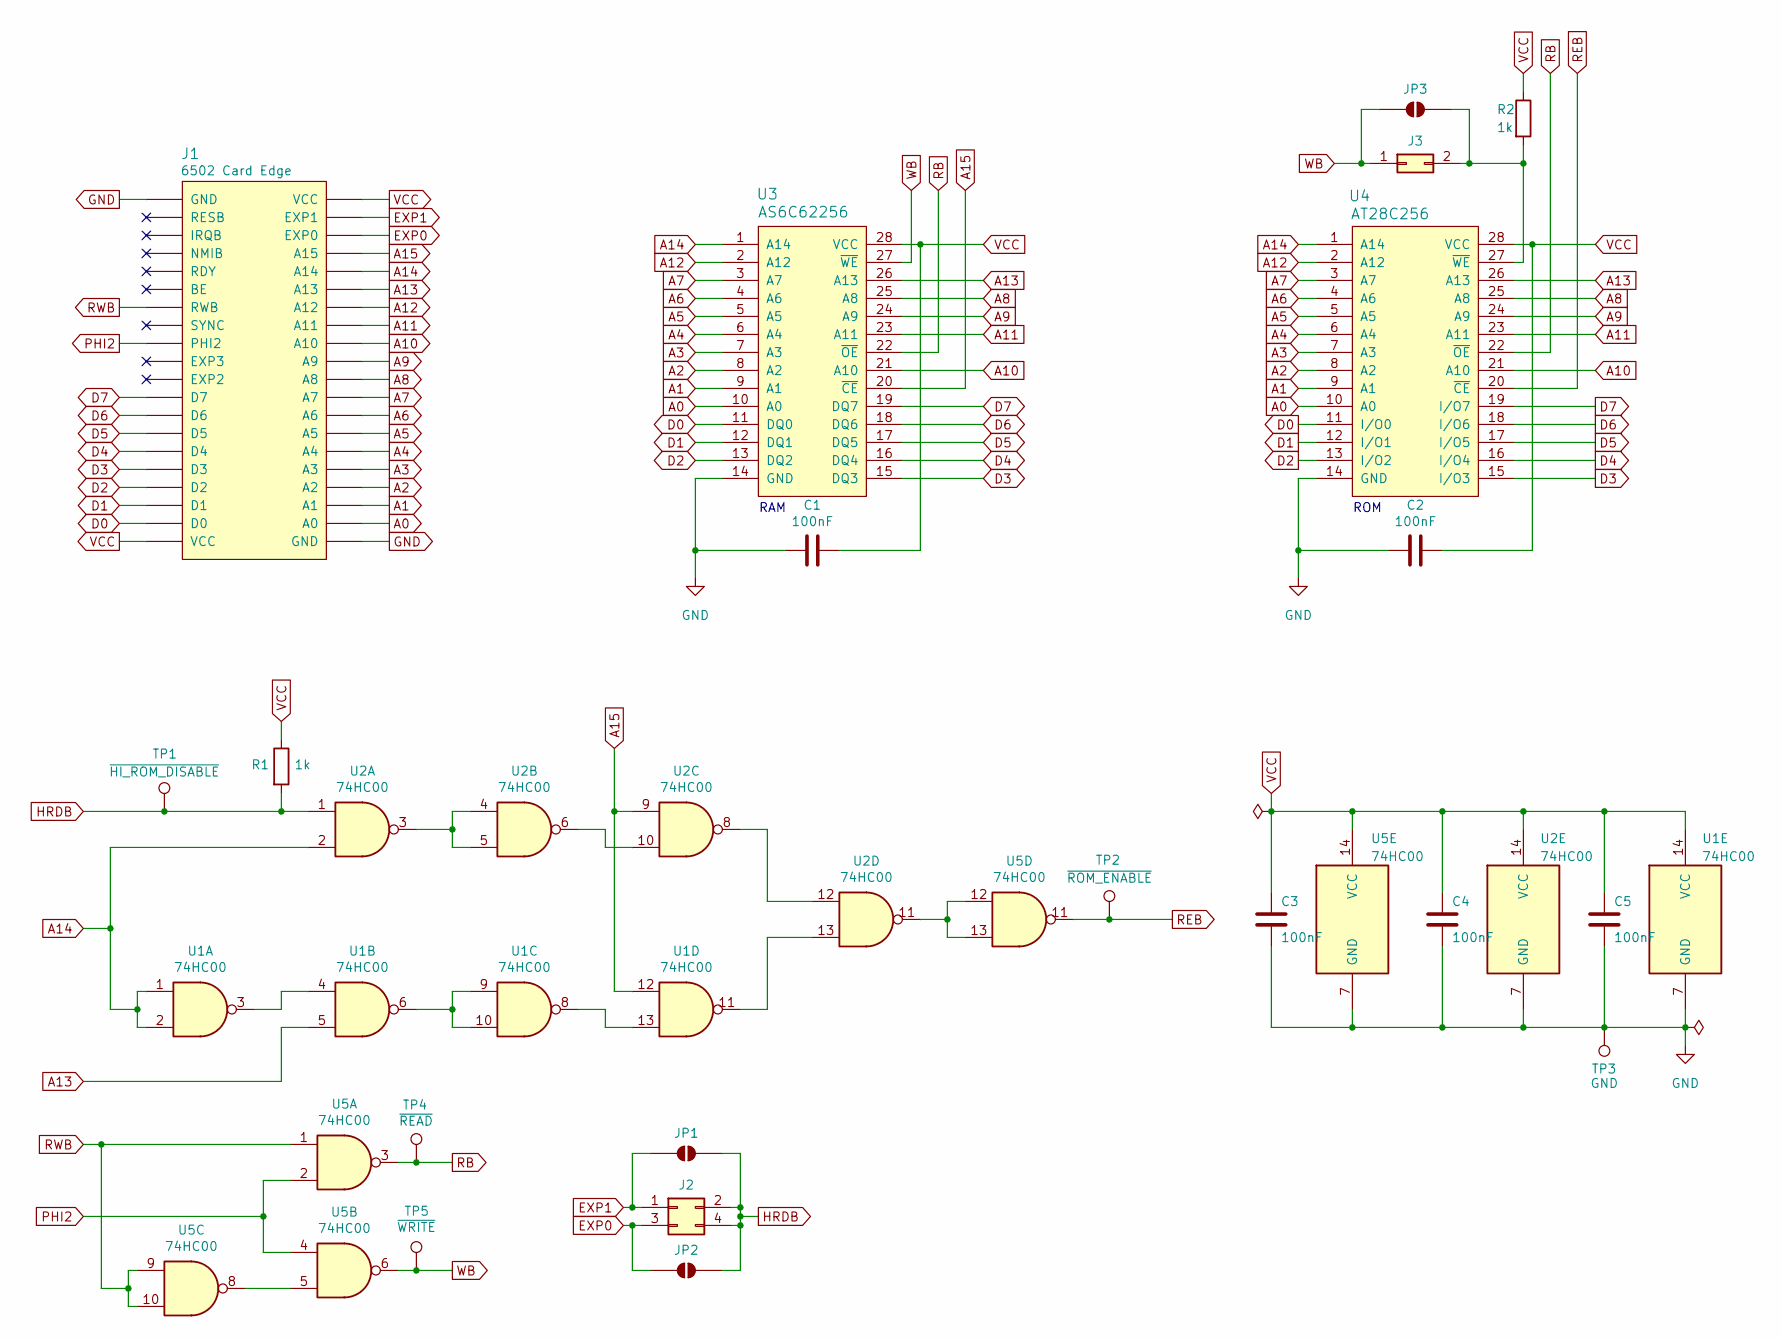
[picture p132: schematic Memory Card.kicad_sch, 6502 Memory Card]

Parts:
C1, C2, C3, C4, C5: 100nF; C_0805_2012Metric; LCSC C49678
J1: 6502 Card Edge
J2: Conn_02x02_Odd_Even; PinHeader_2x02_P2.54mm_Vertical
J3: Conn_02x01; PinHeader_1x02_P2.54mm_Vertical
JP1, JP2, JP3: SolderJumper_2_Open; SolderJumper-2_P1.3mm_Open_RoundedPad1.0x1.5mm
R1, R2: 1k; R_0805_2012Metric; LCSC C17513
TP1: ~{HI_ROM_DISABLE}; TestPoint_Pad_1.0x1.0mm
TP2: ~{ROM_ENABLE}; TestPoint_Pad_1.0x1.0mm
TP3: GND; TestPoint_Pad_1.0x1.0mm
TP4: ~{READ}; TestPoint_Pad_1.0x1.0mm
TP5: ~{WRITE}; TestPoint_Pad_1.0x1.0mm
U1, U2, U5: 74HC00; SOIC-14_3.9x8.7mm_P1.27mm; LCSC C5586
U3: AS6C62256; DIP-28_W15.24mm_Socket_LongPads
U4: AT28C256; DIP-28_W15.24mm_Socket_LongPads

Connections:
A0: J1.A0, U3.10 (A0), U4.10 (A0)
A1: J1.A1, U3.9 (A1), U4.9 (A1)
A2: J1.A2, U3.8 (A2), U4.8 (A2)
A3: J1.A3, U3.7 (A3), U4.7 (A3)
A4: J1.A4, U3.6 (A4), U4.6 (A4)
A5: J1.A5, U3.5 (A5), U4.5 (A5)
A6: J1.A6, U3.4 (A6), U4.4 (A6)
A7: J1.A7, U3.3 (A7), U4.3 (A7)
A8: J1.A8, U3.25 (A8), U4.25 (A8)
A9: J1.A9, U3.24 (A9), U4.24 (A9)
A10: J1.A10, U3.21 (A10), U4.21 (A10)
A11: J1.A11, U3.23 (A11), U4.23 (A11)
A12: J1.A12, U3.2 (A12), U4.2 (A12)
A13: J1.A13, U1.5, U3.26 (A13), U4.26 (A13)
A14: J1.A14, U1.1, U1.2, U2.2, U3.1 (A14), U4.1 (A14)
A15: J1.A15, U1.12, U2.9, U3.20 (~CE)
D0: J1.D0, U3.11 (DQ0), U4.11 (I/O0)
D1: J1.D1, U3.12 (DQ1), U4.12 (I/O1)
D2: J1.D2, U3.13 (DQ2), U4.13 (I/O2)
D3: J1.D3, U3.15 (DQ3), U4.15 (I/O3)
D4: J1.D4, U3.16 (DQ4), U4.16 (I/O4)
D5: J1.D5, U3.17 (DQ5), U4.17 (I/O5)
D6: J1.D6, U3.18 (DQ6), U4.18 (I/O6)
D7: J1.D7, U3.19 (DQ7), U4.19 (I/O7)
EXP0: J1.EXP0, J2.3, JP2.1 (A)
EXP1: J1.EXP1, J2.1, JP1.1 (A)
GND: C1.2, C2.2, C3.2, C4.2, C5.2, J1.GND, TP3.1 (1_1), U1.7 (GND), U2.7 (GND), U3.14 (GND), U4.14 (GND), U5.7 (GND)
HRDB: J2.2, J2.4, JP1.2 (B), JP2.2 (B), R1.2, TP1.1 (1_1), U2.1
unnamed: J3.2, JP3.2 (B), R2.2, U4.27 (~WE)
unnamed: U1.3, U1.4
unnamed: U1.6, U1.9, U1.10
unnamed: U1.11, U2.13
unnamed: U1.8, U1.13
unnamed: U2.3, U2.4, U2.5
unnamed: U2.6, U2.10
unnamed: U2.11, U5.12, U5.13
unnamed: U2.8, U2.12
unnamed: U5.5, U5.8
PHI2: J1.PHI2, U5.2, U5.4
RB: TP4.1 (1_1), U3.22 (~OE), U4.22 (~OE), U5.3
REB: TP2.1 (1_1), U4.20 (~CE), U5.11
RWB: J1.RWB, U5.1, U5.9, U5.10
VCC: C1.1, C2.1, C3.1, C4.1, C5.1, J1.VCC, R1.1, R2.1, U1.14 (VCC), U2.14 (VCC), U3.28 (VCC), U4.28 (VCC), U5.14 (VCC)
WB: J3.1, JP3.1 (A), TP5.1 (1_1), U3.27 (~WE), U5.6

Notes on the sheet:
RAM
ROM

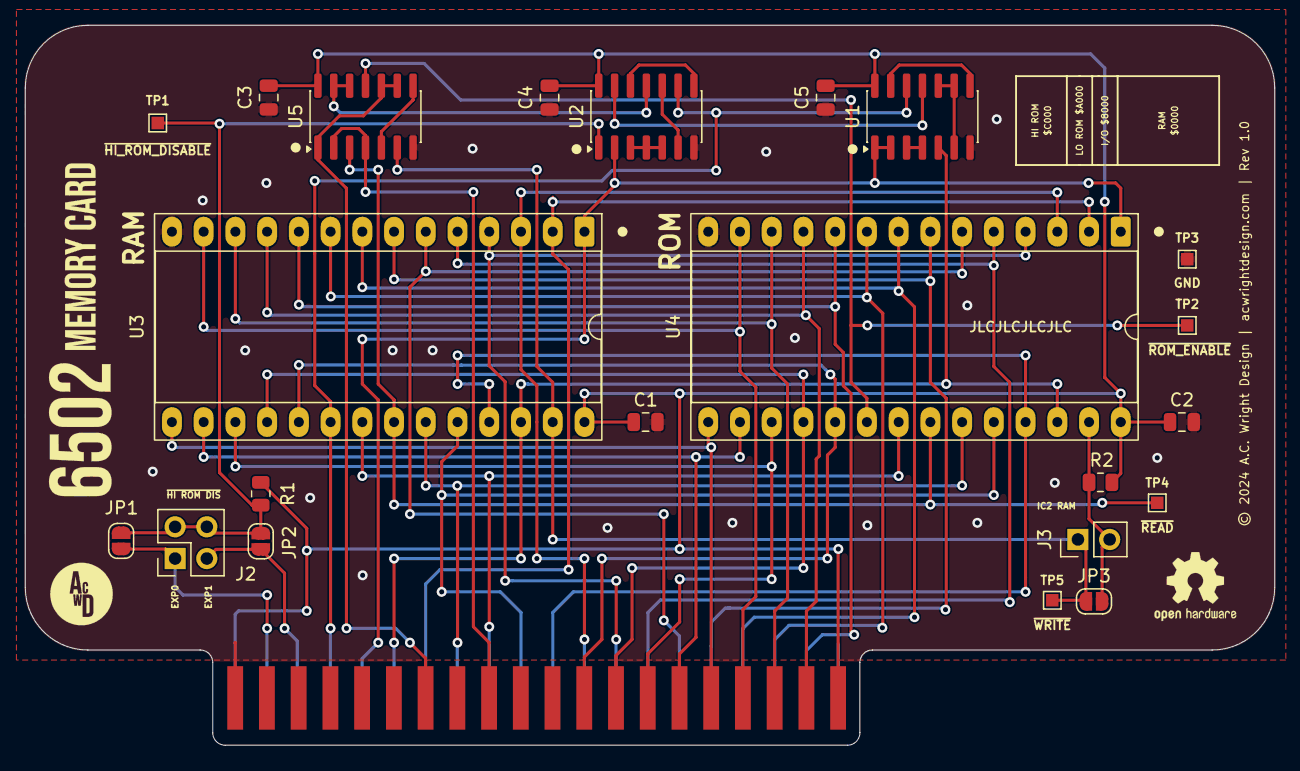
[picture p133: board Memory Card.kicad_pcb from above]

Board: 2 copper layers, 100.0 x 57.6 mm, 23 parts (0 on the bottom side), 44 nets.
