acwright/6502-COB/Hardware/VERA Helper/Rev 1.0/VERA Helper.kicad_pcb

## KiCad design Hardware/VERA Helper/Rev 1.0/VERA Helper.kicad_pcb (2026-06-16)

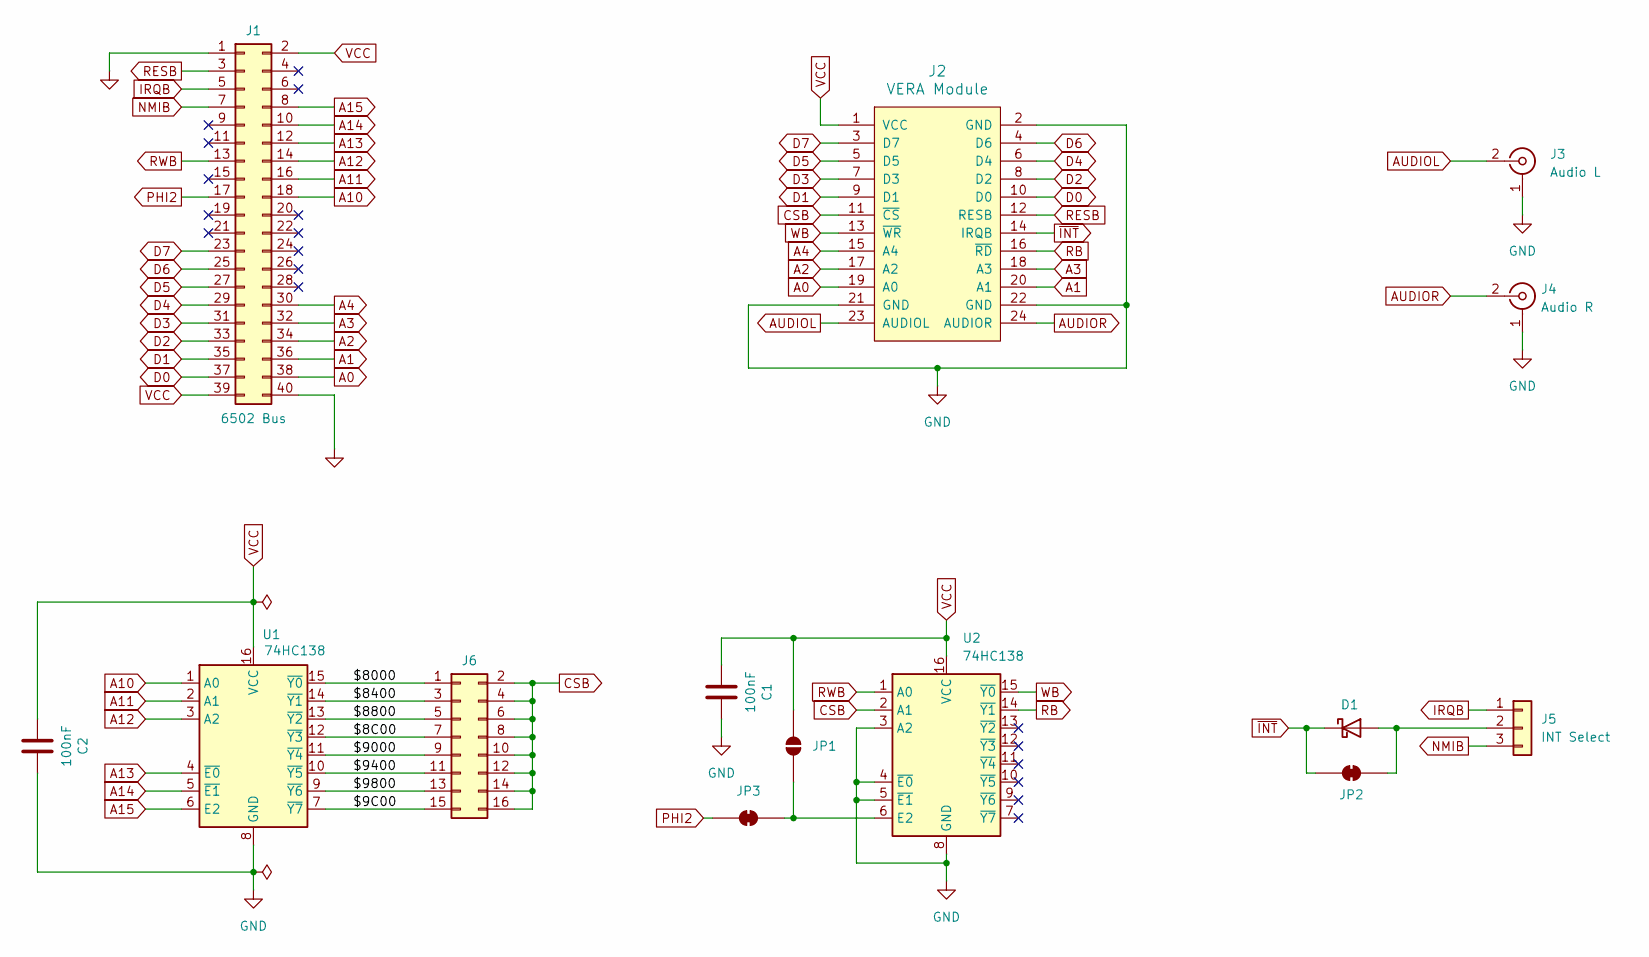
[picture p134: schematic VERA Helper.kicad_sch, 6502 VERA Helper]

Parts:
C1, C2: 100nF; C_Disc_D5.0mm_W2.5mm_P5.00mm
D1: D_Schottky; D_DO-35_SOD27_P7.62mm_Horizontal
J1: 6502 Bus; 6502 Bus Connector
J2: VERA Module; PinHeader_2x12_P2.54mm_Vertical
J3: Audio L; SWITCHCRAFT_PJRAN1X1U02X
J4: Audio R; SWITCHCRAFT_PJRAN1X1U02X
J5: INT Select; PinHeader_1x03_P2.54mm_Vertical
J6: Conn_02x08_Odd_Even; PinHeader_2x08_P2.54mm_Vertical
JP1: SolderJumper_2_Open; SolderJumper-2_P1.3mm_Open_RoundedPad1.0x1.5mm
JP2, JP3: SolderJumper_2_Bridged; SolderJumper-2_P1.3mm_Bridged_RoundedPad1.0x1.5mm
U1, U2: 74HC138; DIP-16_W7.62mm_Socket_LongPads

Connections:
/$8C00: J6.7, U1.12 (~Y3)
/$9C00: J6.15, U1.7 (~Y7)
/$8000: J6.1, U1.15 (~Y0)
/$8400: J6.3, U1.14 (~Y1)
/$8800: J6.5, U1.13 (~Y2)
/$9000: J6.9, U1.11 (~Y4)
/$9400: J6.11, U1.10 (~Y5)
/$9800: J6.13, U1.9 (~Y6)
A0: J1.38, J2.19 (A0)
A1: J1.36, J2.20 (A1)
A2: J1.34, J2.17 (A2)
A3: J1.32, J2.18 (A3)
A4: J1.30, J2.15 (A4)
A10: J1.18, U1.1 (A0)
A11: J1.16, U1.2 (A1)
A12: J1.14, U1.3 (A2)
A13: J1.12, U1.4 (~E0)
A14: J1.10, U1.5 (~E1)
A15: J1.8, U1.6 (E2)
AUDIOL: J2.23 (AUDIOL), J3.2 (In)
AUDIOR: J2.24 (AUDIOR), J4.2 (In)
CSB: J2.11 (~CS), J6.2, J6.4, J6.6, J6.8, J6.10, J6.12, J6.14, J6.16, U2.2 (A1)
D0: J1.37, J2.10 (D0)
D1: J1.35, J2.9 (D1)
D2: J1.33, J2.8 (D2)
D3: J1.31, J2.7 (D3)
D4: J1.29, J2.6 (D4)
D5: J1.27, J2.5 (D5)
D6: J1.25, J2.4 (D6)
D7: J1.23, J2.3 (D7)
GND: C1.2, C2.2, J1.1, J1.40, J2.2 (GND), J2.21 (GND), J2.22 (GND), J3.1 (Ext), J4.1 (Ext), U1.8 (GND), U2.3 (A2), U2.4 (~E0), U2.5 (~E1), U2.8 (GND)
IRQB: J1.5, J5.1
NMIB: J1.7, J5.3
unnamed: D1.2 (A), J5.2, JP2.2 (B)
unnamed: JP1.2 (B), JP3.1 (A), U2.6 (E2)
PHI2: J1.17, JP3.2 (B)
RB: J2.16 (~RD), U2.14 (~Y1)
RESB: J1.3, J2.12 (RESB)
RWB: J1.13, U2.1 (A0)
VCC: C1.1, C2.1, J1.2, J1.39, J2.1 (VCC), JP1.1 (A), U1.16 (VCC), U2.16 (VCC)
WB: J2.13 (~WR), U2.15 (~Y0)
~INT: D1.1 (K), J2.14 (IRQB), JP2.1 (A)

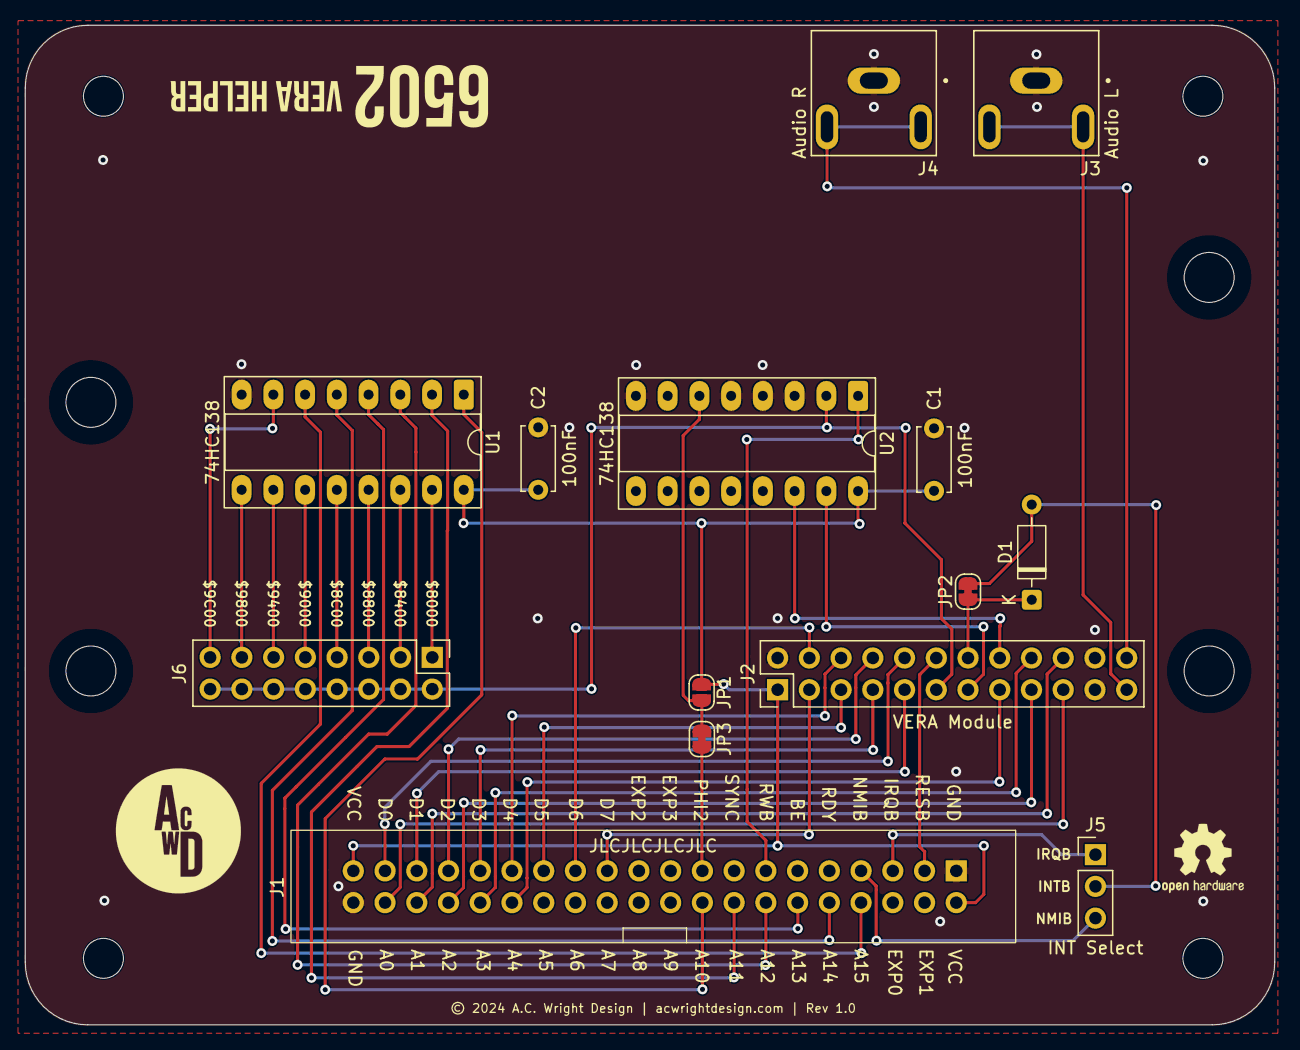
[picture p135: board VERA Helper.kicad_pcb from above]

Board: 2 copper layers, 100.0 x 80.0 mm, 18 parts (0 on the bottom side), 42 nets.

Other parts of the board:
H1, H2, H3, H4: MountingHole; MountingHole_3.2mm_M3
